LieBtrau/MegawattKS_Radio_Design_101/doc/RFampPwrGain.PDF

### RF Amplifier Power Gain

In radio frequency circuits, the power gain of an amplifier is often more important than the voltage gain. This paper covers calculation of power gain, and provides examples to illustrate important points.

Transducer Power Gain

The most commonly used definition of power gain is the so-called transducer gain GT defined as:

GT =

Ptoad
Pavail

where Pload is the power delivered to the load by the amplifier, and Pavail is the power available from the source. The latter is the same as the power delivered to the amplifier input by the source under the condition that the amplifier input impedance is matched to the source impedance
(i.e. Ri = Rs for the case of real impedances, or Zi = Z
*

s when working with complex impedances).

Assuming matched resistive impedances (Ri = Rs), the power available (power delivered to a matched amplifier input) can be written as:

Pavail = Pin−matched =

Vi

2
Ri

The power delivered by the amplifier's output to a load resistance RL (which may or may not be matched to the amplifier's output resistance Ro) is:

Pload =

VL

2
RL

Combining these two expressions, we find:

GT =

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
GT = AVloaded
2

Ri
RL

The maximum power will be delivered to the load by the amplifier if the load is matched to the amplifier's output impedance (ZL = Zo
*

), or, for the case of purely resistive output and load impedances, RL = Ro. Hence, the maximum transducer gain GTmaxoccurs when the output is matched as well as the input.

Examples:

Consider the case of a common-base amplifier with gm = 1/35 (Ri = 35Ohms), and Ro = RC = 1800 Ohms. Assume that the input is matched to the source (i.e. Ri = Rs ). The power gain for this amplifier under conditions of various load resistances is examined below.

Case 1: High impedance load

Suppose that the amplifier is hooked to a very high impedance load such as the input to an oscilloscope with RL = 10 MOhm. Then:

AVno-load = gm Rc = 1/35 1800 = 51.43
and
AVloaded = AVno-load | = 51.42 | (34.2 dB)* RL
RL+Ro

which is quite healthy. However, the power gain GT is found to be only:

GT = A
2
Vloaded | (-20 dB)* Ri
RL

= 51.4

2 35
10

7 = 0.01

Case 2: Low impedance load

Now suppose the amplifier output is connected directly to a piece of RF test equipment with a 50 Ohm input impedance. The loaded voltage gain is now:

AVloaded = AVno-load | (2.9 dB)* ⁵⁰
50+1800 = 1.39

which is quite low. The power gain in this case is also low:

GT = V
2
Vloaded | (1.3 dB)* Ri
RL

= 1.39

2 35
50 = 1.35

Case 3: Matched load

Finally, suppose that Ro is matched to RL (perhaps using an impedance matching network to transform a 50 Ohm load to 1800 Ohms). Then, the voltage and power gains are found to be:

AVloaded = AVno-load | = AVno-load | = 25.7 | (28.2 dB)* ¹⁸⁰⁰
1800+1800

1
2
and
GT = GTmax = A
2
Vloaded | (11 dB)* Ri
RL

= 25.7

2 35
1800 = 12.86

* Recall that voltage gain in dB is defined as 20 log (AV) and power gain in dB is 10 log (Gp).
The two are equal if and only if the input impedance equals the output impedance, which is not true here.
