LieBtrau/MegawattKS_Radio_Design_101/VFO/doc/Clapp Oscillator_ Frequency Formula And Circuit Diagram _ Electrical4U.pdf

## Clapp Oscillator: Frequency Formula And Circuit Diagram | Electrical4U

Electrical4U

Key learnings:

- Clapp Oscillator Definition: A Clapp oscillator (also known as a Gouriet oscillator) is defined as an LC electronic oscillator that uses an inductor and three capacitors to set the oscillator’s frequency.
- Frequency Formula: The frequency of the Clapp oscillator is determined by a specific formula that takes into account the values of the inductor and capacitors.
- Circuit Diagram: The circuit diagram of the Clapp oscillator includes an inductor, three capacitors, a transistor (or other gain element), and a positive feedback network.
- Role of Capacitor C3: The additional capacitor C3 makes the Clapp oscillator more stable than the Colpitts oscillator by allowing frequency variation without affecting the feedback ratio.
- Frequency Stability: Enclosing the circuit in a temperature-controlled chamber and using a Zener diode can enhance the frequency stability of the Clapp oscillator.

## What is a Clapp Oscillator?

A Clapp oscillator (also known as a Gouriet oscillator) is an LC electronic oscillator that uses a particular combination of an inductor and three capacitors to set the oscillator’s frequency (see circuit diagram below). LC oscillators use a transistor (or vacuum tube or other gain element) and a positive feedback network.

A Clapp oscillator is a type of Colpitts oscillator (https://www.electrical4u.com/colpitts-oscillator/) with an extra capacitor (C3) added in series with the inductor (https://www.electrical4u.com/what-is-inductor-and-inductance-theory-of-inductor/) in the tank circuit, as shown in the circuit diagram below.

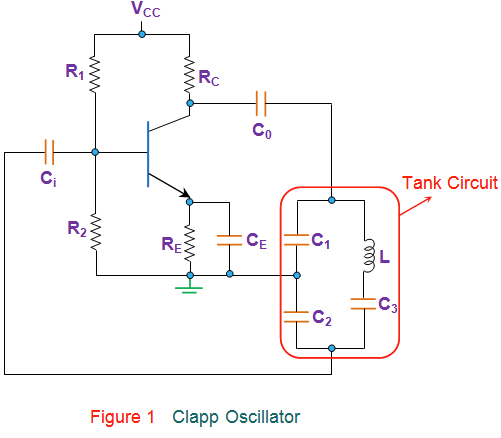
[picture p69: figure]

Apart from the presence of an extra capacitor, (https://www.electrical4u.com/working-principle-of-a-capacitor/) all other components and their connections remain similar to that in the case of Colpitts oscillator.

Hence, the working of this circuit is almost identical to that of the Colpitts, where the feedback ratio governs the generation and sustainity of the oscillations. However the frequency of oscillation in the case of a Clapp oscillator is given by

Usually, the value of C3 is chosen to be much smaller than the other two capacitors. (https://www.electrical4u.com/working-principle-of-a-capacitor/) This is because, at higher frequencies, the smaller the C3, the larger will be the inductor, (https://www.electrical4u.com/what-is-inductor-and-inductance-theory-of-inductor/) which eases the implementation as well as reduces the influence of stray inductance. (https://www.electrical4u.com/what-is-inductor-and-inductance-theory-of-inductor/)

Nevertheless, the value of C3 is to be chosen with utmost care. This is because, if it is chosen to be very small, then the oscillations will not be generated as the L-C branch will fail to have a net inductive reactance.

However, here it is to be noted that when C3 is chosen to be smaller in comparison with C1 and C2, the net capacitance governing the circuit will be more dependent on it.

Thus the equation for the frequency can be approximated as

Further, the presence of this extra capacitance (https://www.electrical4u.com/what-is-capacitor/) will make the Clapp oscillator preferable over Colpitts when there is a need to vary the frequency

Clapp Oscillator: Frequency Formula And Circuit Diagram | Electrical4U | https://www.electrical4u.com/clapp-oscillator/
1 of 2 | 2025-08-27, 16:45

as is the case with Variable Frequency Oscillator (VCO). The reason behind this can be explained as follows.

In the case of the Colpitts oscillator, (https://www.electrical4u.com/colpitts-oscillator/) the capacitors C1 and C2 need to be varied in order to vary their frequency of operation. However during this process, even the feedback ratio of the oscillator (https://www.electrical4u.com/what-is-an-oscillator/) changes which in turn affects its output waveform.

One solution to this problem is to make both C1 and C2 to be fixed in nature while achieving the variation in frequency using a separate variable capacitor.

As could be guessed, this is what the C3 does in the case of the Clapp oscillator, which in turn makes it more stable over Colpitts in terms of frequency.

You can further improve the circuit’s frequency stability by placing it in a temperature-controlled chamber and using a Zener diode (https://www.electrical4u.com/what-is-zener-diode/) to maintain a constant supply voltage. (https://www.electrical4u.com/voltage-or-electric-potential-difference/)

Additionally, the values of capacitors C1 and C2 are affected by stray capacitances, unlike C3.

This means that the resonant frequency of the circuit would be affected by the stray capacitances if one had a circuit with just C1 and C2, as in the case of Colpitts oscillator.

However, if there is C3 in the circuit, then the changes in the values of C1 and C2 would not vary the resonant frequency much, as the dominant term would then be C3.

Next, it is seen that the Clapp oscillators are comparatively compact as they employ a relatively small capacitor (https://www.electrical4u.com/working-principle-of-a-capacitor/) to tune the oscillator over a wide frequency band. This is because, here, even a slight change in the value of the capacitance varies the frequency of the circuit up to a great extent.

Further, they exhibit a high Q factor (https://www.electrical4u.com/q-factor/) with a high L/C ratio and lesser circulating current (https://www.electrical4u.com/electric-current-and-theory-of-electricity/) in comparison with Colpitts oscillators. (https://www.electrical4u.com/colpitts-oscillator/)

Lastly, it is to be noted that these oscillators (https://www.electrical4u.com/what-is-an-oscillator/) are highly reliable and are hence preferred in spite of having a limited range of frequency of operation.

Clapp Oscillator: Frequency Formula And Circuit Diagram | Electrical4U | https://www.electrical4u.com/clapp-oscillator/
2 of 2 | 2025-08-27, 16:45
