LieBtrau/MegawattKS_Radio_Design_101/IF1_amp/doc/Cascode.pdf

1

## The Cascode Amplifier

A two transistor amplifier used to obtain simultaneously:
1. Reasonably high input impedance.
2. Reasonable voltage gain.
3. Wide bandwidth.

None of the conventional single transistor designs will satisfy all of the criteria above.
The cascode amplifier will satisfy all of these criteria.
A cascode is a CE Stage cascaded with a CB Stage.

(Historical Note: the cascode amplifier was a cascade of grounded cathode and grounded grid vacuum tube stages – hence the
name “cascode,” which has remained in modern terminology.)

## The Cascode Amplifier

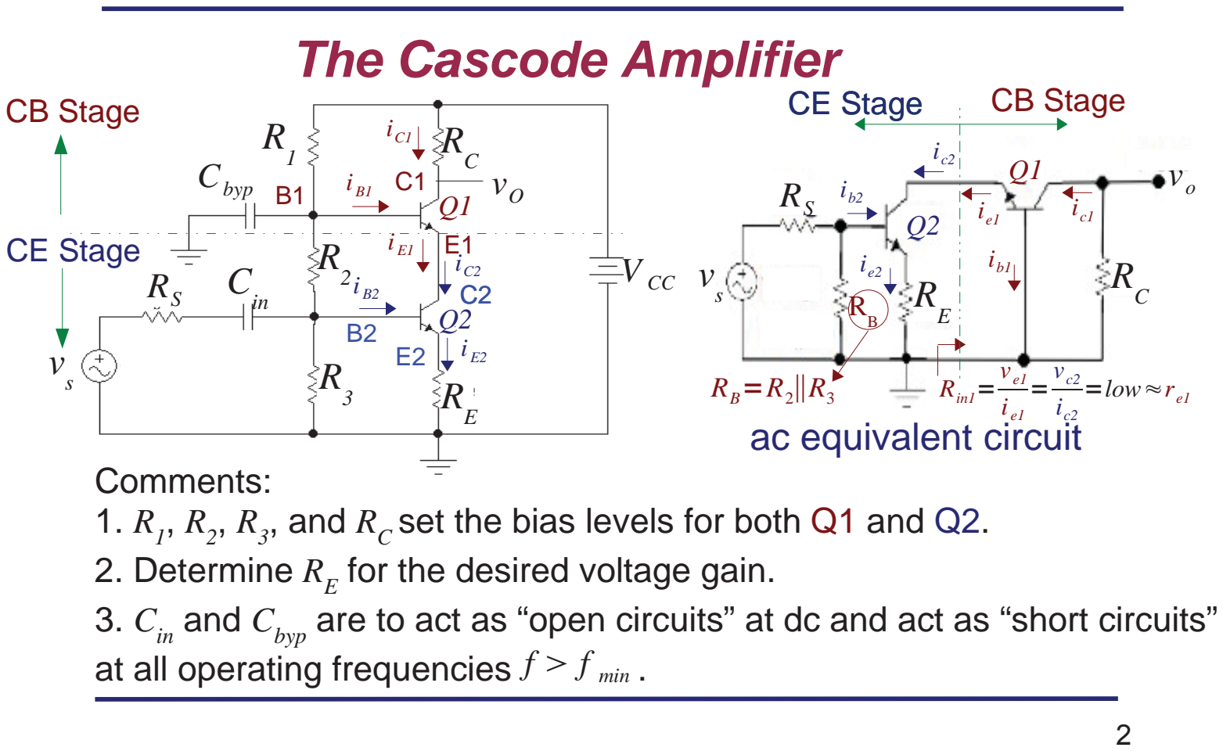
[picture p78: page 2]

2

f

f min

ac equivalent circuit

ib2

ie2

ic2

ic1

ib1

ie1

Rin1

ve1

i e1

vc2

ic2

low
r e1

R
B

R
B
R
2

R3

CE Stage CB Stage

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
CE Stage

Q2

Q1
R
S
i | v-out B1

i B2

i E1
iC2

i E2
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
V CC

Cbyp

CB Stage

CE Stage

B1 | C1

E1

C2

| E2

B2

Q1

Q2

R
S

iC1

Comments:
1.
R

1, R

2, R

3, and
R

C set the bias levels for both Q1 and Q2.
2. Determine
R

E for the desired voltage gain.
3.
Cin and

Cbyp are to act as “open circuits” at dc and act as “short circuits”
at all operating frequencies | .

## Cascode Mid-Band Small Signal Model

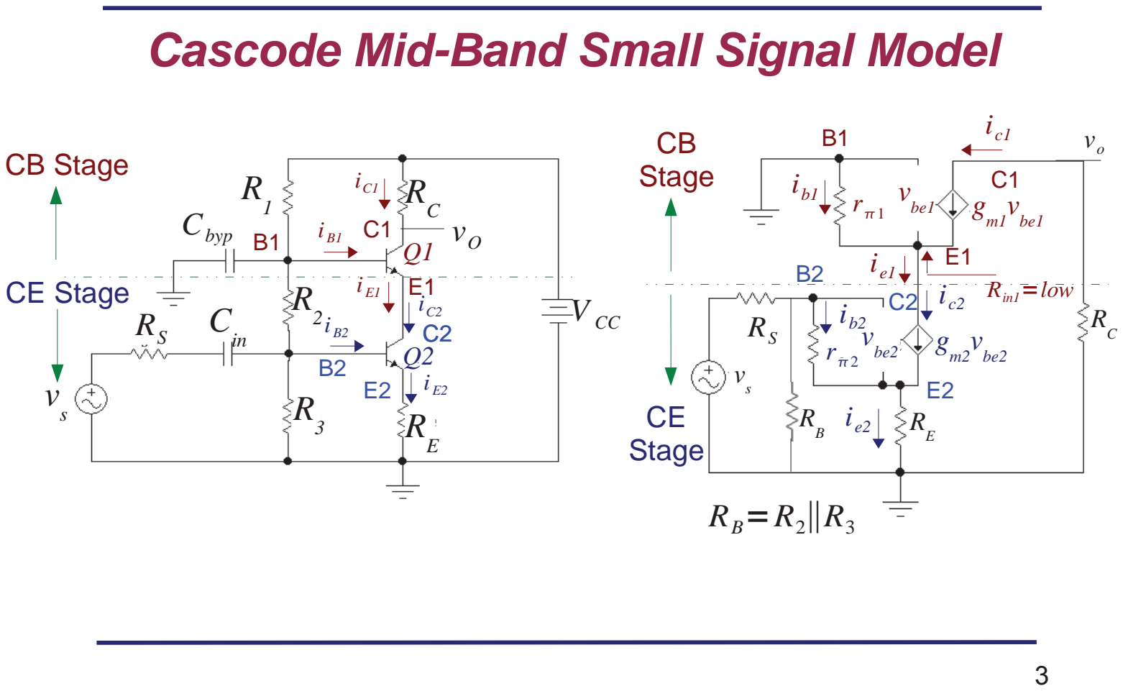
[picture p79: page 3]

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
Rin1

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
1 | g
m

v
1

g
m

v
2

v CB
o
Stage

CE
Stage

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
i | v-out B1

i B2

i E1 iC2

i E2
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
V CC

Cbyp

CB Stage

CE Stage

B1 | C1

E1

C2

| E2

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
## Cascode Small Signal Analysis

ie1

ic2

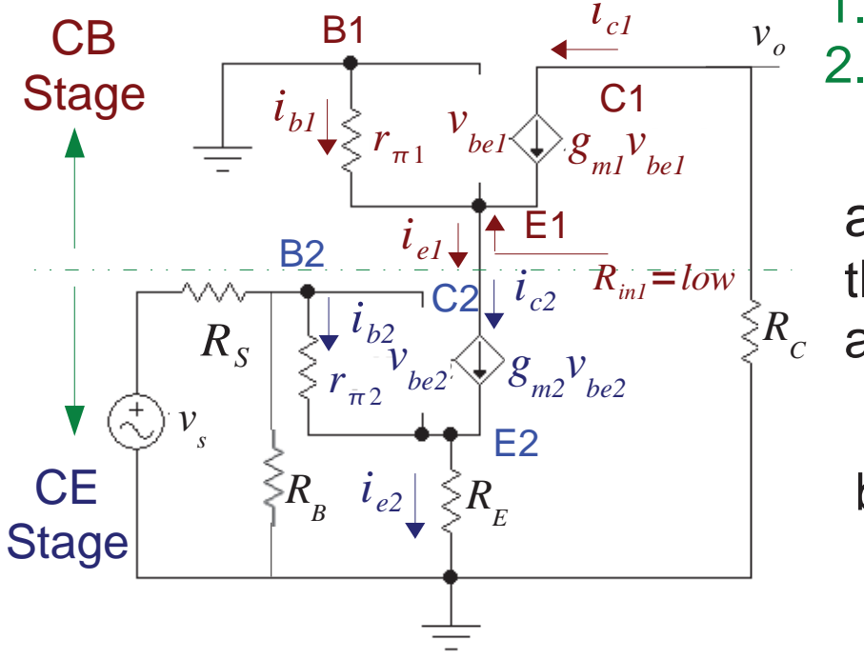
[picture p80: figure]
Rin1; low; Stage; CE Stage

b. The base current of the CB Stage is:
c. Hence, both stages have about same collector current and same
g
m, re, rπ

ib1

ie1
1

ic2
1

OBSERVATIONS

ic1

ic2

gm1

g m2
g
m
re1
r e2
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
a. The emitter current of the CB Stage is the collector current of the CE Stage. (This also holds for the dc bias current.)
1. Show reduction in Miller effect
2. Evaluate small-signal voltage gain

5

Cascode Small Signal Analysis cont.

ib1

ie1
1

i c2
1
The CE output voltage, the voltage drop from Q2 collector to ground, is:

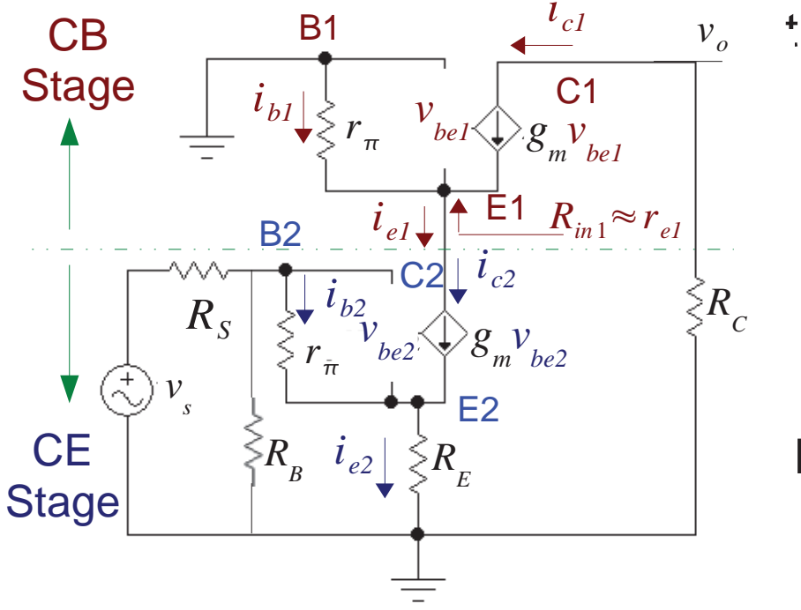
[picture p81: figure]
Stage; CE Stage; Rin 1

Therefore, the CB Stage input resistance is:

Rin1

ve1
ie1

r
1
r e1

vc2

ve1-

r

ib1-

r
1

ic2-

r
1

ie1

AvCE
Stage

vc2
v
s

Rin1
R
E

r
e
R
E
1 =>
Ceq-
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
The input resistance
R
in1

to the CB Stage is
the small-signal “
r
e1

” for the CB Stage, i.e. ic1

Cascode Small Signal Analysis - cont.

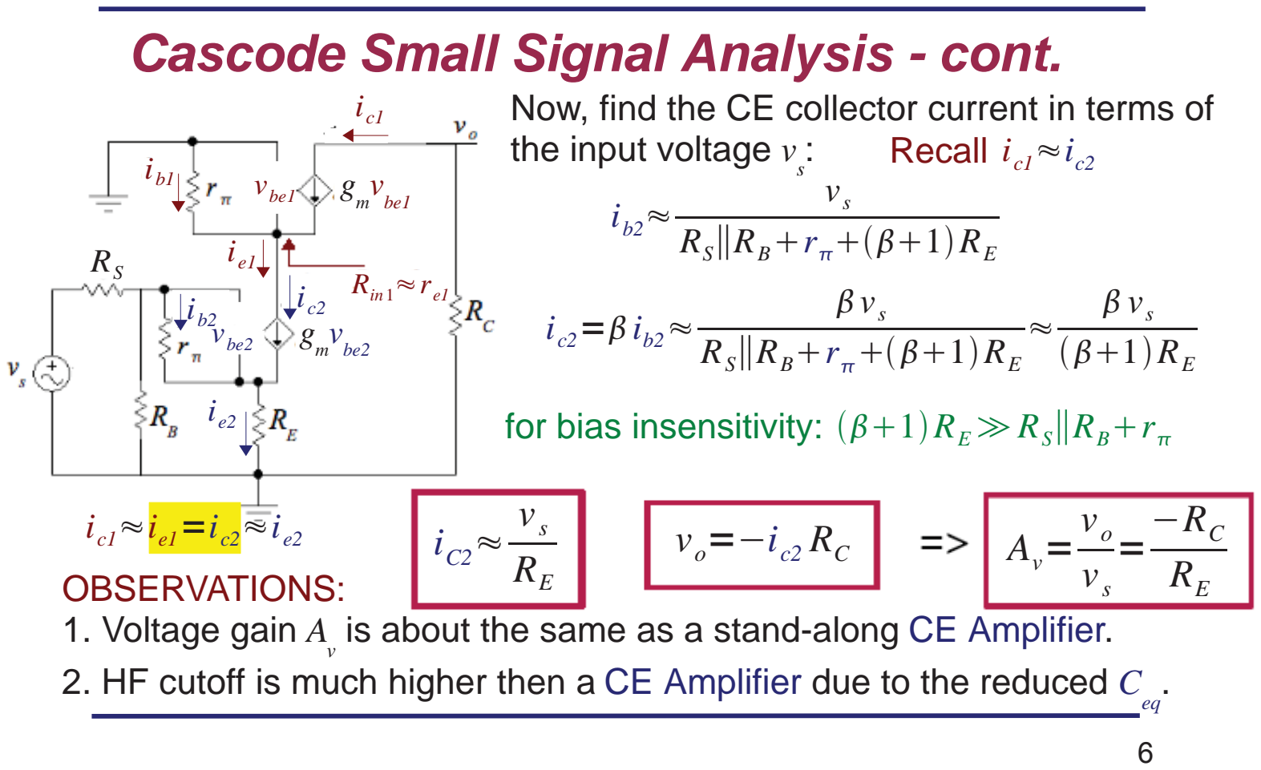
[picture p82: page 6]

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
ic2-

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
Now, find the CE collector current in terms of the input voltage
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
r for bias insensitivity:

ic1

i Recall c2

OBSERVATIONS:
1. Voltage gain
A

v is about the same as a stand-along CE Amplifier.
2. HF cutoff is much higher then a CE Amplifier due to the reduced C

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
vbe1

vbe2

g
m

vbe1

g
m

v
vbe2 | be2

vbe1

R
S

ic1

ie1
ic2
ie2

Rin 1
r e1

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
i i | c2 b2

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
## Cascode Biasing

Rin1-

r e-

VT I E1

1. Choose IE1 – make it relatively large to
reduce | to push out HF

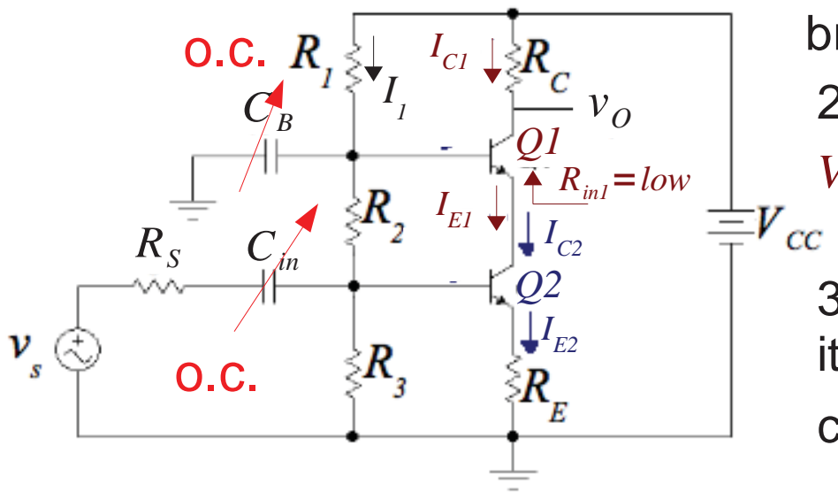
[picture p83: figure]
Rin1-; low; Cin

break frequencies.
CB | 2. Choose RC for suitable voltage swing
V
C1

and RE for desired gain.

3. Choose bias resistor string such that its current I
1

is about 0.1 of the collector current I
C1

4. Given RE, IE2 and VBE2 = 0.7 V calc. R3.
5. Need to also determine R
1

& R
2

2 I E2-

I C2-

I E1-

1
1

I C1 I C1I E2

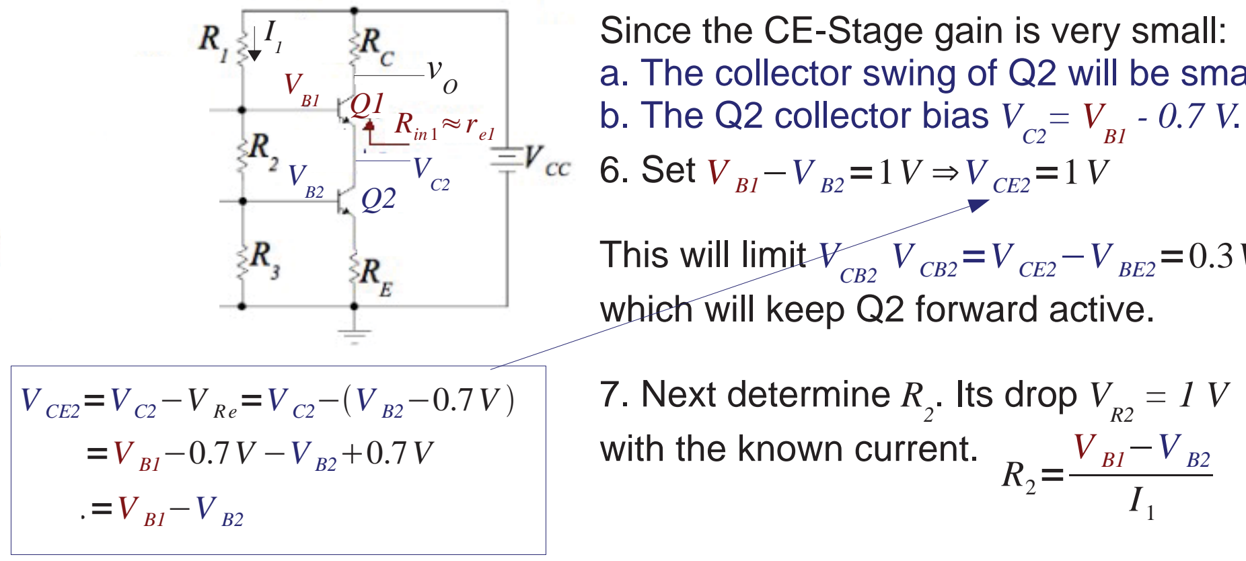
[picture p84: figure]
Since the CE-Stage gain is very small:; b. The Q2 collector bias; 6. Set; This will limit; V CB2 which will keep Q2 forward active.; 7. Next determine; 2. Its drop; with the known current.; Rin 1

8

Cascode Biasing - cont.

a. The collector swing of Q2 will be small.

V

9

Cascode Biasing - cont.

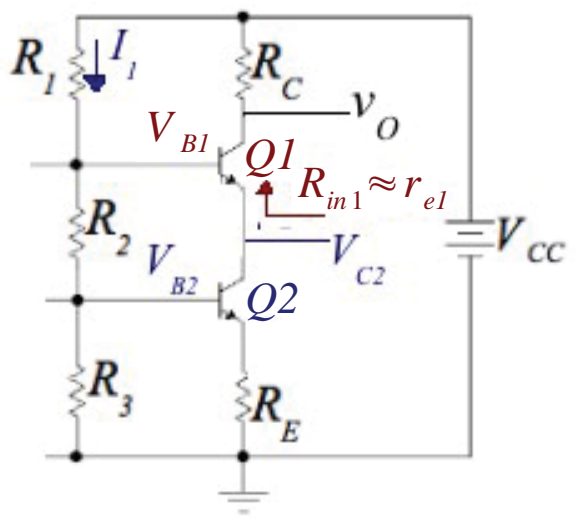
[picture p85: figure]
Rin 1

8. Then calculate
R
3

R
2

V B1

V B2
I 1

1

V
I 1
R
3

V B2
I 1
where
V B2
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
V CC
I 1

Note:

9. Then calculate
R
1

R1-

V CC
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
## Cascode Bias Summary

SPECIFIED:
A
v

,
V

CC,

V

C1 (CB collector voltage); SPECIFIED: IE (or
I
C) directly or indirectly through BW. DETERMINE:
R

C, R

E, R

1, R
2

and
R
3
SET:

R
C

V C1
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
V CC
I 1

V CC
0.1

I
C

V B1

V B2
1

V

V CE2
1

V

R
3

V B2
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
V B1

V B2
I 1

1

V
0.1

I
C

R1-

V CC
0.1

I
C
R
2
R
3

STEP1:

STEP2:

STEP3:

STEP4:

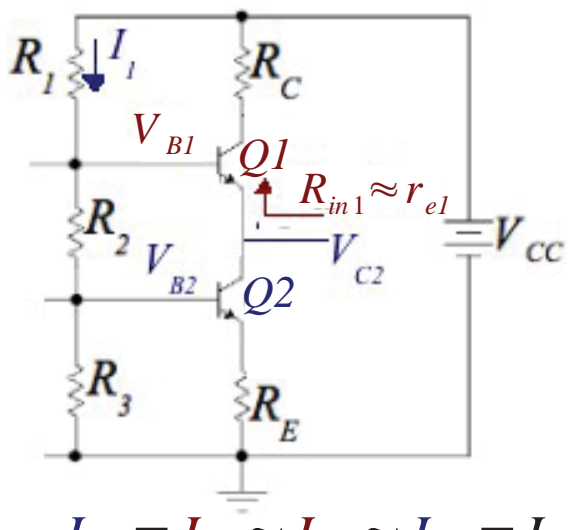
[picture p86: figure]
Rin 1

I C2

I E1
I C1
I E2
I
C

## Cascode Bias Example

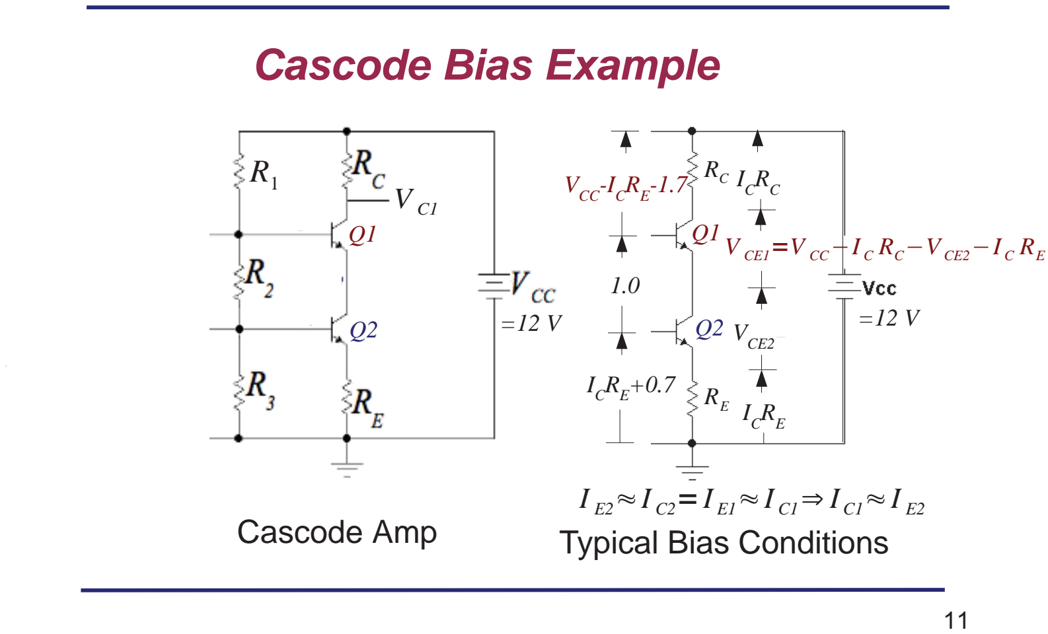
[picture p87: page 11]

11

Cascode Amp
Typical Bias Conditions

ICRE

ICRC

ICRE+0.7

VCE2=1

VCE1=ICRC–1–ICRE
1.0

VCC-ICRE-1.7

=12 V

I E2I C2-

I E1I C1 I C1I E2

=12 V

RC

RE

V CE1-

V CCI C RCV CE2I C RE

V C1
Q1 | Q1
Q2 | Q2

R1

12

Cascode Bias Example cont.

1. Choose
IE1 – to set
re
Try
I
E1
= 5 mA => | .
2. Set desired gain magnitude. For example if
A
V

= -10, then
R

C/R

E = 10.

3. Since the CE stage gain is very small, VCE2 can be small, i.e.
V
CE2

=

VB1 –

| VB2 = 1 V.

r
e
0.025

V

I
E
5

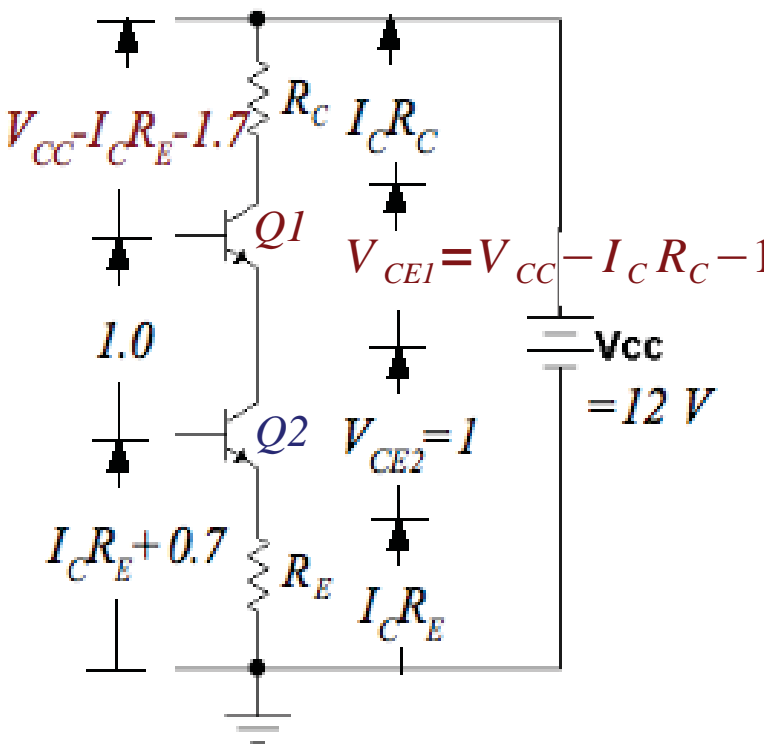
[picture p88: figure]

1

I
C

R
E

13

Cascode Bias Example cont.

I
C

5mA A

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
V CC

V C1
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
1000

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
Determine
R

C for
V
C1

= 7V .

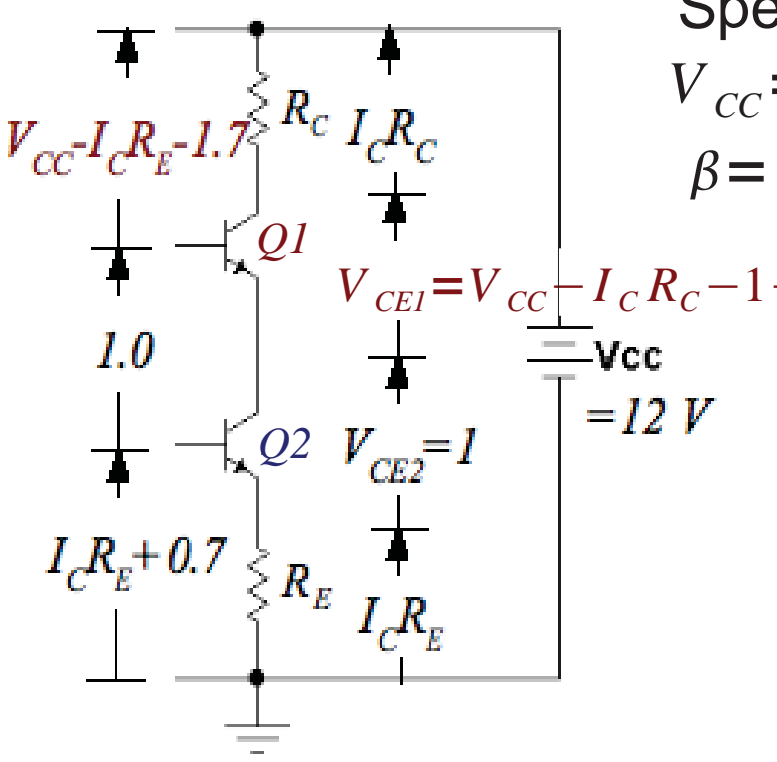
[picture p89: figure]

12

V

I
C

R
E

V C1

7

V

Specs:

100

14

Cascode Bias Example cont.

V CC

12

I
R
C
5mA.
C
1

k

R
E
100

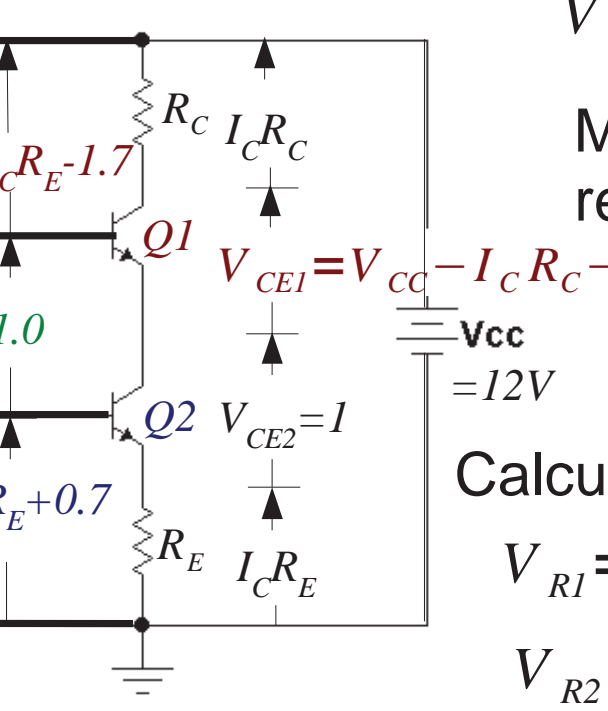
[picture p90: figure]
VCE2=1; VCE1=ICR; C–1–ICR E

Make current through the string of bias resistors
I
1

= 0.1 IC = 0.5 mA.

R1

R
2

R
3

V CC
I 1

12
510
4
24

k

V R3

V B2
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
V CC
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
VCC-ICR

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
Calculate the bias voltages (base side of Q1, Q2):

V B1
V B2
1

V

15

Cascode Bias Example cont.

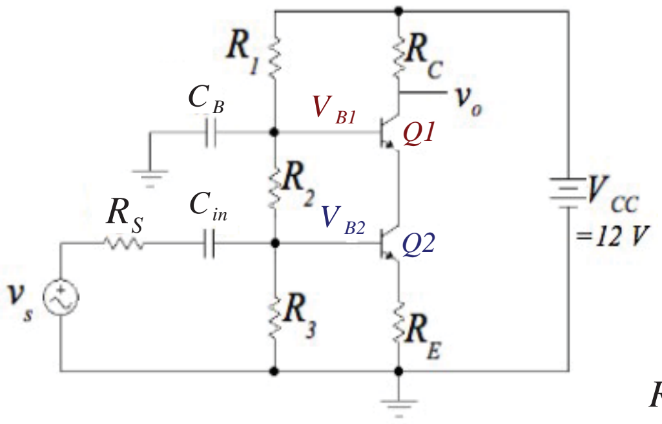
[picture p91: figure]
Cin

V CC

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
V B2

1.2

V

V B1

V B2
1.0

V

V B2

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
V B1

V B2

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
R1-24000

2.400

2000

19.6

k

Recall:
R1

R
2

R
3
24

k

, | , | ,
, | ,

16

## Completed Design

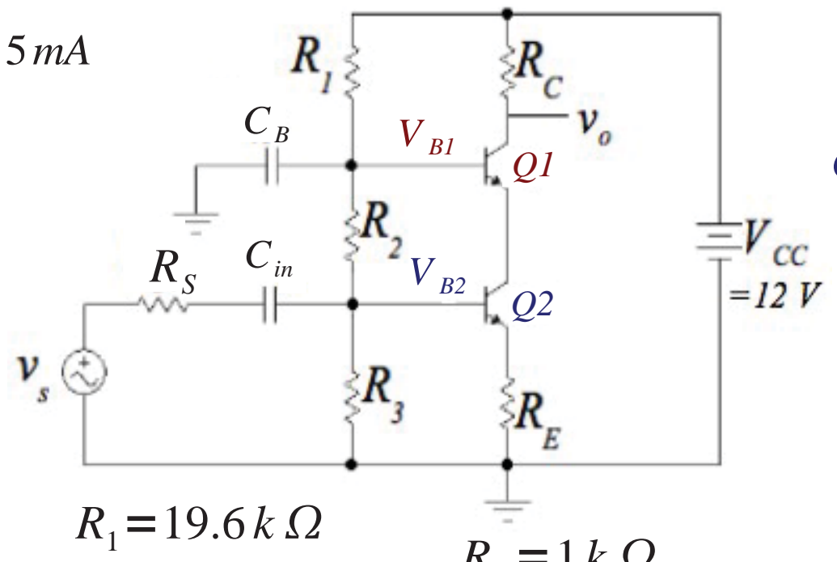
[picture p92: figure]
V B2 Cin

R2-

2 k
R3-

2.4 k

RC-

1k
RE-

100

V C1-
7V

re-

5I C-

Av-

RC RE -10

f Hcascode-
225.8 MHz

Ctot-
14.1 pF

C

1.05C
If C
π = 12 pF
C
μ = 2 pF

Ctot-
C

1

re RE C

f H-

1 2Ctot RS'

f HCE-
94 MHz

For CE with |Av| = 10

RB-

R2R3-

1.09 k RE-

10 k

-100

NOTE:
