LieBtrau/MegawattKS_Radio_Design_101/post_mixer_amplifier/doc/fba_with_simple_model.pdf

### The Feedback Amplifier with a Simple Model

Wes Hayward, w7zoi, 30May, 1June, 9June, 16June 2009 (Figure captions are in blue.)

### Equations Derived

This derivation starts with a transistor described as a voltage controlled current generator with very high transconductance, gm

. Reality as well as current dependence are retained by inserting emitter degeneration.

Assume a voltage controlled current source with very high transconductance gm

. The
controlling voltage is that between the base and emitter. The collector current is just i
c

gm Vbe ·
where Vbe Vb

Ve

Basic Model

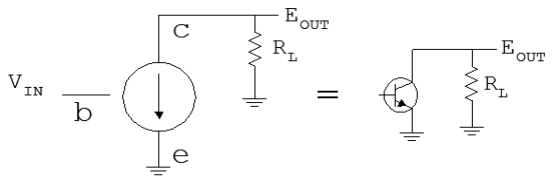
[picture p100: figure]

A common emitter amplifier with this model. The current in the CE collector flows through the load. Taking note of the polarity indicated by the arrow, the voltage at the collector is
Eout -gm Vbe · RL

·
The voltage gain is then

Gv

Eout Vbe | -gm RL ·

Adding Emitter Degeneration

Common emitter amplifier with degeneration rd.

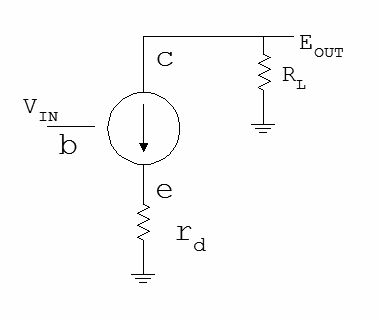
[picture p101: figure]

Note that Vin does not equal Vbe. Expanding the earlier equation,

i gm Vb

Ve

·( - ) gm Vb
- gm Ve
- ·

But
Ve

i r
d

·
(without inversion). Substituting this,

Ve

i r
d

·
i 1 gm r
d
·( + | · ) gm Vb ·
i | gm Vb

·

1 gm r

d ( + · )

Calculate the transconductance of this overall cell, which we define as upper case Gm

i Gm Vb

·

Gm

gm
1 gm r
d

+ ·
Dividing top and bottom by gm

,

Gm

1
1 gm | r d
+

The limit of this expression as gm

becomes very large is

Gm

1
r
d
Extending the earlier analysis, the amplifier voltage gain becomes

Gv

-Gm RL

·

RL

r
d
The device transconductance does not really matter so long as gm

is large, ( gm

>>1/r
d

).

Current Dependence

Recall the parameter r
e

=26/I
e

from the basic physics of the junction transistor. I
e

here is
emitter current in mA. The simplest small signal model for a bipolar transistor is then an infinite transconductance amplifier that is then degenerated by an intrinsic resistance re. Beta ( β ) does not appear as a parameter and the circuit is voltage driven. This does not imply that no current flows in the input, for it does and is related to collector current with β. Rather, this is just the simple model used in this discussion. Voltage drive describes many of the salient properties of the bipolar transistor, making this the generally accepted, simplest level bipolar transistor model.

The degeneration in the above equations is described by rd, which is external to the current source, but we then introduce re as a degeneration that describes the intrinsic transistor. In practice, we usually use a combination, upper case Rd, which is just the sum of the internal and external degenerations, re and rd.

Adding Parallel Feedback

Degeneration is one form of feedback. Consider now an amplifier with a small signal transconductance Gm

. We use the upper case Gm

in this case to emphasize that we may well have a high gain transistor that is degenerated by a resistance. We introduce parallel feedback as a resistor from the output terminals back to the input. The arrows show assumed directions of current used in forming equations. A 1 volt source drives the input.

Amplifier with parallel feedback. Degeneration may

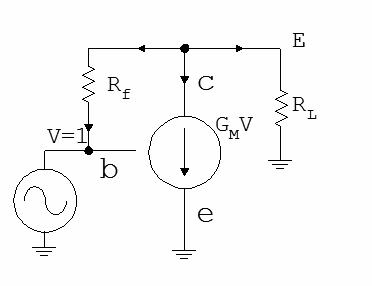
[picture p102: figure]

also be present.

All current is out of the collector node, so

0 Gm

(E - 1)
Rf

+

E
RL

+

Solving this for the voltage “E” yields

E

Gm

Rf

-( · - 1)

RL

Rf ( + )

RL

·

Voltage gain is defined as

Gv

E
V
and V=1, so

Gv

Gm

Rf

-( · - 1)

RL

Rf ( + )

RL

·

We now ask for the input impedance. This is calculated from the input voltage, 1, and the input current.

i
in

E - V
Rf

E - 1
Rf

Zin

1
i
in

Rf
E - 1
Substitute E from the above analysis to find Zin.

Zin

Rf
E - 1

Rf
Gm Rf

-( · - 1)

RL

Rf ( + )

RL

- - 1

RL

Rf

-( + )
RL ( ·Gm + 1)

This impedance is negative, but that is merely the result of the arbitrary current direction assumed above. Change the sign to fit with current into the amplifier from the external source to obtain

Zin

RL

Rf ( + )

RL

·Gm + 1
Next, we wish to calculate the output impedance. The output is driven with a 1 volt generator while terminating the input in a source resistance RS. The input voltage at the base is then obtained by voltage divider action.

Setup for calculation of output impedance.

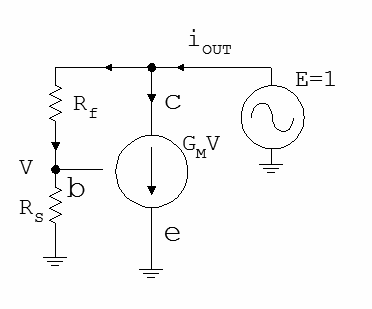
[picture p103: figure]

V

E RS

·

RS

Rf

+
This allows calculation of collector current.

i
c

Gm·V Gm

E RS

·

RS

Rf

+

·

The current into the collector node, i

out, is then obtained. One current flows into the collector node and two flow out of the node. The nodal equation is

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
1 Gm

RS ( + · )

Rf

RS

+
The output impedance, which is just the Z looking into the output port, becomes

Zout

E
i
out

Rf

RS

+
| 1 Gm RS ( + | · )
Rather than using Gm

for our calculations, we will now express it in terms of degeneration. From the early analysis,

Gm

1
Rd | and | Rd

r
d

r
e

+
An upper case Rd

is used to emphasize that it could and often is the sum of an external degeneration and the internal r
e

. Manipulation yields

Gv

RL

- Rf
Rd

·( - )

Rd

RL

Rf

·( + )

Zin Rd

RL

Rf ( + )

RL

Rd ( + )

- Zout

Rd

Rf

RS

·( + )

Rd

RS ( + )

Matched Impedances

What are the conditions for an impedance match? At the input port

RS

Rd

RL

Rf ( + )

RL

Rd ( + )

·
Solving this for the degeneration resistance Rd,

Rd

RS

RL
RS
- RL
+ | Rf ( | + )

·

This defines the parameters that will produce an input match for any arbitrary load, source, and feedback resistor. If RS

=RL

then this collapses to the familiar form:

Rd

Rf

- RS
RL

·
A similar analysis at the output port will produce the same equation that defines that match, so Rd Rf=RS RL defines a simultaneous match at both ports, for the special case of
RS

=RL

. This relationship is otherwise just an approximation.

Transducer Gain

We now calculate the transducer gain of the amplifier, as shown in this circuit.

Circuit used to calculate Gt which is defined as

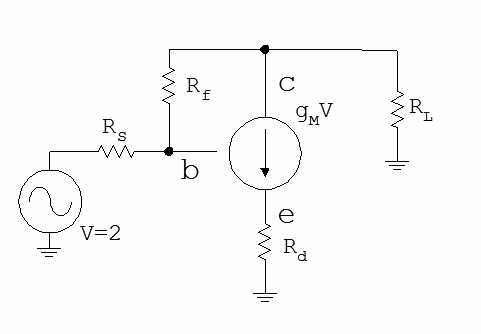
[picture p104: figure]

the output power divided by the power available from the source. The driving source is a generator with a 2 volt open circuit strength.

The driving generator has an open circuit strength of 2 volts. If a 2 volt source with source impedance R is terminated in an equal R, the result will be 1 volt across that impedance. This leads to straight forward calculations of available power, 1/RS. This is detailed in the figure below.

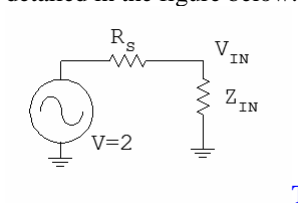
[picture p105: figure]

The input base signal is calculated by knowing Zin and Rs.

The input impedance was found earlier.

Zin Rd

RL

Rf ( + )

RL

Rd ( + )

·

The 2 volt source will be divided by this and the source.

Vin

2 Zin ·

Zin RS

+
which becomes

Vin 2 Rd

·

RL

Rf ( + )

Rd

RL

- Rd
Rf
+ | · | RS
RL
+ | · | RS
Rd ( | + | · )

·

This signal is amplified by the voltage gain.

Gv

RL

- Rf
Rd

·( - )

Rd

RL

Rf

·( + )

E Gv

Vin ·

RL

- Rf
Rd

·( - )

Rd

RL

Rf

·( + )

2 Rd

·

RL

Rf ( + )

Rd

RL

- Rd
Rf
+ | · | RS
RL
+ | · | RS
Rd ( | + | · )

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
E Gv

Vin · -2 RL

·

Rf

Rd ( - )

Rd

RL

- Rd
Rf
+ | · | RS
RL
+ | · | RS
Rd ( | + | · )

·

Calculate the output power.

Pout

E

2

RL

-2 RL

·

Rf

Rd ( - )

Rd

RL

- Rd
Rf
+ | · | RS
RL
+ | · | RS
Rd ( | + | · )

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
Pout

E

2

RL

4 RL

·

Rf

Rd ( - )
2

Rd

RL

- Rd
Rf
+ | · | RS
RL
+ | · | RS
Rd ( | + | · )
2

·

The available power from the source is

Pav

1
RS
Hence, transducer gain is

Gt

Pout
Pav

4 RL

- RS
- Rf

Rd ( - )
2
·

Rd

RL

- Rd
Rf
+ | · | RS
RL
+ | · | RS
Rd ( | + | · )
2
This is usually expressed in dB form rather than as a simple power ratio,

Gt

10 log

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
éêêë

ùúúû
·
dB
