LieBtrau/MegawattKS_Radio_Design_101/VFO/doc/002401269.pdf

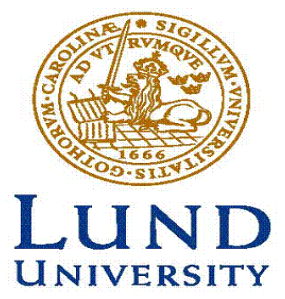
[picture p106: figure]

# Local Oscillator for FM broadcast band 88-108 MHz

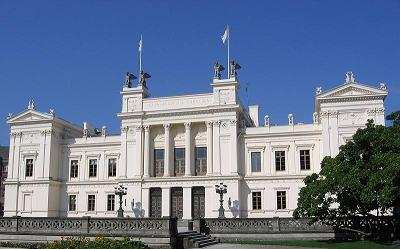
[picture p107: figure]

Wang Luhao

Yan Shubo

Supervisor: Göran Jönsson

Department of Electrical and Information Technology

Lund University

2012.05.15

Local Oscillator for FM broadcast band 88-108 MHz

### Abstract

In this project describes the design work of the local oscillator for FM broadcast

band 88MHz to 108MHz, Our design is implemented by using the Clapp oscillator

configuration. The frequency can be tuned by voltage control of varactor BBY40. And

the measurement results are also involved in the project.

### Contents

### 1. Introduction

The oscillator is of great importance in the superheterodyne receiver system.

Figure 1.1 shows the block diagram of the superheterodyne receiver. In our design,

the FM broadcast band is 88- 108MHz, in order to mix down to the IF frequency

(10.7MHz), the frequency tuning range in our design is from 98.7MHz to 118.7MHz.

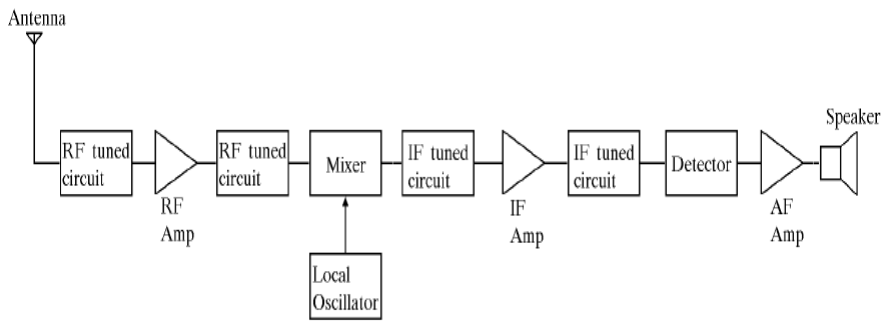
[picture p108: figure]

Figure 1.1 The superheterodyne receiver block diagram

### 1.1 Basic of Oscillators

To be able to analyze the oscillating conditions Black’s feedback model is used.

Here the oscillator is split into two blocks. One amplifier which is considered to be

wideband and one feedback network that is usually frequency selective.[1]

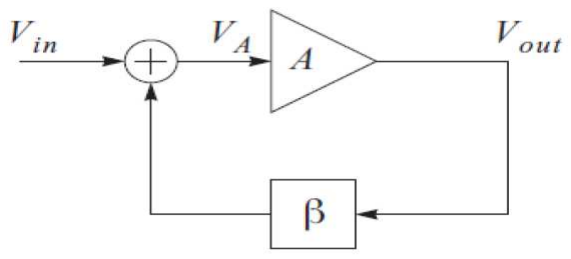
[picture p109: figure]

Figure 1.2 Black feedback model for oscillator

The transfer function for the amplifier with feedback can be calculated using the

following equation.
Vout = A ⋅VA

VA = Vin + β ⋅Vout ⇒ Af =

Vout

Vin

=

A
1− β ⋅ A

If | and | , the feedback gain | will become infinite. And

the system will perform continuous oscillation.

There are some configurations of oscillators: Colpitt, Hartley and Clapp

Oscillator which is shown in figure 1.3.

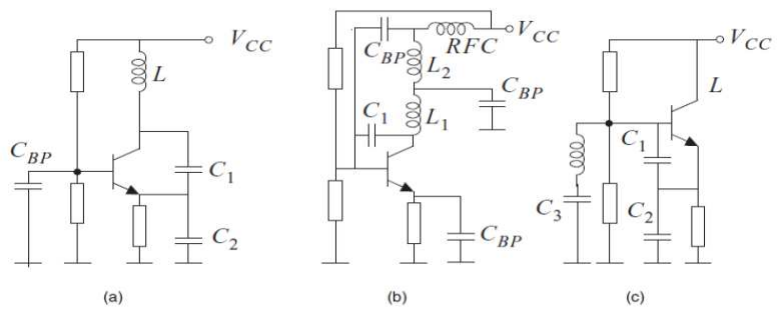
[picture p110: figure]

Figure 1.3[2] Oscillator configurations: (a) Colpitts (b) Hartley (c) Clapp

Colpitts Oscillator with its feedback path through a capacitive voltage divider

where two capacitors and one inductor determine the frequency of oscillation, see

figure 1.3 (a). Hartley Oscillator use two series-connected coils and a single

capacitor. The feedback can be through an inductive tap, see figure 1.3(b).

Clapp oscillators preferred over a Colpitts circuit for constructing a variable

frequency oscillator. In a Colpitts Oscillator, the voltage divider contains the variable

capacitor (either C1 or C2). This causes the feedback voltage to be variable as well,

sometimes making the Colpitts circuit less likely to achieve oscillation over a portion

of the desired frequency range. This problem is avoided in the Clapp circuit by using

fixed capacitors in the voltage divider and a variable capacitor in series with the

inductor[2]

### 1.2 Specification

The Local Oscillator is used for a super heterodyne receiver. The tuning is

voltage controlled. The specification is given as following.

1. Supply Voltage is 12V.
2. The oscillator frequency should be variable for reception of a specified
A⋅ β = 1 | ∠(A ⋅β) = 0° | Af

Local Oscillator for

frequency band 88

3. Any harmonics should be at least
4. Minimum output power should be 8 dBm.

### 2. Circuit design

The local oscillator system

oscillator, the buffer and the low pass filter. The

Figure 2.1.

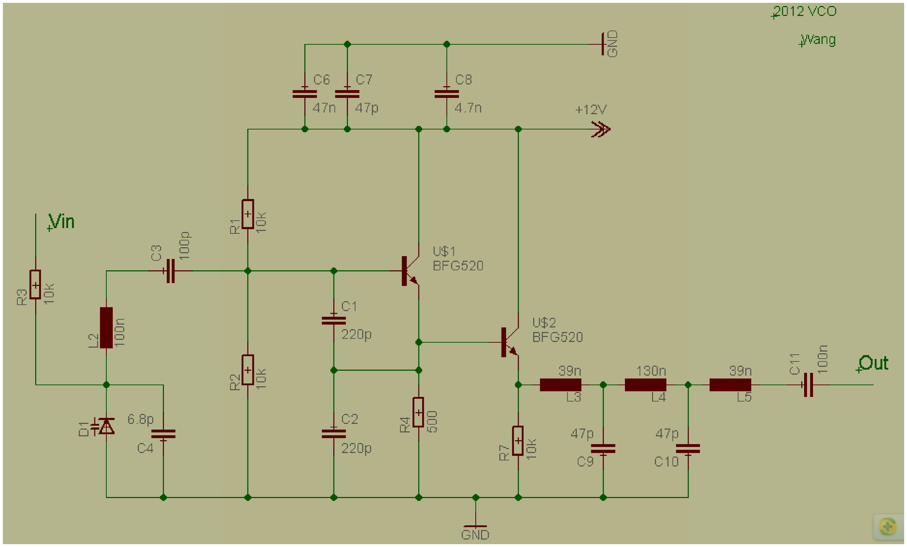
[picture p111: figure]

Figure

### 2.1 Voltage Controlled

A voltage controlled oscillator

variable or tuning element is a

diode to vary the capacitance applied to the tuned circuit

tuning range.

In our system, we use the bipolar BFG520 in the

configuration. And a variable capacitance diode nam

frequency tuning from 98.7MHz to 118.7MHz

across the varactor to make the tuning range to that required

FM broadcast band 88-108 MHz

-108 MHz.

-16 dBc and other spurious at least

system we designed can be divided into three parts:

schematic of the system is shown in

2.1 the schematic of the oscillator system

Oscillator

(VCO), is an oscillator where the principal

varactor diode. (http://www.electronics-tutorials.com/basics/diodes.htm) DC voltage applied to th

capacitance applied to the tuned circuit in order to get the desired

clapp structure with collector

ed BBY40 is use to

. And a fixed capacitance

make the tuning range to that required.

-70 dBc.

the

e varactor

achieve the

is added

And the oscillator frequency can be written by:

We choose the inductance L=100nH, then the total capacitance can be determined.

The varactorBBY40 is controlled by the control voltage and its characteristic is shown in Figure 2.2.

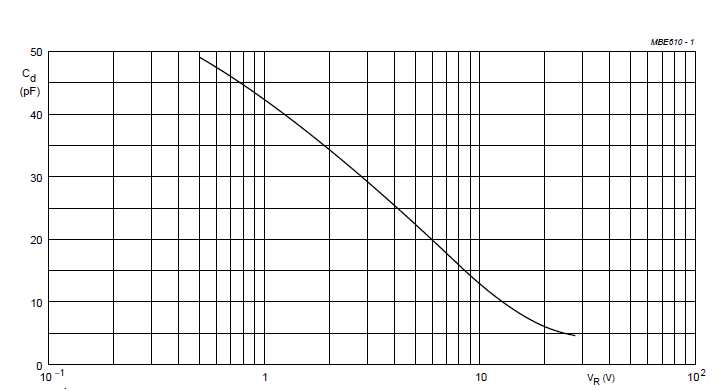
[picture p112: figure]

Figure 2.2 Diode capacitance as a function of reverse voltage; typical values [3]

According to its characteristics, we choose-

, and then the range of the

varactor and the control voltage which can be determined:

For its biasing,

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
C4 + Cvar

Ctot min =

1
(2π fmax )

2
L

=

1
(2π × 118.7 × 10⁶
)

2

× 100 × 10⁻⁹

= 18 pF

Ctot min =

1
(2π fmin )

2
L

=

1
(2π × 98.7 × 10⁶
)

2

× 100 × 10⁻⁹

= 26.03pF

C4 + Cvar min =

1
1

Ctot min

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
= 27.42 pF

C4 + Cvar max =

1
1

Ctot max

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
= 57.74 pF

Cvar ∈(20.62 pF, 44.9 pF)
Vcontrol ∈(0.8V,6V)

### 2.2 Buffer Amplifier

A buffer amplifier at the output is necessary to isolate the VCO from any output

load variation and provide the required output power.

In our design, we used the collector configuration as the buffer amplifier. As we

calculated above, the emitter voltage of the first stage is 6V-0.7V=5.3V, which is high

enough to drive this buffer stage. So we connect the emitter of the oscillator transistor

to the base of the buffer amplifier without adding any other biasing circuit.

### 2.3 Low Pass Filter

The low pass filter is used for harmonic rejection. And we use the Butterworth

filter. Its amplitude function fulfils:

Where n is the order of the filter and

is a normalization frequency.

The tuning frequency range of the oscillator is from 99.7MHz to 118.7MHz. And

in the pass band the amplitude should be equal to or higher than -2dB up to

118.7MHz.

And the rejection band is defined by the -20dB corner at 200MHz.

Combining the results from the two corner we get n=5. According to the

Butterworth Ladder Filters table, we can get:

VB =

10K
10K +10K

×12V = 6V

IE =

VB − 0.7
500

= 10.6mA

A( f ) =

K

1+ (

ω
ωo

)

2n

=

K

1+ (

f
f
o

)

2n

A(118.7 × 10⁶
) =

K

1+ (

118.7 × 10⁶
f
o

)

2n

= −2dB = 0.7943

A(200 × 10⁶
) =

K

1+ (

200 × 10⁶
f
o

)

2n

= −20dB = 0.1

Thus, we can calculate the value of each component:

### 3.Simulation

Before the implementation, we try to simulate the circuit by using ADS 2011.

Figure3.1 shows the results around 100MHz, and the output power is 9.324dBm and

theneighboring harmonic is only about -22dBm, which satisfy the -16dBc requirement.

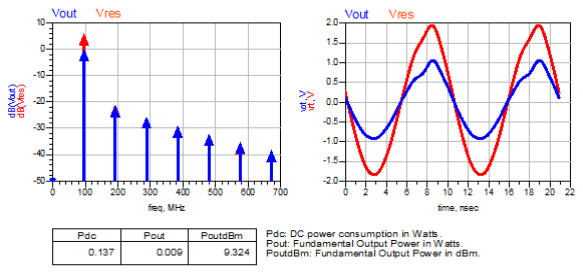
[picture p113: figure]

Figure 3.1 The simulation result by using ADS2011

### 4. PCB design

After we finish the schematic and the simulation, we design the PCB layout by

using Eagle. The PCB layout and the final circuit are shown in Figure 4.1 and Figure

4.2 respectively.

L1

' = 0.618,C2

'
= 1.6180, L3

' = 2.000,C4

'
= 1.6180

L1 = 39nH,C2 = 41pF,L3 = 127nH,C4 = 41pF, L5 = 39nH

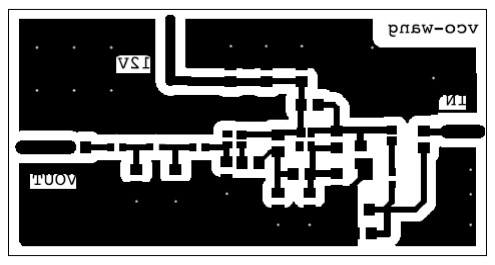
[picture p114: figure]

Figure 4.1 The layout of the circuit

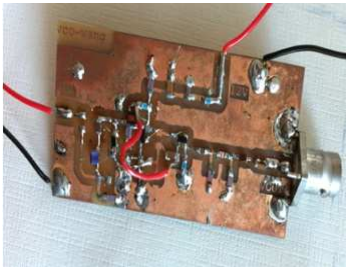
[picture p115: figure]

Figure 4.2 The final PCB board

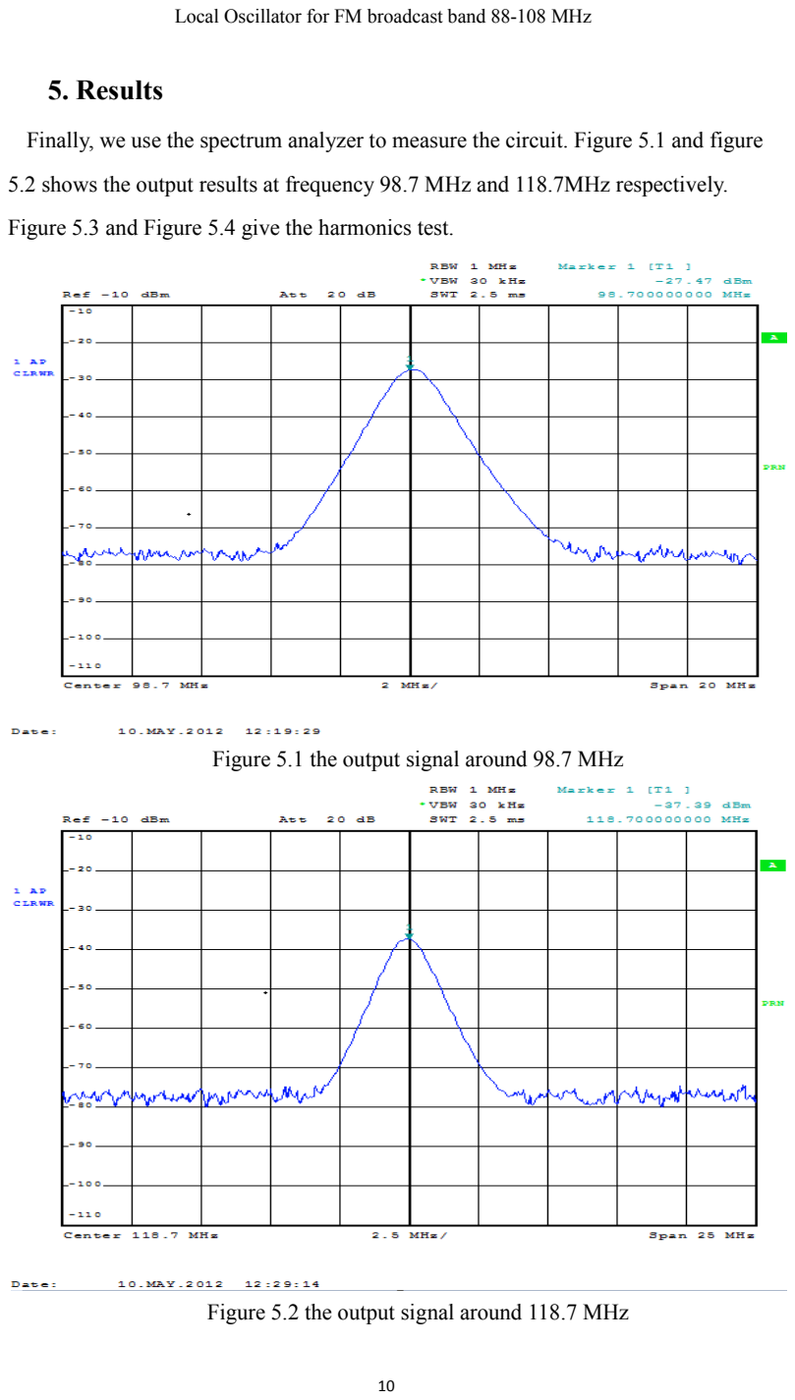
[picture p116: page 11]

### 5. Results

Finally, we use the spectrum analyzer to measure the circuit. Figure 5.1 and figure

5.2 shows the output results at frequency 98.7 MHz and 118.7MHz respectively.

Figure 5.3 and Figure 5.4 give the harmonics test.

Figure 5.1 the output signal around 98.7 MHz

Figure 5.2 the output signal around 118.7 MHz

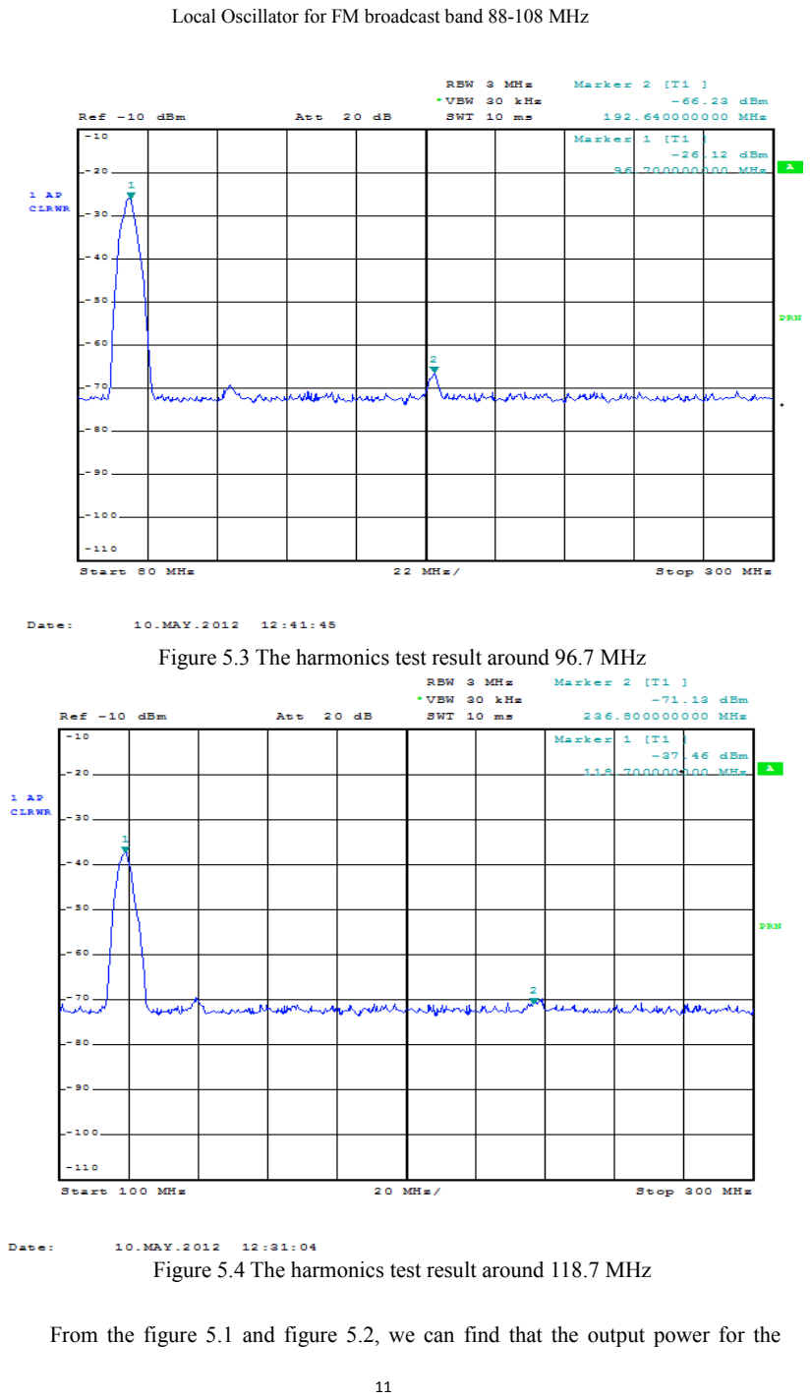
[picture p117: page 12]

Figure 5.3 The harmonics test result around 96.7 MHz

Figure 5.4 The harmonics test result around 118.7 MHz

From the figure 5.1 and figure 5.2, we can find that the output power for the fundamental frequency is too weak, just around -30dBm. And there is a significant

difference between the simulation and the measurements. This is possible because the

transmission lines were not considered in the simulation, which will also affect the

circuit. And the low pass filter causes power dissipation as well. To increase the

output power, we can change the configuration of the buffer amplifier to get the

higher output gain.

From the figure 5.3 and figure 5.4, we can find that the neighboring harmonic is

around -70dBm, which meet the requirement.

### 6. Conclusion

In this project, a local oscillator with the output tuning range from 98.7MHz to

118.7MHz is designed. We designed the schematic and the circuit was simulated by

using ADS 2011 and later a PCB layout was created using Eagle. Finally, we used the

spectrum analyzer to test the circuit. Besides the output power is too weak, the rest of

the results meet the requirement. For the further work, CE configuration amplifier

buffer can be used to increase the output power.

We obtained some experience through this project:

1. The DC operating points of the transistor should be well calculated.
2. The layout of the components should be put in the reasonable places to reduce

wiring in order to minimize the adverse effect of the transmission line.

3. When doing the layout, it is best to separate the AC part from the DC parts in

order to reduce the interaction. And in the DC part, an inductor can be added to block

the AC signal.

### 7. Acknowledgements

We would like to thank our supervisor,Göran Jönsson for his generous support

throughout the whole project. His advices were very useful in circuit and layout

design. We would also like to extend our thanks to Lars Hedenstierna, who produced

our circuit board.

### 8. Reference

[1] G.Jönsson, Department of Electroscience, Lund University, Slides from the Radio course, 2011
[2] L.Sundström, G.Jönsson, H.Börjesson, Department of Electroscience, Lund University, Radio Electronics, 2004
[3] www.nxp.com
