LieBtrau/MegawattKS_Radio_Design_101/preselector_filter/doc/Bandpass Filters_1.pdf

# LC Bandpass Filters for

# 20M, 30M, 40M

Stephen E. Sussman-Fort, Ph.D. AB2EW

stevesf@optonline.net

Bandpass Filters | October 13, 2018 | 2

Application
- In multi-station environments: special events, field day, portable operating, we need to protect receivers from excessively strong signals
- We place bandpass filters between the transceiver and the antenna
- Out of band signals greatly attenuated on receive, preventing receiver desensitization and overload
- On transmit, the filters should be transparent to the transmitter
- (No help for two stations on the same band)

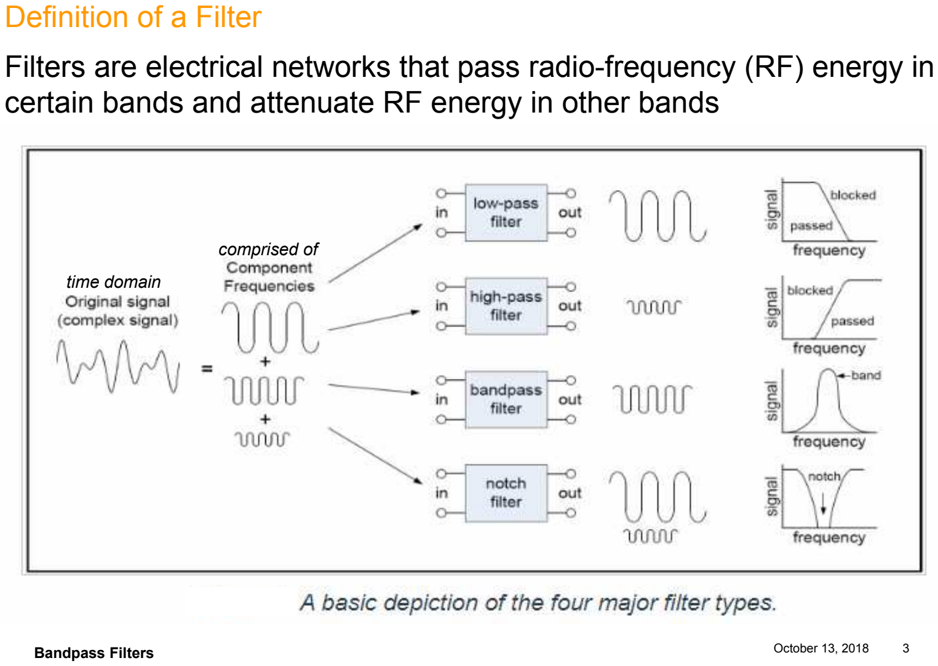
[picture p118: page 3]

Bandpass Filters | October 13, 2018 | 3

Definition of a Filter

Filters are electrical networks that pass radio-frequency (RF) energy in certain bands and attenuate RF energy in other bands

time domain

comprised of

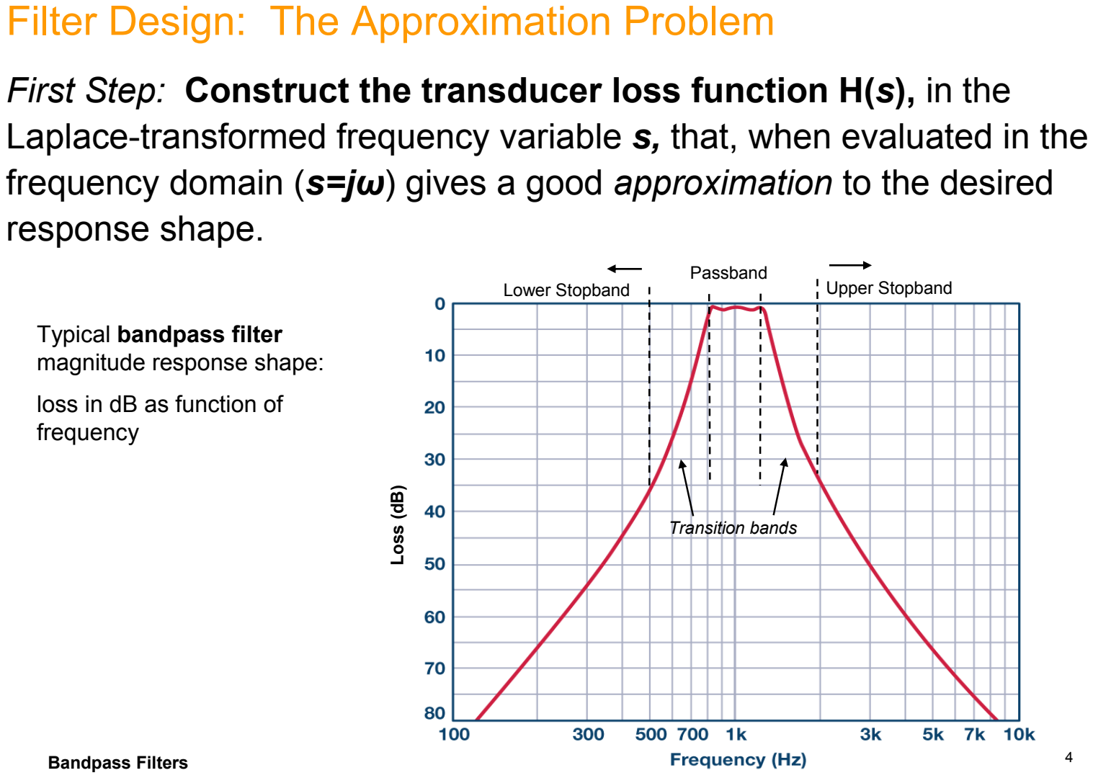
[picture p119: page 4]

Bandpass Filters | October 13, 2018 | 4

Filter Design: The Approximation Problem

First Step: Construct the transducer loss function H(s), in the Laplace-transformed frequency variable s, that, when evaluated in the frequency domain (s=jω) gives a good approximation to the desired response shape.

Typical bandpass filter
magnitude response shape:

loss in dB as function of
frequency

Loss (dB)

Passband
Lower Stopband | Upper Stopband

Transition bands

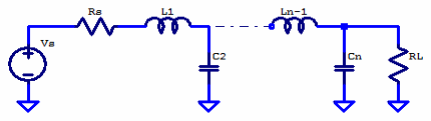
[picture p120: figure]

Bandpass Filters | October 13, 2018 | 5

Filter Design: Network Synthesis

Second Step: Perform network synthesis by expanding the function H(s) in such a was as to identify a network structure comprised of inductors and capacitors.

Examples (ladder filters):

Note: Filters are designed to transfer power between a source resistance and load resistance (e.g. transmitter output circuit and an antenna)

Singly-terminated network
(between a high impedance
source and finite load)

Bandpass Filters | October 13, 2018 | 6

Filter Design Solutions

- Filter design is a complex mathematical process
- Evolved from the first filters designed in the 1920s for the telephone network
- Many different types of both analog and digital filters used today throughout all communications circuits
- Computer programs exist for the automated design of various types of filters
- Elsie is very good for inductor-capacitor (LC) filters for ham
applications (free version: tonnesoftware.com)
- Excellent tutorial on filter design:
http://www.tonnesoftware.com/downloads/FilterTutorial.pdf

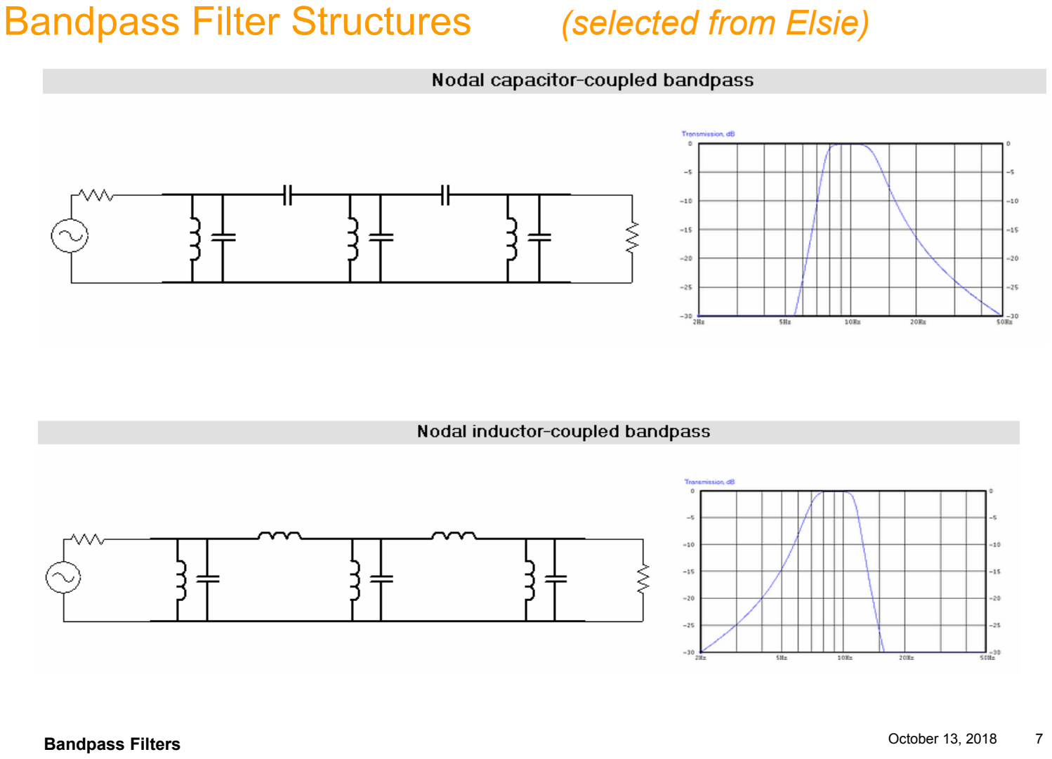
[picture p121: page 7]

Bandpass Filters | October 13, 2018 | 7
Bandpass Filter Structures | (selected from Elsie)

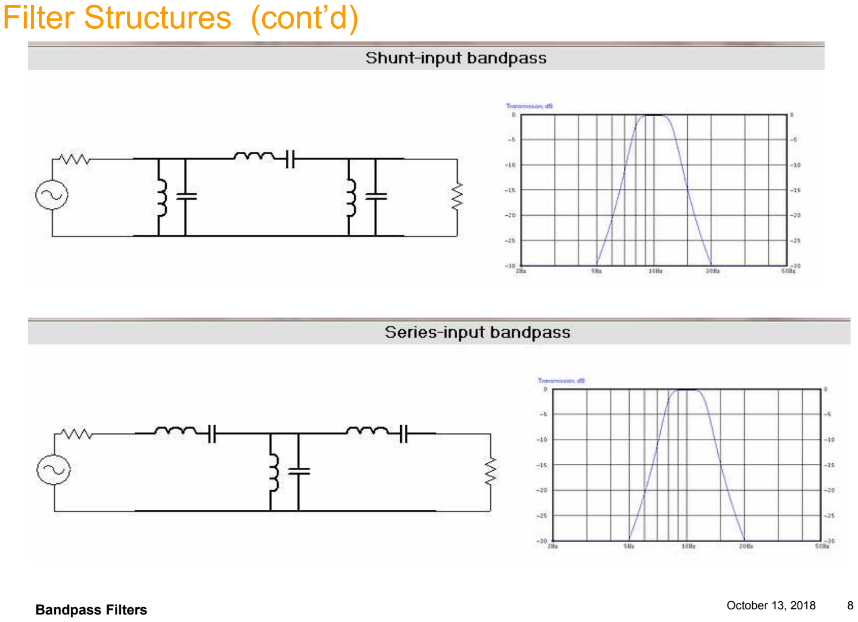
[picture p122: page 8]

Bandpass Filters | October 13, 2018 | 8

Filter Structures (cont’d)

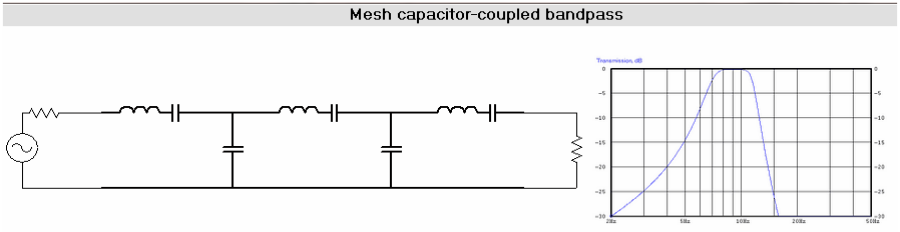
[picture p123: figure]

Bandpass Filters | October 13, 2018 | 9

Bandpass Filter Structures

Bandpass Filters | October 13, 2018 | 10

Selecting a Circuit Topology (Structure)

- We want a network that has a minimum number of inductors (which are inherently lossier than capacitors)
- We want circuit element values that are neither too large nor too small so that the components are commercially available or, for inductors, can be wound easily
- To meet the filter requirements, can experiment with circuit degree (number of inductors plus number of capacitors)
- Can try all the circuit structures
- Experienced filter designers know that narrowband bandpass filters often best realized with mesh capacitor- coupled structure (also called coupled-resonator filter)

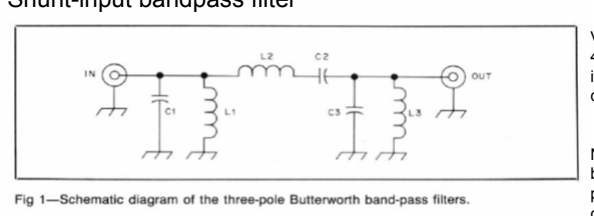
[picture p124: figure]

Bandpass Filters | October 13, 2018 | 11
A Previous Design from QST | (Lew Gordon, K4VX, Sept. 1988)

Shunt-input bandpass filter

| Values given for 160, 80, 40, 20,15,10M (toroidal inductors and silver-mica capacitors)

No designs for WARC
bands 30, 17, 12M
probably because of
contest emphasis

Results inadequate for
WARC band rejection

Results for 40M, 20M BPF
Filter | Loss (dB) in Band
| 40M 30M 20M 17M 15M
40M BPF | 0.5 15.7 32 42 47
20M BPF | 32 7.9 0.5 8.5 16

Bandpass Filters | October 13, 2018 | 12

Filter Design

- Using Elsie, design three bandpass filters: for 20, 30, & 40M
- | Sometimes we modify the design obtained by Elsie | (circuit
| optimization):

### 1. Fix certain component values and vary the others to

| get the best response

### 2. Model nonideal behavior of L’s and C’s and obtain

| new design values for best response

### 3. Combination of (1.) and (2.)

- For our filters optimization is not required to get good results
- No optimization in 40M filter; optimization used in 30M and 20M
| filters just to illustrate what can be done

Bandpass Filters | October 13, 2018 | 13

Filter Construction and Tuning

- Select and measure the inductors and capacitors at the passband frequency (e.g. via AA-170 antenna analyzer)
- Build the filters, including capacitive trimmers for adjustment of series capacitors (i.e. the resonator capacitors)
- Measure and adjust the filter for best passband response (1:1 SWR).
- Accept the resulting stopband attenuation.

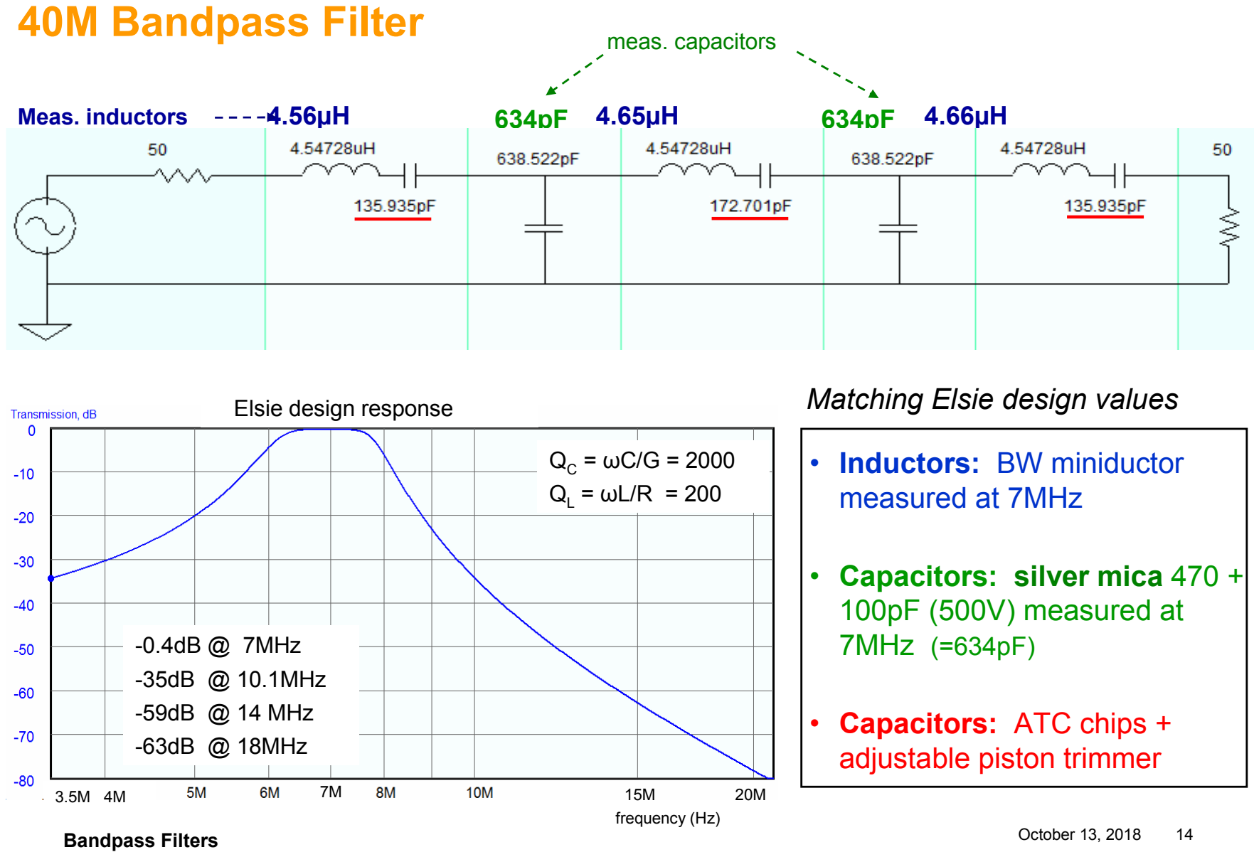
[picture p125: page 14]

Bandpass Filters | October 13, 2018 | 14
Meas. inductors | 4.56µH | 4.65µH 634pF | 634pF | 4.66µH

40M Bandpass Filter

- Inductors: BW miniductor measured at 7MHz
- Capacitors: silver mica 470 + 100pF (500V) measured at
7MHz (=634pF)
- Capacitors: ATC chips +
adjustable piston trimmer

-0.4dB @ 7MHz
-35dB @ 10.1MHz
-59dB @ 14 MHz
-63dB @ 18MHz

QC = ωC/G = 2000
QL = ωL/R = 200

meas. capacitors

Matching Elsie design values

frequency (Hz)

15M | 20M

Elsie design response

3.5M 4M | 7M

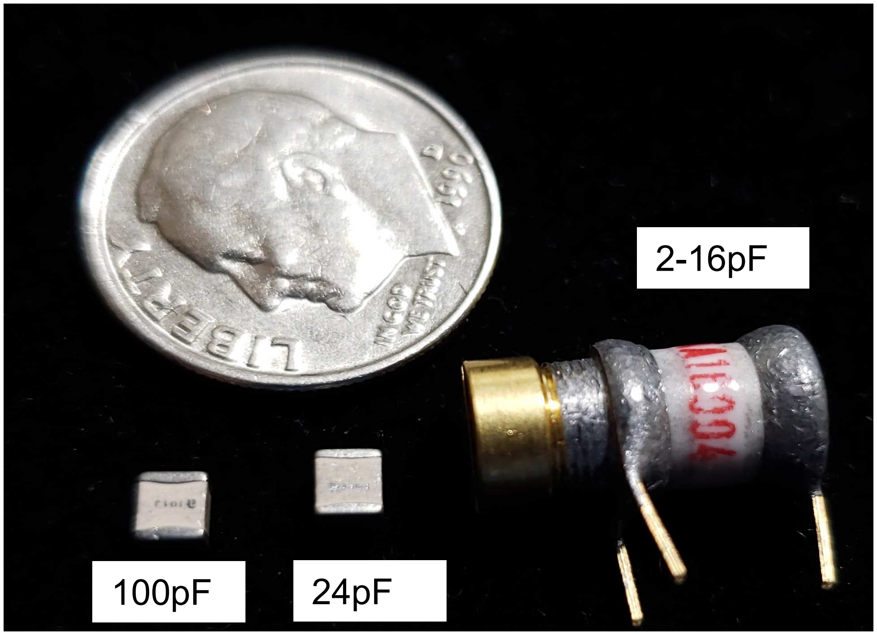
[picture p126: figure]

Bandpass Filters | October 13, 2018 | 15

40M Bandpass Filter – match Elsie design values

For 135pF capacitors value use:

100 + 24 + (2-16) trimmer

= tunable (126 – 140)pF

For 172pF capacitor value use:

100 + 24 + 39 + (2-16) trimmer = tunable (165 – 179)pF

Chip capacitors true to their stated values up to microwave frequencies 500V rating; can handle 100W (2A into 50Ω)

Filter tuning: Adjust 3 trimmers for 1:1 SWR at 7.025MHZ

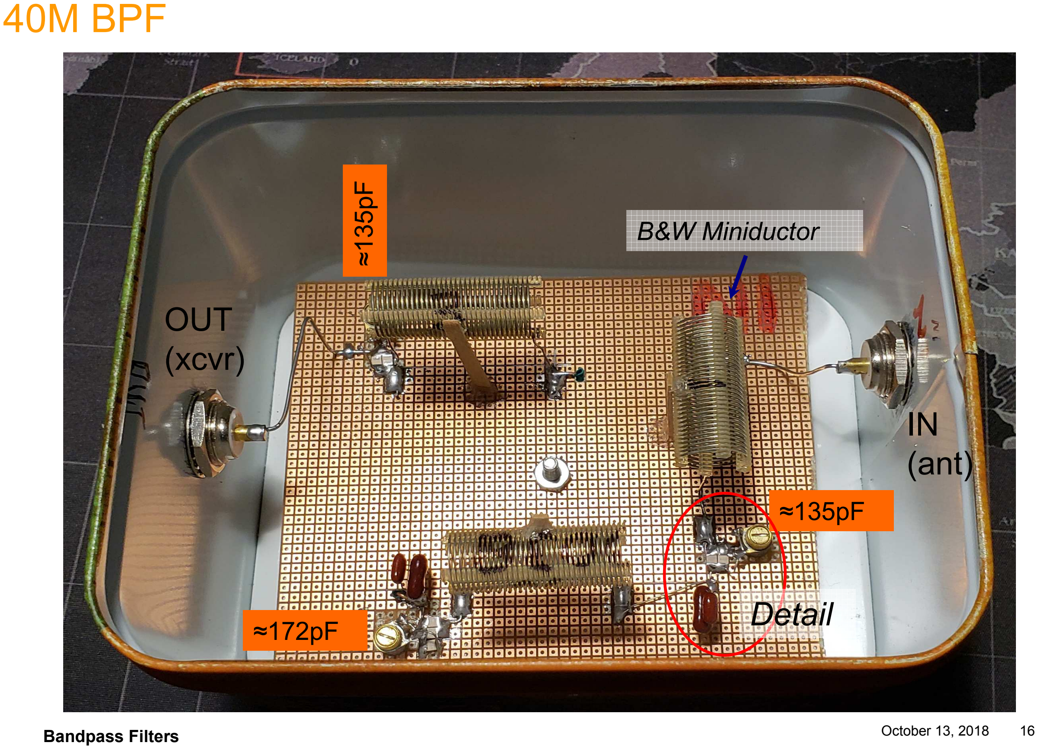
[picture p127: page 16]

Bandpass Filters | October 13, 2018 | 16

40M BPF

≈135pF

≈135pF

≈172pF

IN
(ant)

OUT
(xcvr)

Detail

B&W Miniductor

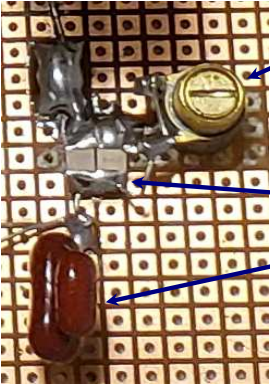
[picture p128: figure]

Bandpass Filters | October 13, 2018 | 17

Detail

470pF + 100pF

100 + 24 + (2-16) trimmer

chip capacitors

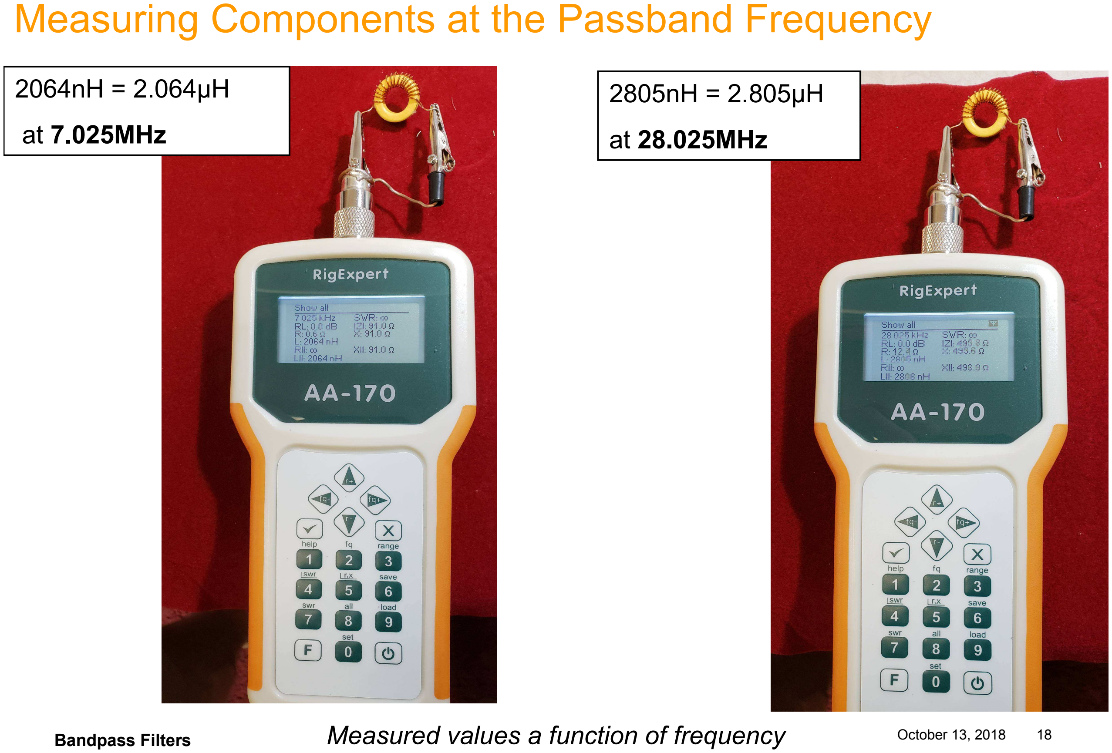
[picture p129: page 18]

Bandpass Filters | October 13, 2018 | 18

Measuring Components at the Passband Frequency

2064nH = 2.064µH

at 7.025MHz

2805nH = 2.805µH

at 28.025MHz

Measured values a function of frequency

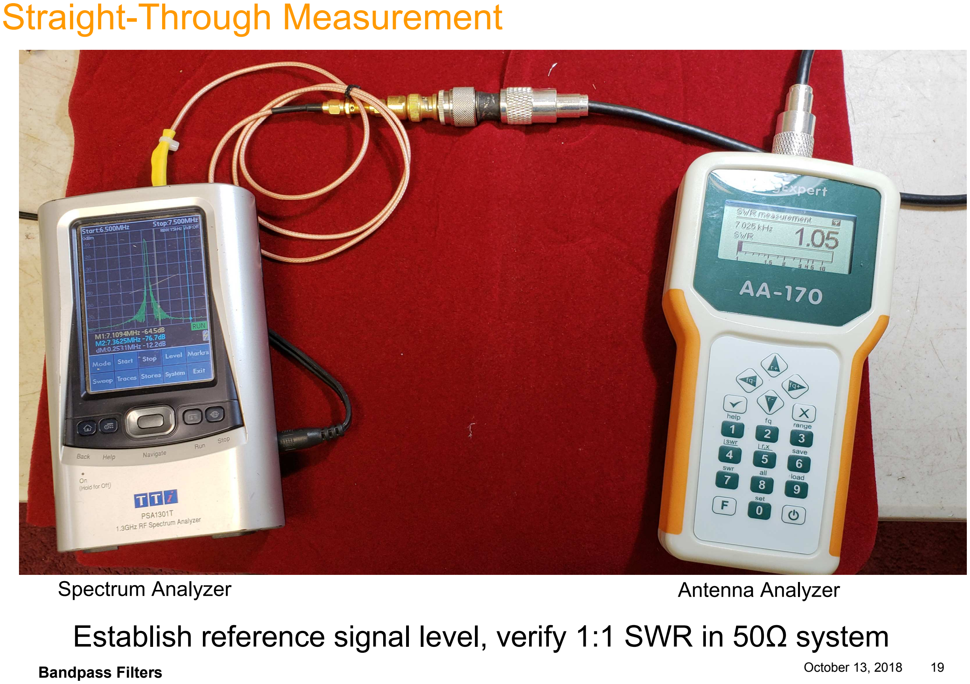
[picture p130: page 19]

Bandpass Filters | October 13, 2018 | 19

Straight-Through Measurement

Establish reference signal level, verify 1:1 SWR in 50Ω system

Spectrum Analyzer | Antenna Analyzer

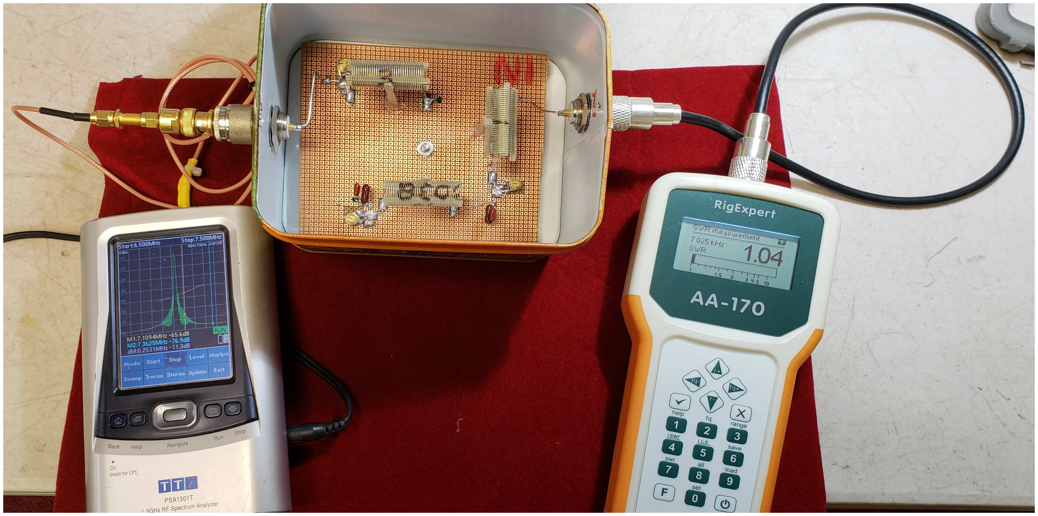
[picture p131: figure]

Bandpass Filters | October 13, 2018 | 20

Tuning Setup and Transmission Measurement

Adjust trimmer capacitors for minimum SWR at 7.025 MHz (was quite good to begin with)

Measure transmission at 20, 30, 40M

Bandpass Filters | October 13, 2018 | 21

Measured Results, 40M BPF

Filter | Loss (dB) in Band
| 80M 40M 30M 20M 17M
40M BPF | 32.1 0.5 28.4 46.8 54.0

Measurement Frequencies
80M: 3.5 MHz
40M: 7.025 MHz
30M: 10.1 MHz
20M: 14.0 MHz
17M: 18.068 MHz
Elsie Design: | 0.4 | 35 | 59 | 63
- Not quite as much out-of-band rejection as Elsie design; still quite adequate
- Errors due to: non-exact values, high-frequency coupling between the air-wound inductors, frequency dependence of silver-mica capacitor

*

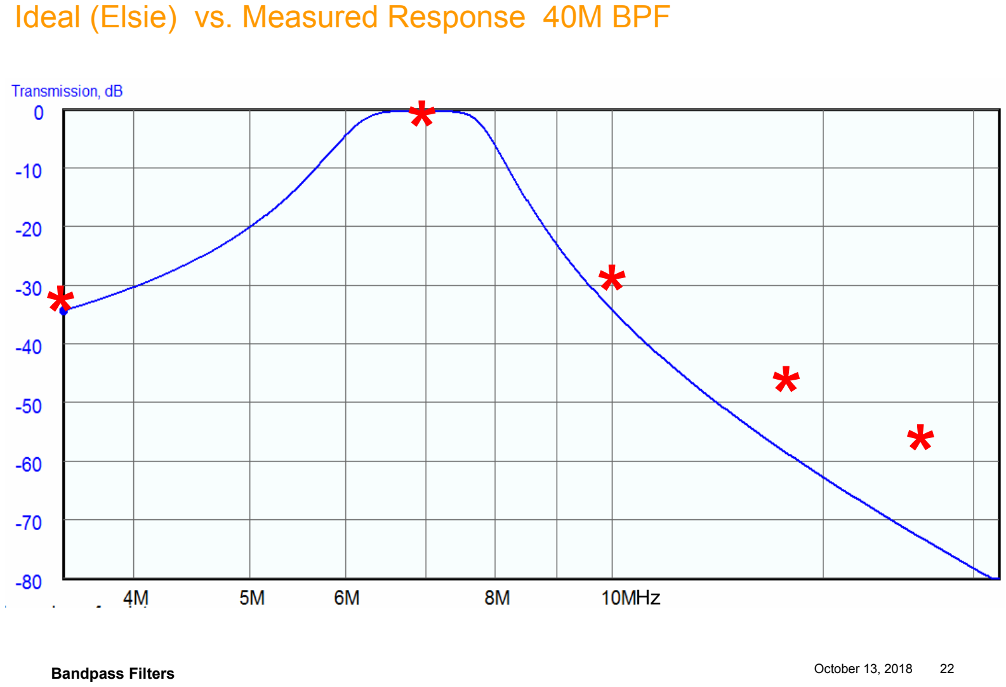
[picture p132: page 22]

Bandpass Filters | October 13, 2018 | 22

Ideal (Elsie) vs. Measured Response 40M BPF

*

*
*
*

Hz

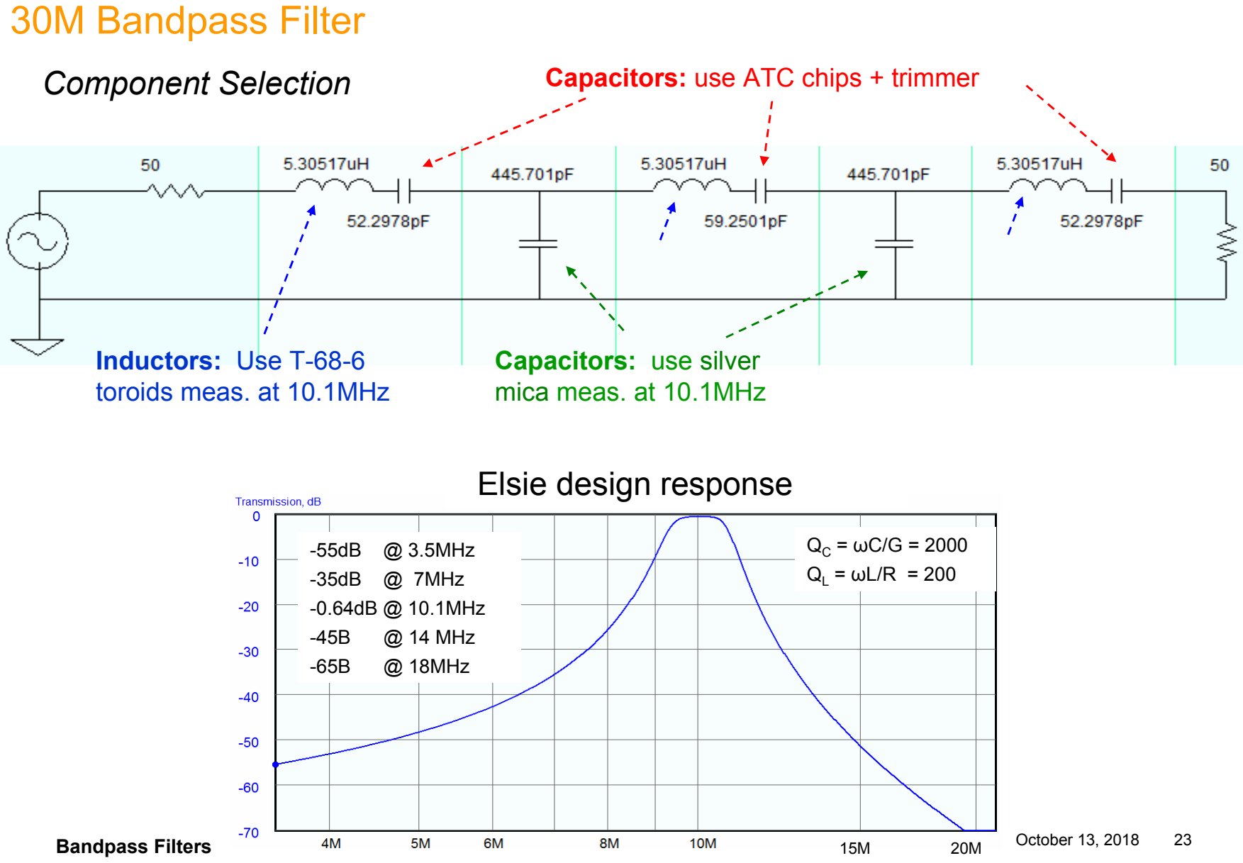
[picture p133: page 23]

Bandpass Filters | October 13, 2018 | 23

30M Bandpass Filter

-55dB @ 3.5MHz
-35dB @ 7MHz
-0.64dB @ 10.1MHz
-45B | @ 14 MHz
-65B | @ 18MHz
15M | 20M

QC = ωC/G = 2000
QL = ωL/R = 200

Elsie design response

Capacitors: use ATC chips + trimmer

Inductors: Use T-68-6
toroids meas. at 10.1MHz

Capacitors: use silver
mica meas. at 10.1MHz

Component Selection

Bandpass Filters | October 13, 2018 | 24

Capacitor Selection

Silver Mica 390pF capacitor (+/- 5%. 500V)

Freq. (MHz) | Measured Capacitance (pF)

1 404

3.5 404

7 453

10.1 453

14 589

18.1 875

21 1520

### 25 self-resonance

| (becomes inductive past 25 MHz)

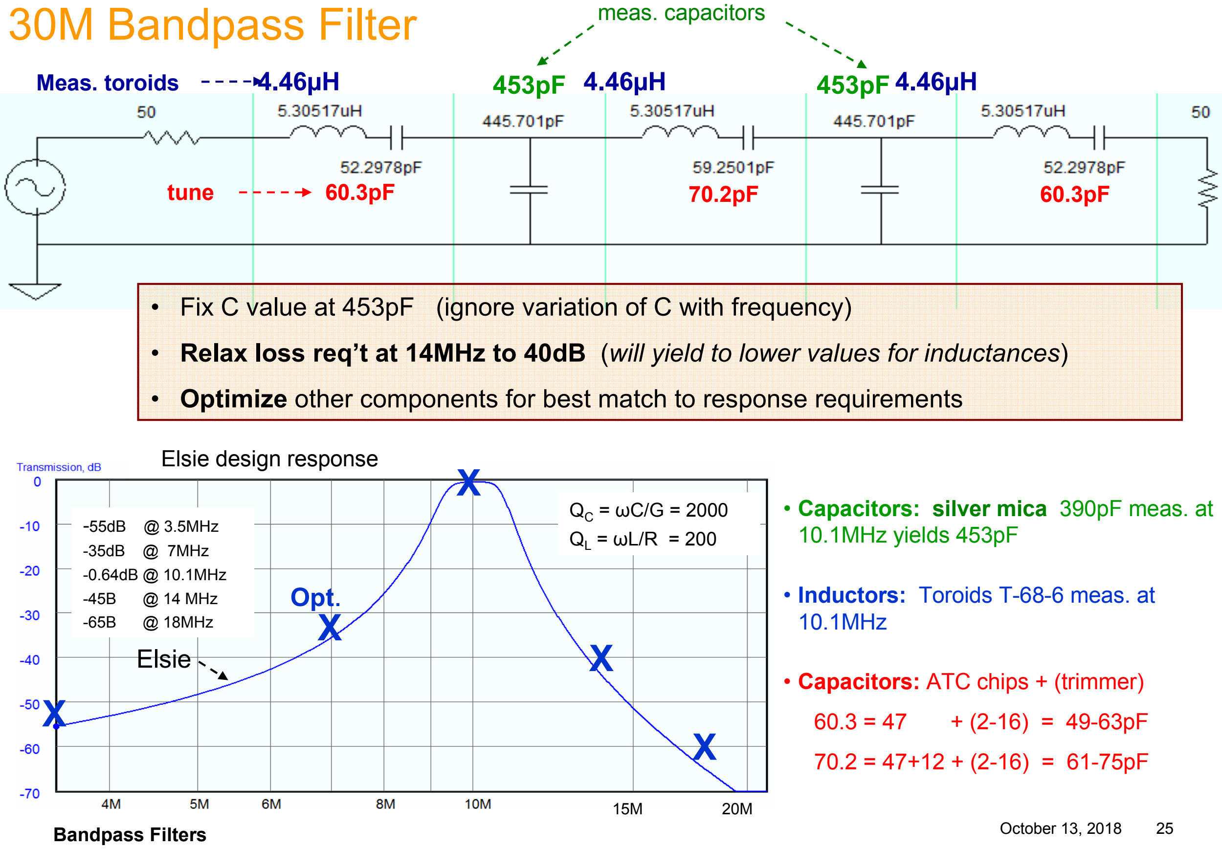
[picture p134: page 25]

Bandpass Filters | October 13, 2018 | 25

30M Bandpass Filter -55dB @ 3.5MHz

-35dB @ 7MHz
-0.64dB @ 10.1MHz
-45B | @ 14 MHz
-65B | @ 18MHz
15M | 20M

QC = ωC/G = 2000
QL = ωL/R = 200

Elsie design response

- Capacitors: silver mica 390pF meas. at 10.1MHz yields 453pF
- Inductors: Toroids T-68-6 meas. at 10.1MHz
- Capacitors: ATC chips + (trimmer)

60.3 = 47 + (2-16) = 49-63pF

70.2 = 47+12 + (2-16) = 61-75pF

- Fix C value at 453pF (ignore variation of C with frequency)
- Relax loss req’t at 14MHz to 40dB (will yield to lower values for inductances)
- Optimize other components for best match to response requirements
Meas. toroids | 4.46µH | 4.46µH | 4.46µH
| | meas. capacitors
453pF | 453pF
tune | 60.3pF | 70.2pF | 60.3pF

X

X

X

X

X

Elsie

Opt.

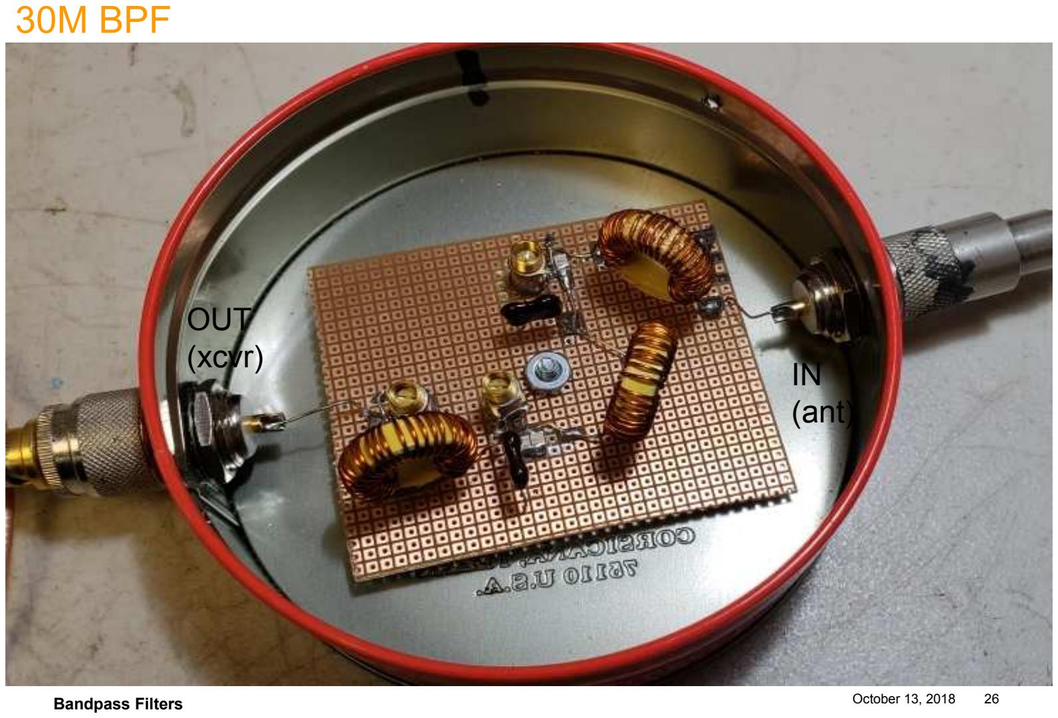
[picture p135: page 26]

Bandpass Filters | October 13, 2018 | 26

30M BPF

IN
(ant)

OUT
(xcvr)

Bandpass Filters | October 13, 2018 | 27

Measured Results, 30M BPF

Filter | Loss (dB) in Band
| 80M 40M 30M 20M 17M
30M BPF | 49.0 30.6 0.4 34.2 55.4
Elsie Design | 55 | 35 | 0.6 | 45 | 65
Optimized | 52 | 33 | 0.6 | 40 | 61

note

*

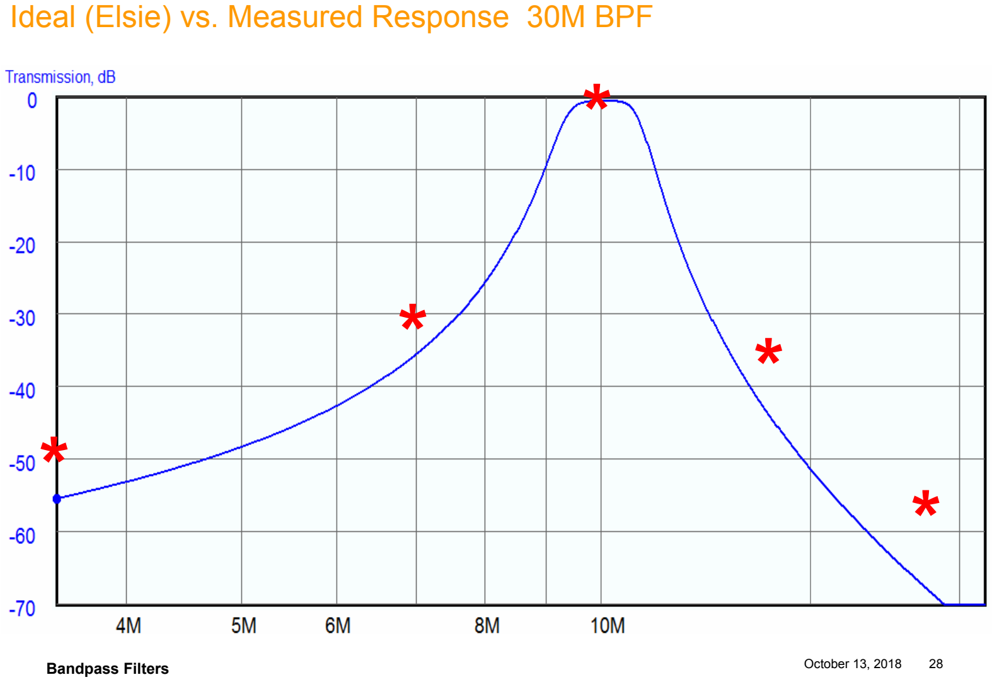
[picture p136: page 28]

Bandpass Filters | October 13, 2018 | 28

Ideal (Elsie) vs. Measured Response 30M BPF

*

*
*

*

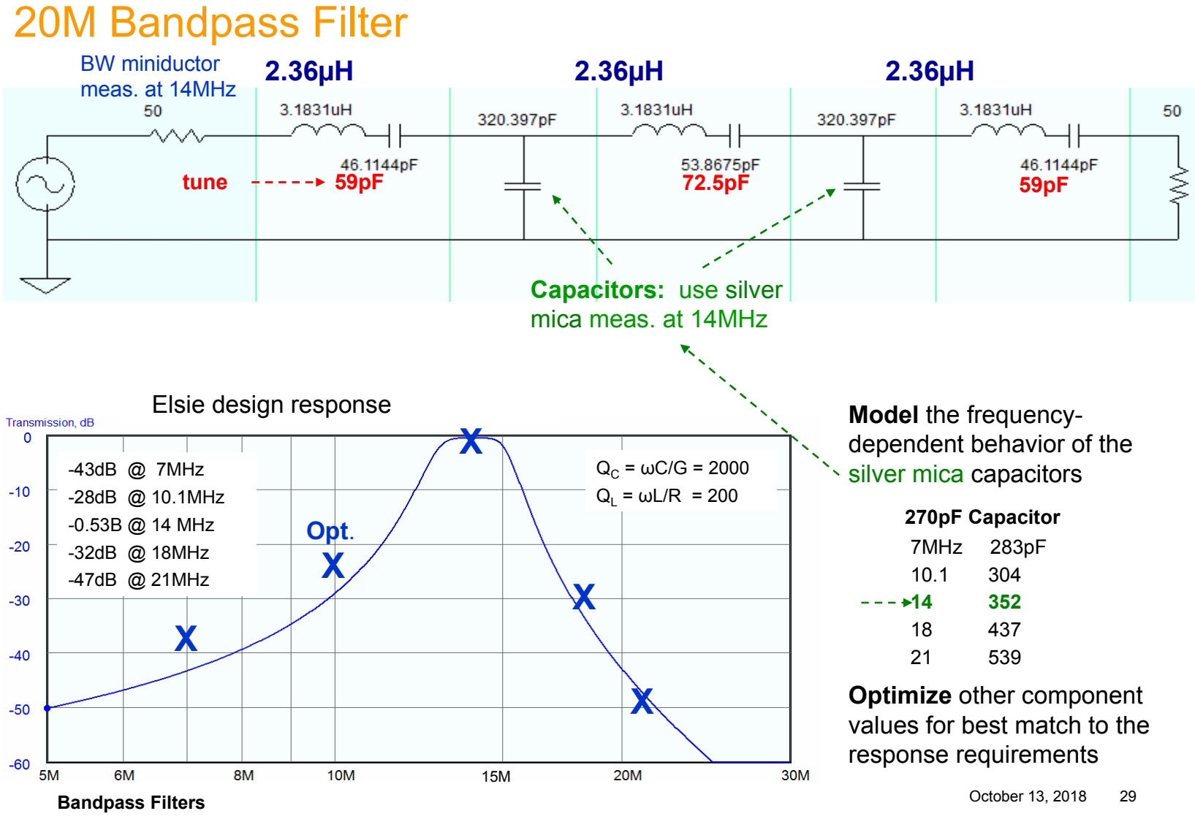
[picture p137: page 29]

Bandpass Filters | October 13, 2018 | 29

20M Bandpass Filter

-43dB @ 7MHz
-28dB @ 10.1MHz
-0.53B @ 14 MHz
-32dB @ 18MHz
-47dB @ 21MHz

QC = ωC/G = 2000
QL = ωL/R = 200

Elsie design response

15M

BW miniductor
meas. at 14MHz

Capacitors: use silver
mica meas. at 14MHz

Model the frequency-dependent behavior of the
silver mica capacitors

Optimize other component
values for best match to the response requirements

270pF Capacitor
7MHz 283pF
10.1 304
14 352
18 437
21 539
2.36µH | 2.36µH | 2.36µH
tune | 59pF | 72.5pF | 59pF

X

X

X
X

X

Opt.

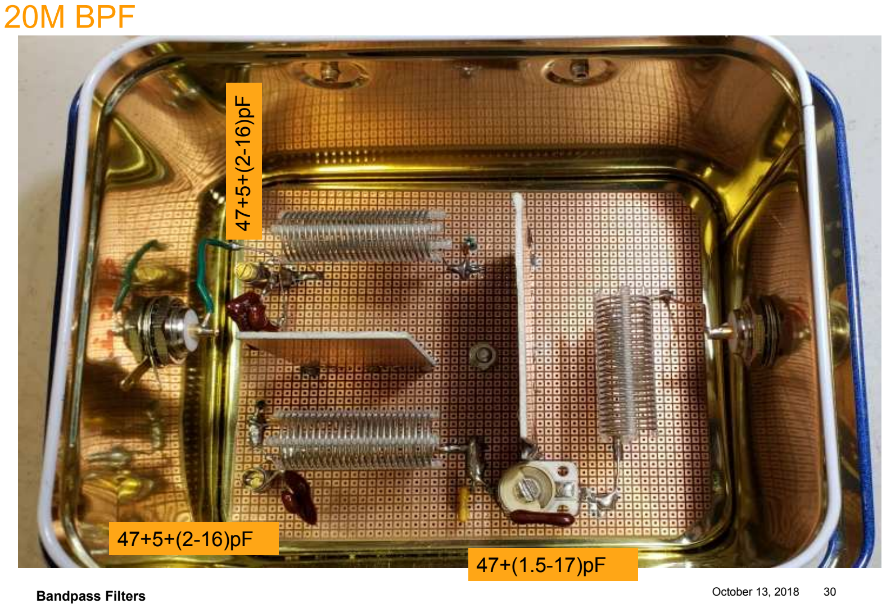
[picture p138: page 30]

Bandpass Filters | October 13, 2018 | 30

20M BPF

47+5+(2-16)pF

47+5+(2-16)pF
47+(1.5-17)pF

Bandpass Filters | October 13, 2018 | 31

Measured Results, 20M BPF

Filter | Loss (dB) in Band
| 40M 30M 20M 17M 15M
20M BPF | 36 23 0.4 19 33
Elsie Design | 43 | 28 | 0.5 | 32 | 47
Optimized | 37 | 24 | 0.5 | 30 | 49
- Not as much out-of-band rejection as Elsie or optimized design
- Errors due to: high-frequency coupling between the air-wound inductors (shielding probably inadequate)

*

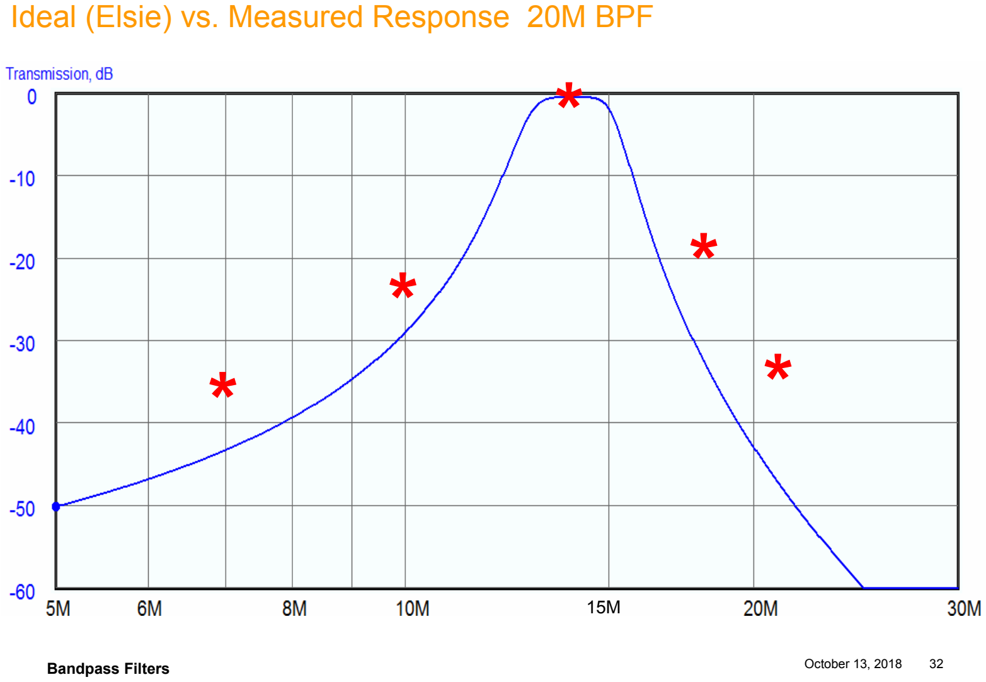
[picture p139: page 32]

Bandpass Filters | October 13, 2018 | 32

Ideal (Elsie) vs. Measured Response 20M BPF

*

*

*
*

15M

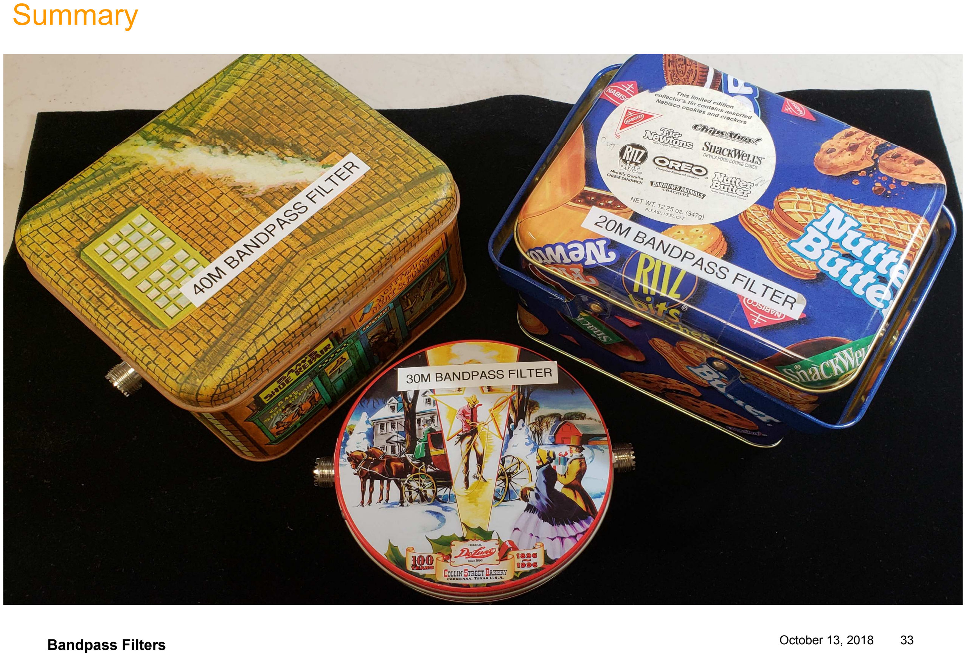
[picture p140: page 33]

Bandpass Filters | October 13, 2018 | 33

Summary

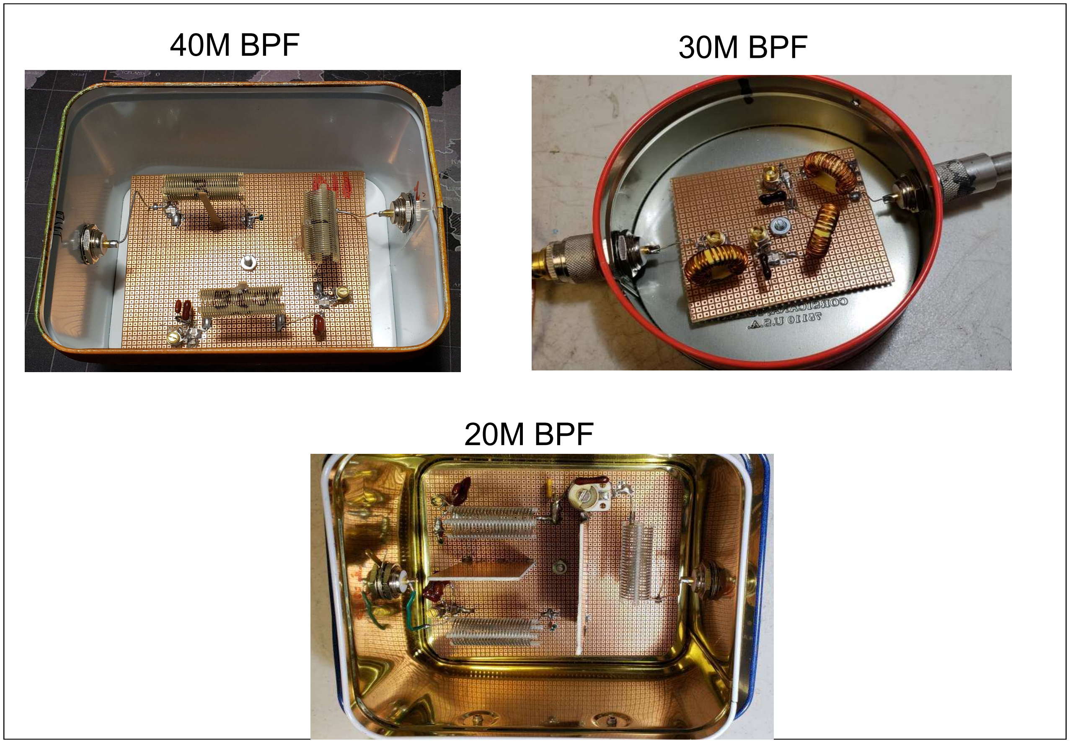
[picture p141: page 34]

Bandpass Filters | October 13, 2018 | 34
40M BPF | 30M BPF

20M BPF

*

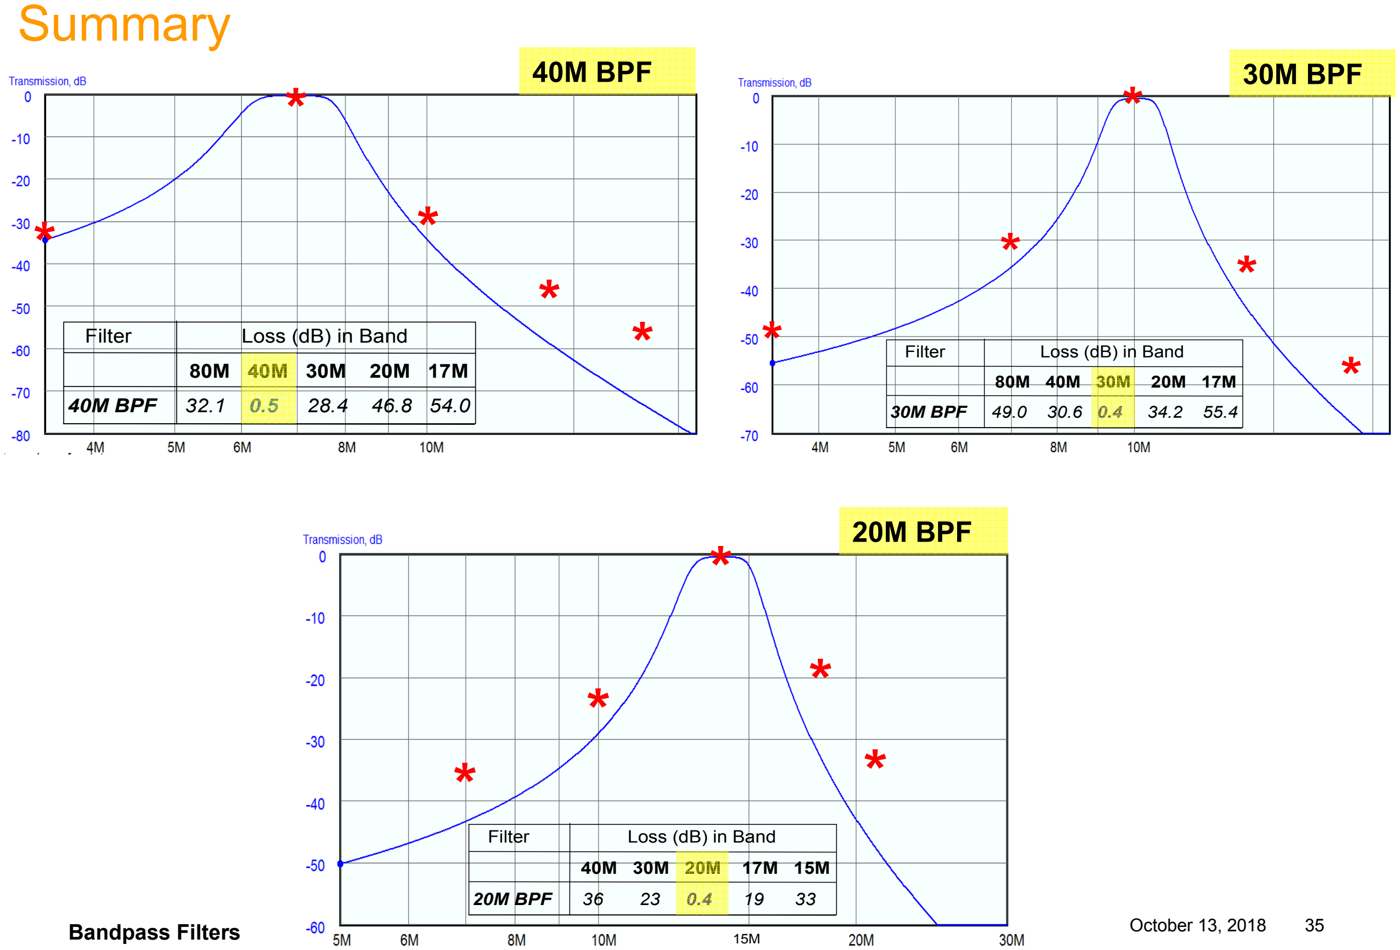
[picture p142: page 35]

Bandpass Filters | October 13, 2018 | 35

Summary

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
40M BPF | 30M BPF

20M BPF

Filter | Loss (dB) in Band
| 80M 40M 30M 20M 17M
40M BPF | 32.1 0.5 28.4 46.8 54.0
Filter | Loss (dB) in Band
| 80M 40M 30M 20M 17M
30M BPF | 49.0 30.6 0.4 34.2 55.4
Filter | Loss (dB) in Band
| 40M 30M 20M 17M 15M
20M BPF | 36 23 0.4 19 33

Bandpass Filters | October 13, 2018 | 36

Conclusions
- Elsie program can design bandpass filters for transceivers
- Optimization of the design is possible but not necessary
- Have choice of air-core or toroidal inductors; leaded or chip capacitors
- Must be aware of component value variation with frequency
- Match component values as closely as possible; allow tuning of series capacitances by using trimmers; we avoid inductance adjustment
- Design approach here is to get best passband result and accept stopband attenuation
- If more stopband attenuation is required, can design a more complex filter
- Filters like these are also commercially available
