LieBtrau/MegawattKS_Radio_Design_101/doc/8506025.pdf

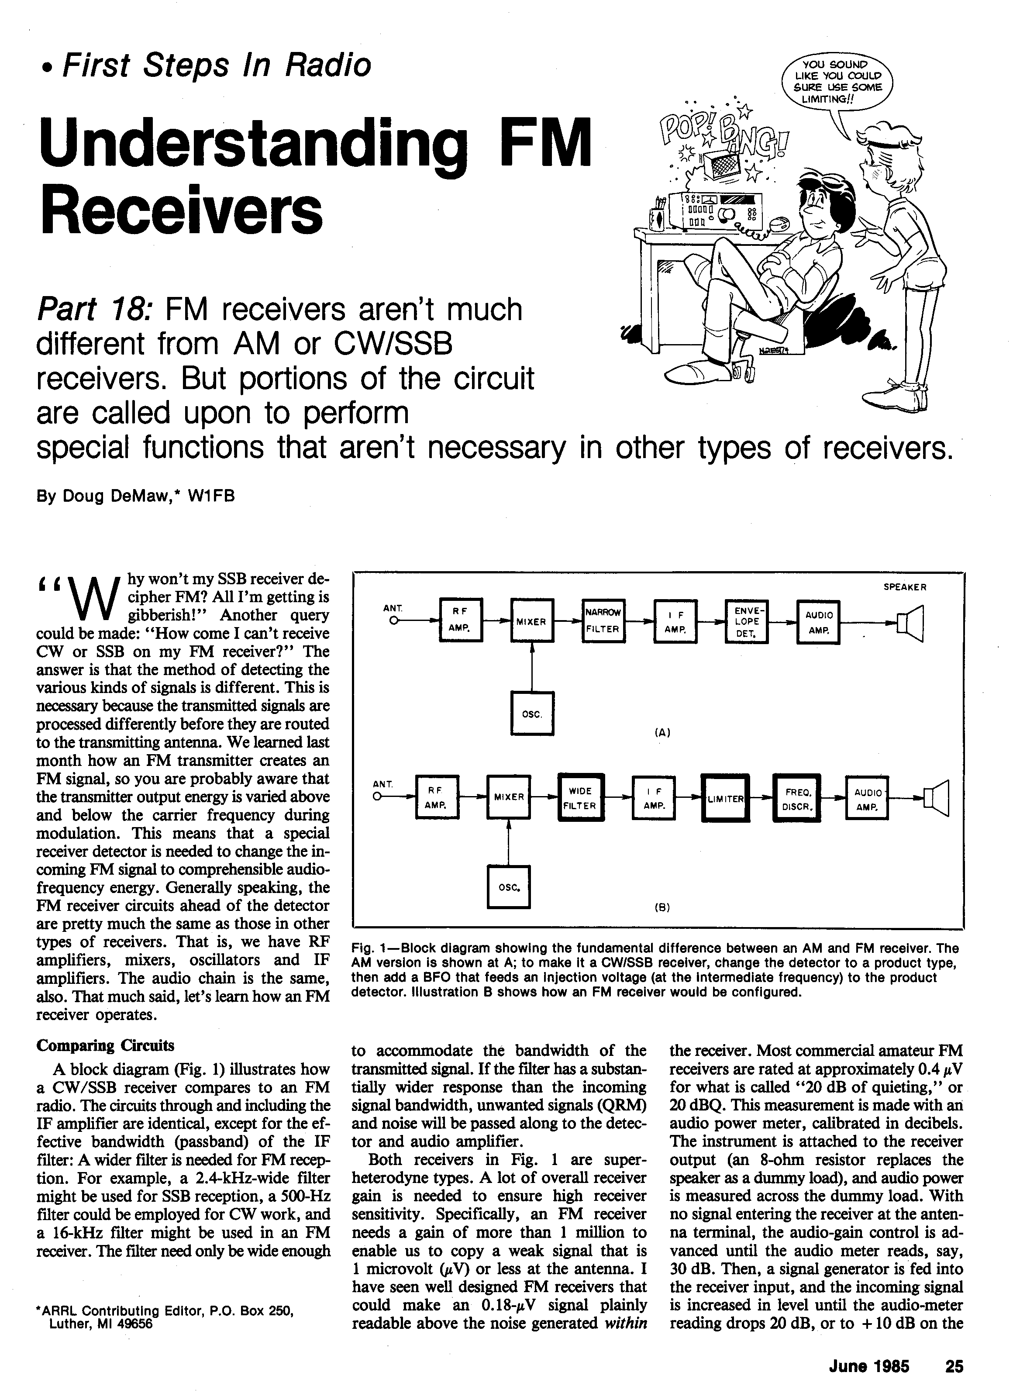
[picture p146: page 1]
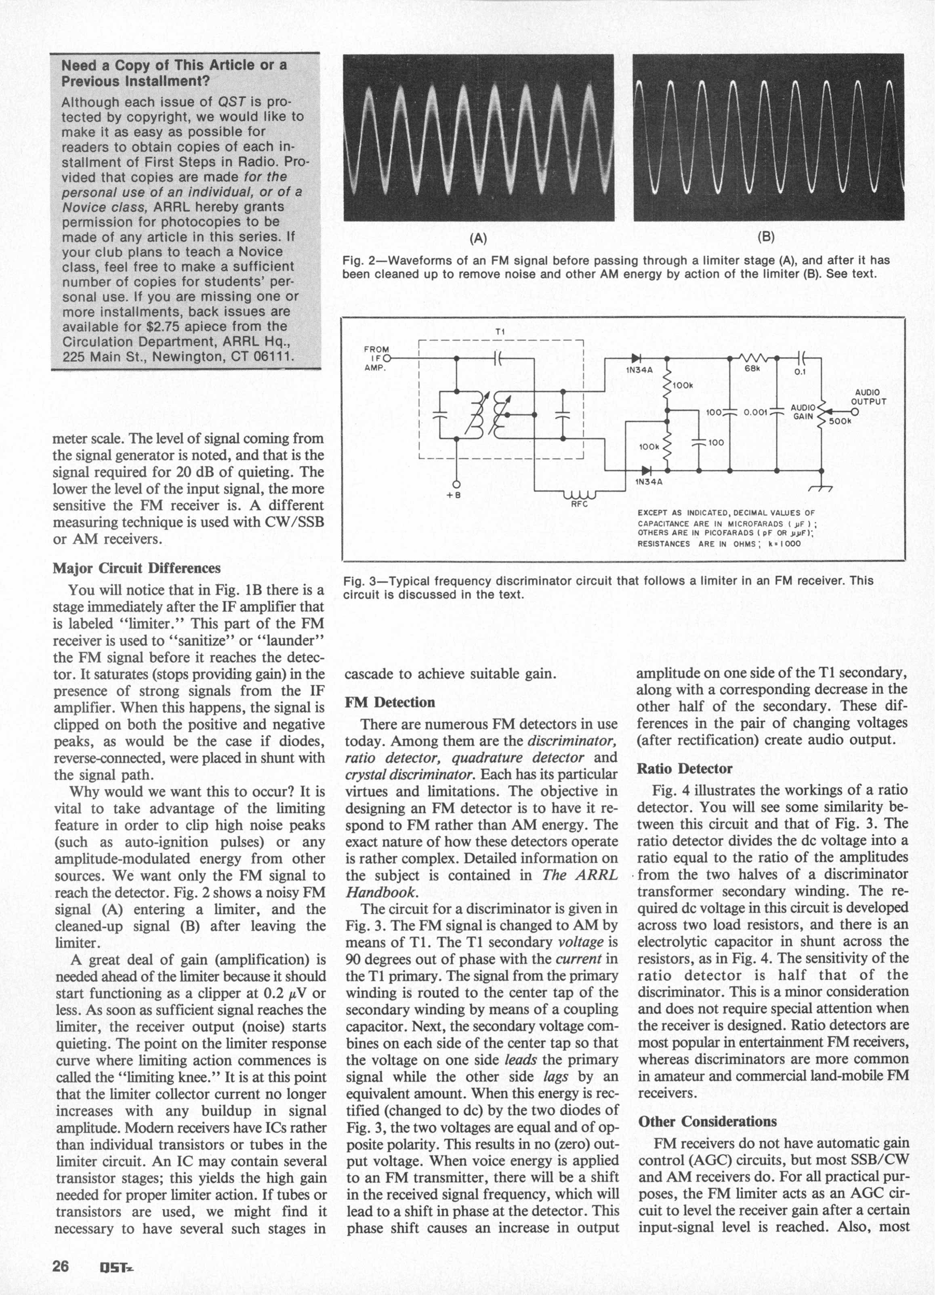
[picture p147: page 2]
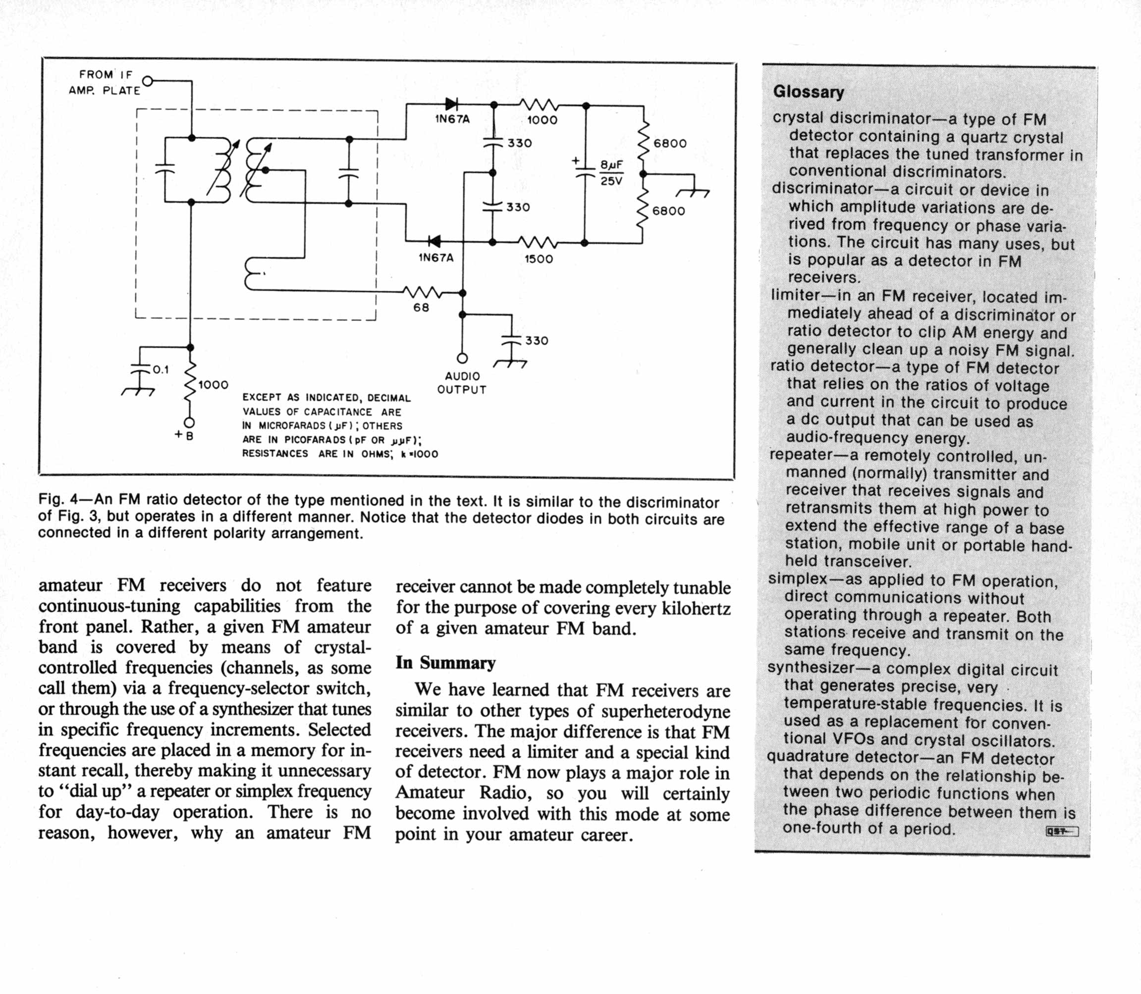
[picture p148: page 3]
