LieBtrau/MegawattKS_Radio_Design_101/audio_amplifier/doc/ITT_Pony13.pdf

# Radiomuseum.org: ITT Schaub-Lorenz Pony 13

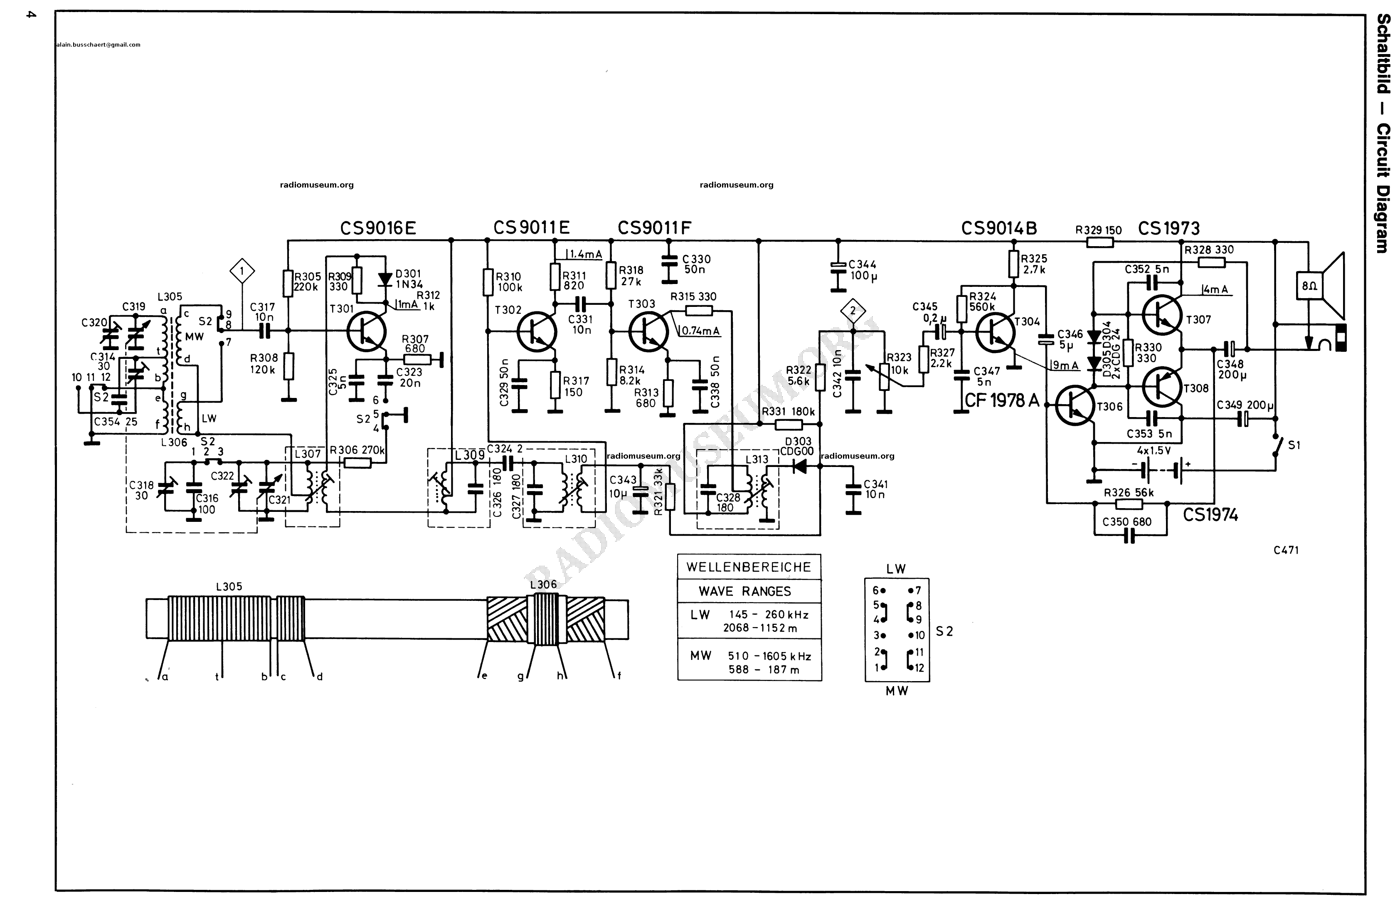
[picture p149: page 1]

www.radiomuseum.org; upload by Thomas Günzel; download by Alain Alain Busschaert Mon May 16 09:19:06 CEST 2016 [3368 x 2174, 61kb]
