LieBtrau/MegawattKS_Radio_Design_101/doc/vintage_radio/Grundig Concert Boy 1100.pdf

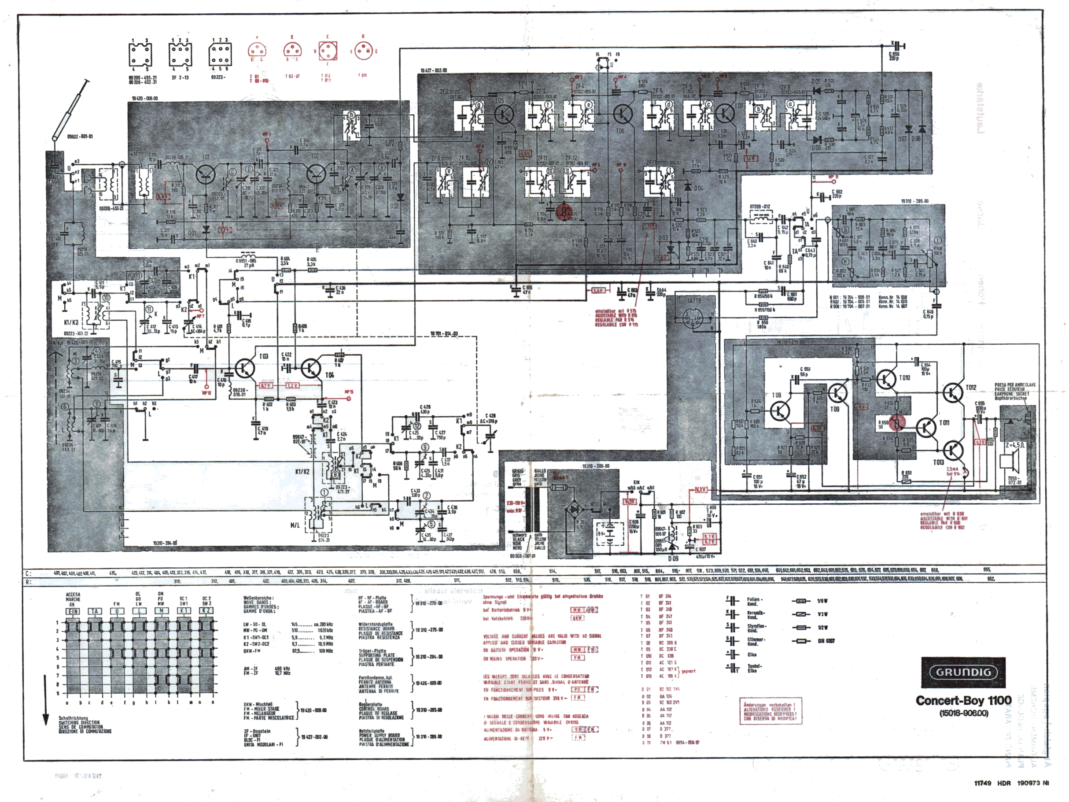
[picture p150: page 1]
