LieBtrau/MegawattKS_Radio_Design_101/LO/JFET_Clapp/doc/De Beste Oscillator.pdf

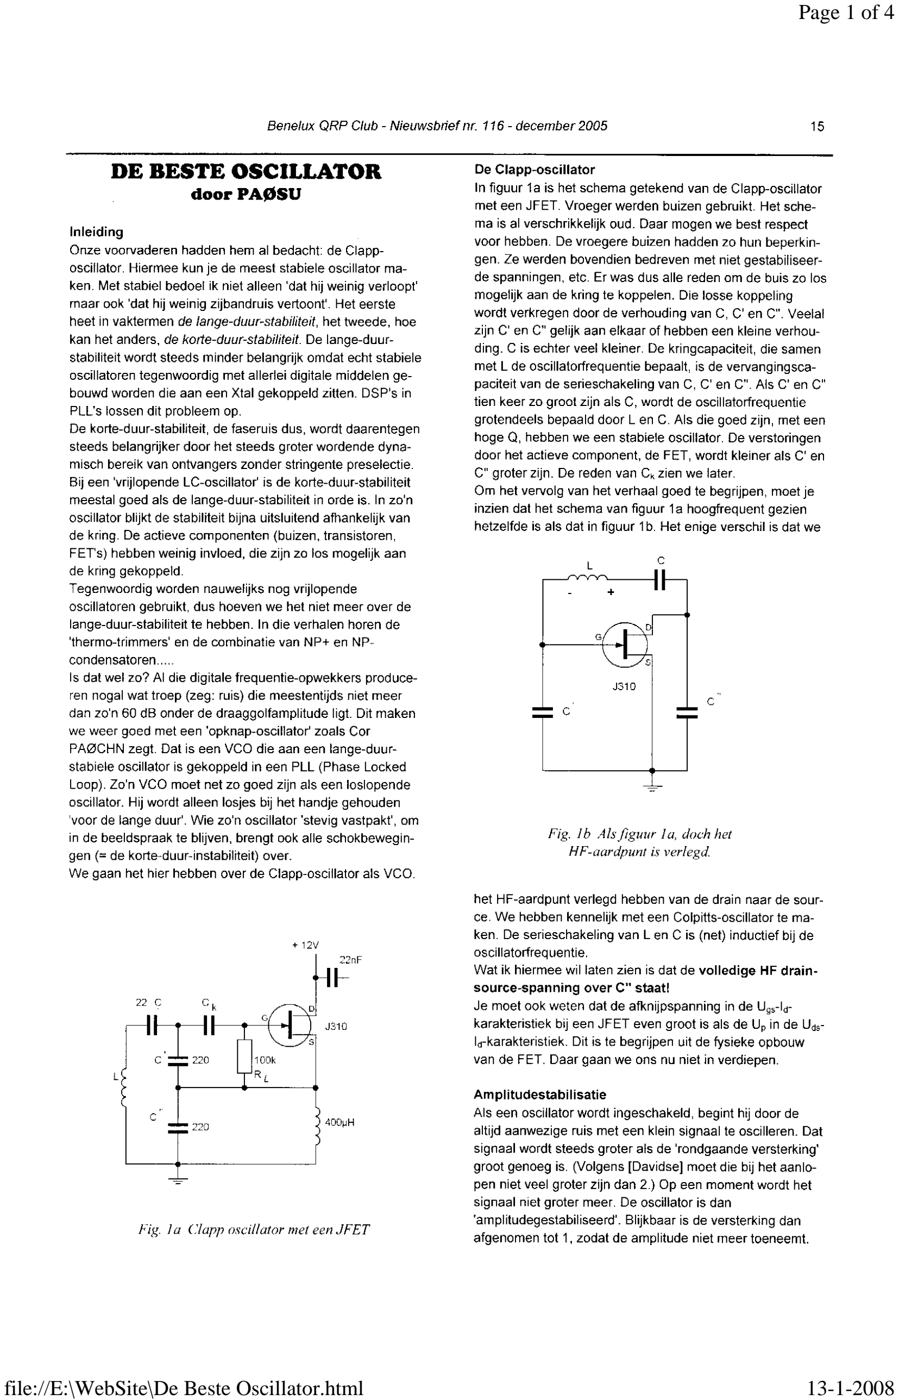
[picture p151: page 1]

file://E:\WebSite\De Beste Oscillator.html | 13-1-2008
