LieBtrau/MegawattKS_Radio_Design_101/doc/vintage_radio/Alain/4 Band Radio Recorder TC414/d_loewe_tc414_s1_titl.pdf

# radiomuseum.org: 4 Band Radio Recorder TC414 Art.-Nr. 58200

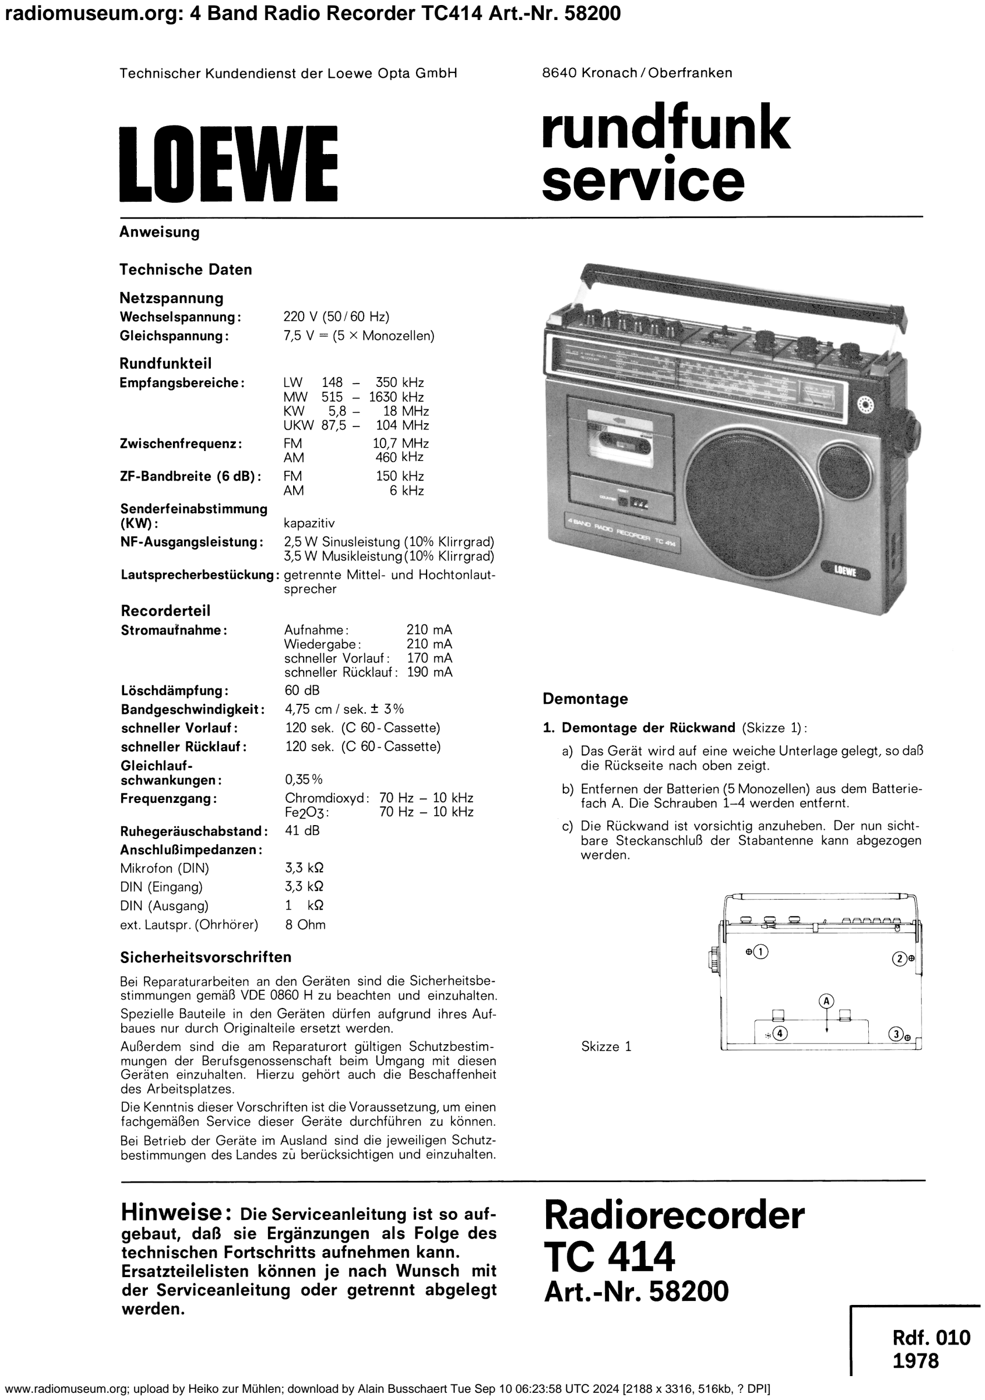
[picture p152: page 1]

www.radiomuseum.org; upload by Heiko zur Mühlen; download by Alain Busschaert Tue Sep 10 06:23:58 UTC 2024 [2188 x 3316, 516kb, ? DPI]
