LieBtrau/MegawattKS_Radio_Design_101/doc/vintage_radio/Alain/4 Band Radio Recorder TC414/d_loewe_tc414_s2_demont.pdf

# radiomuseum.org: 4 Band Radio Recorder TC414 Art.-Nr. 58200

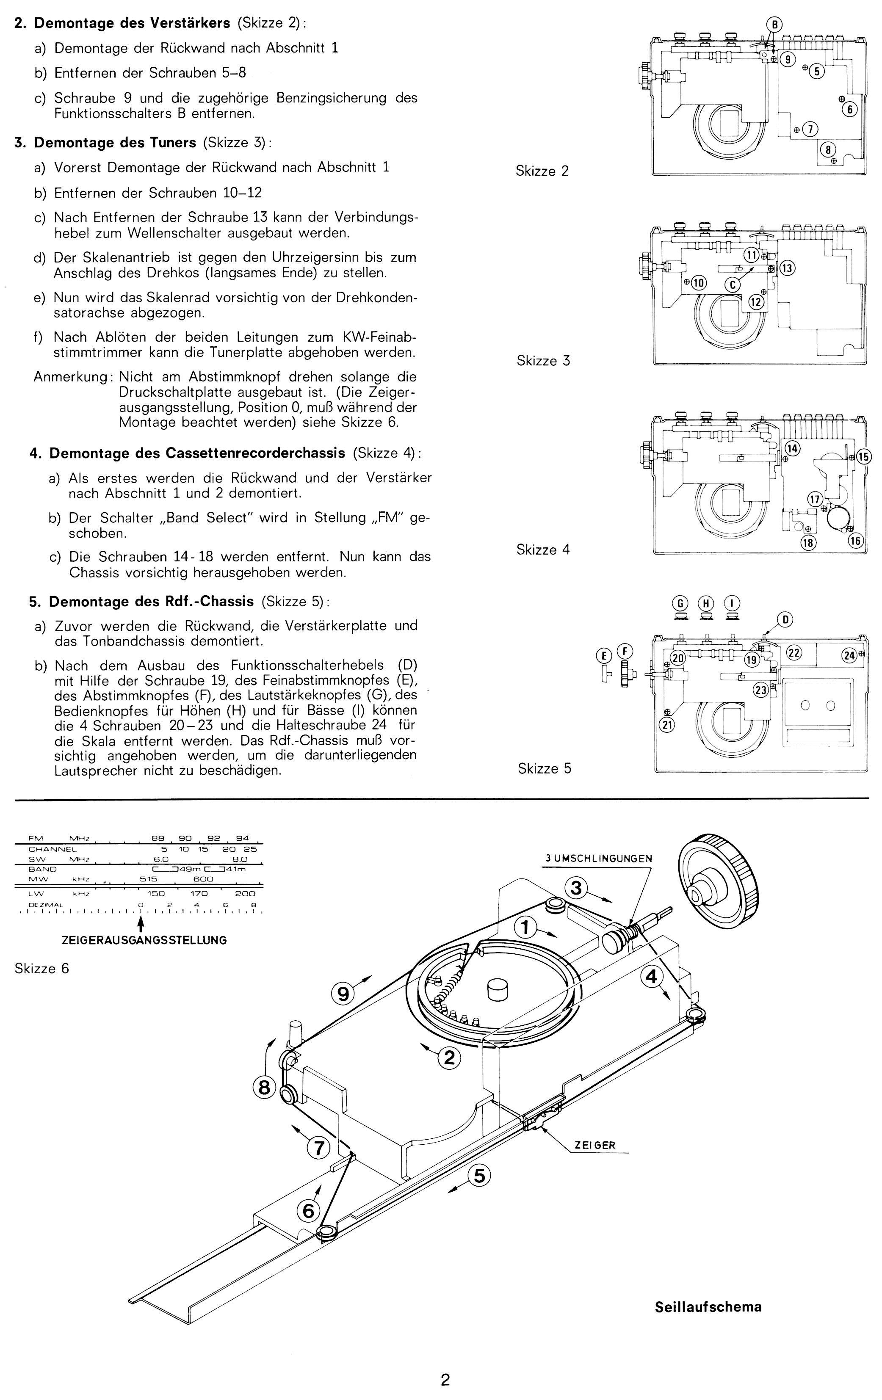
[picture p153: page 1]

www.radiomuseum.org; upload by Heiko zur Mühlen; download by Alain Busschaert Tue Sep 10 06:24:33 UTC 2024 [2083 x 3307, 266kb, ? DPI]
