LieBtrau/MegawattKS_Radio_Design_101/audio_amplifier/doc/simple_final_amplifier.png

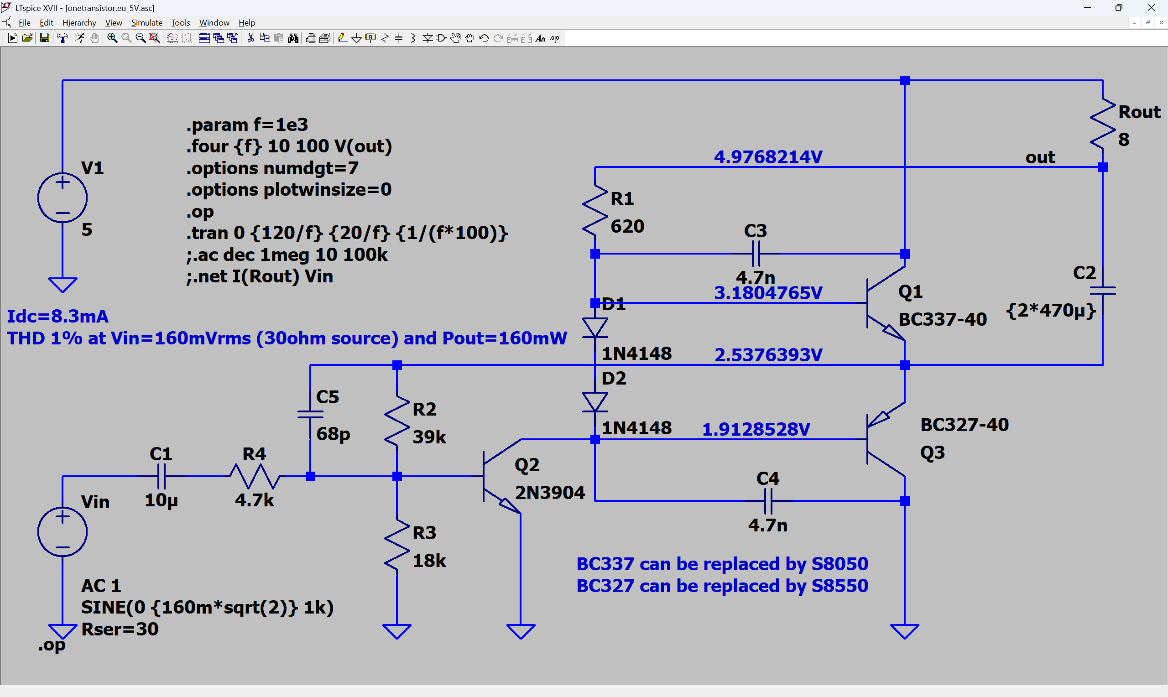
audio_amplifier/doc/simple_final_amplifier.png
