LieBtrau/MegawattKS_Radio_Design_101/CB-CC_amplifier/doc/meas_input_impedance.png

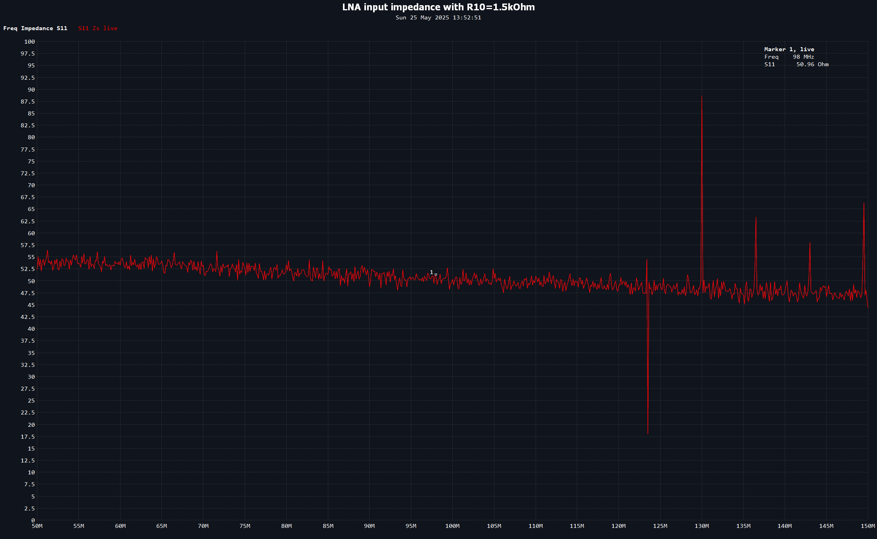
CB-CC_amplifier/doc/meas_input_impedance.png
