LieBtrau/MegawattKS_Radio_Design_101/CB-CC_amplifier/doc/nanovna-h4_2025-07-29_15-47-32.png

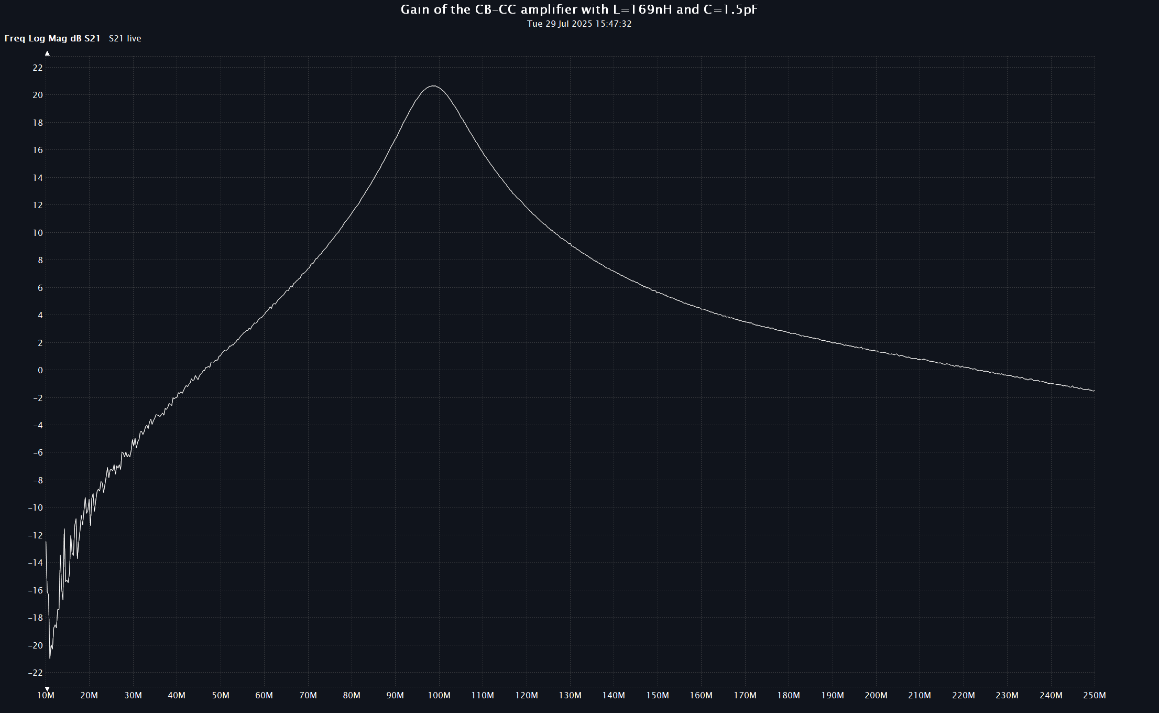
CB-CC_amplifier/doc/nanovna-h4_2025-07-29_15-47-32.png
