LieBtrau/MegawattKS_Radio_Design_101/CB-CC_amplifier/doc/nanovna-h4_2025-07-30_20-36-39.png

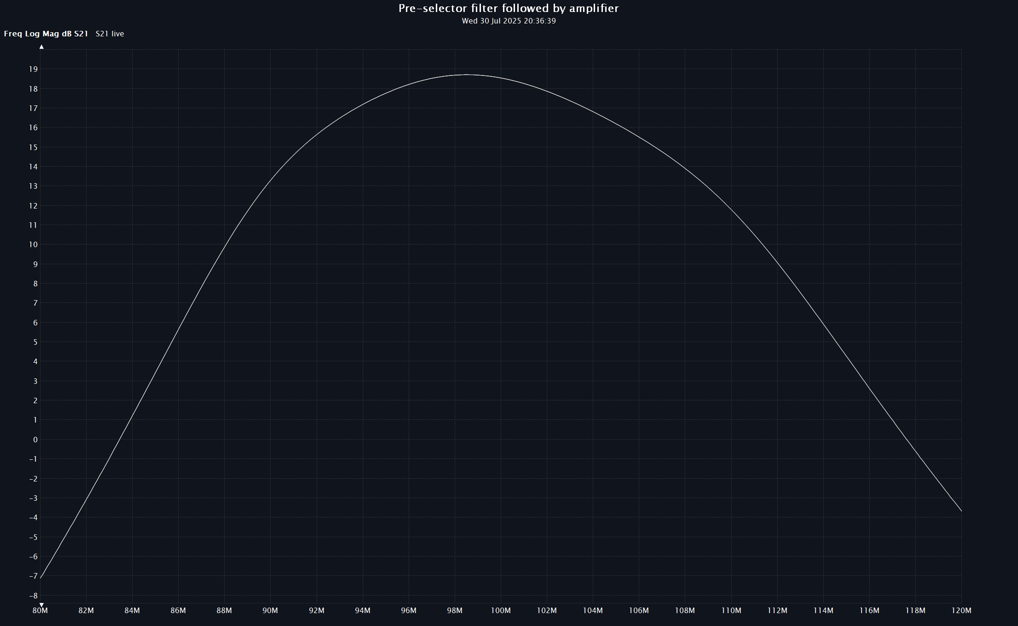
CB-CC_amplifier/doc/nanovna-h4_2025-07-30_20-36-39.png
