LieBtrau/MegawattKS_Radio_Design_101/CB-CC_amplifier/doc/nanovna-h4_2025-07-30_20-41-13.png

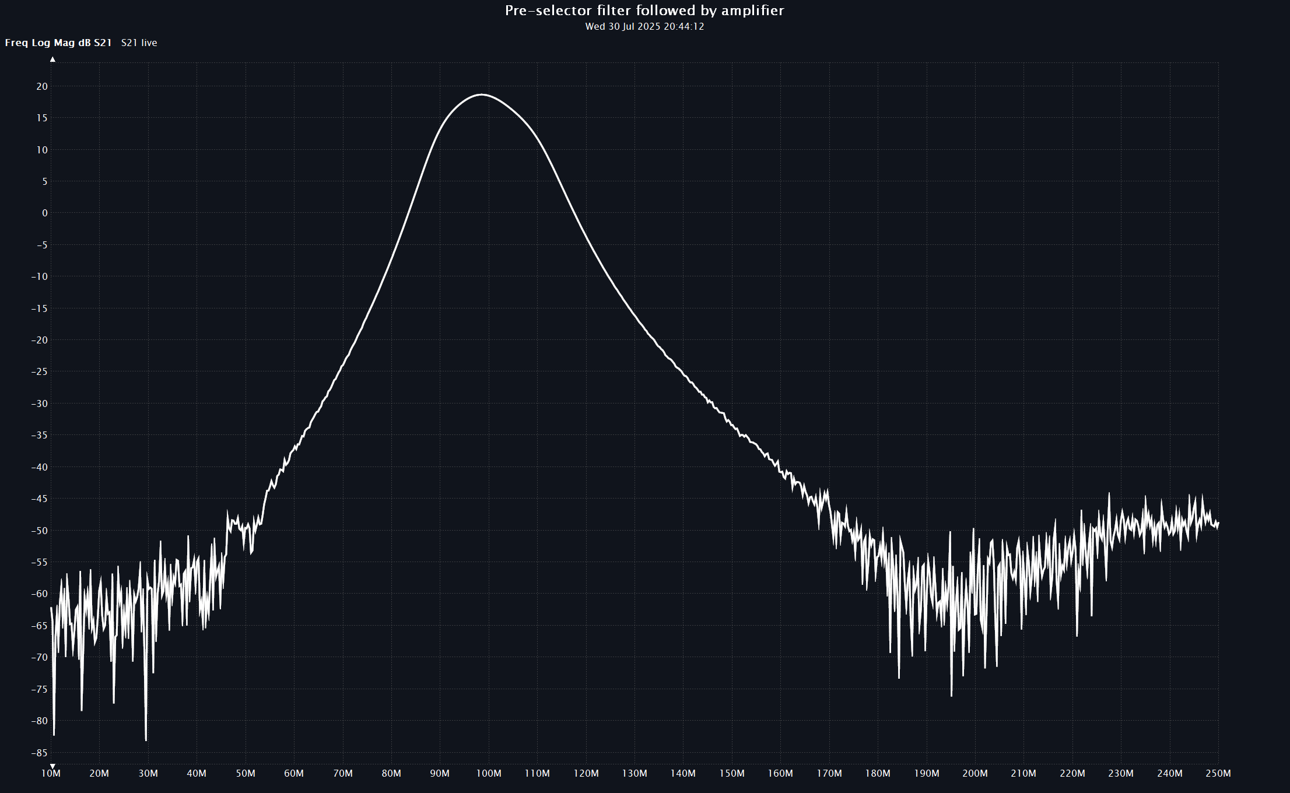
CB-CC_amplifier/doc/nanovna-h4_2025-07-30_20-41-13.png
