LieBtrau/MegawattKS_Radio_Design_101/CB-CC_amplifier/doc/service_band_gain.png

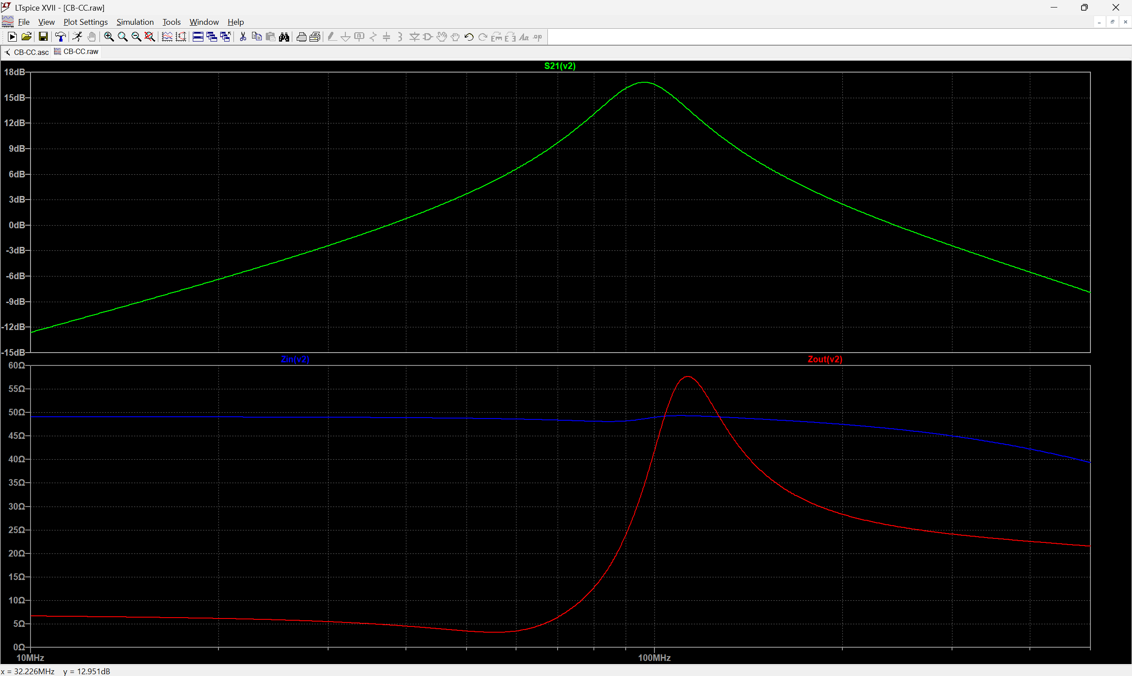
CB-CC_amplifier/doc/service_band_gain.png
