LieBtrau/MegawattKS_Radio_Design_101/detector/doc/buffer_amplifier_f_response.png

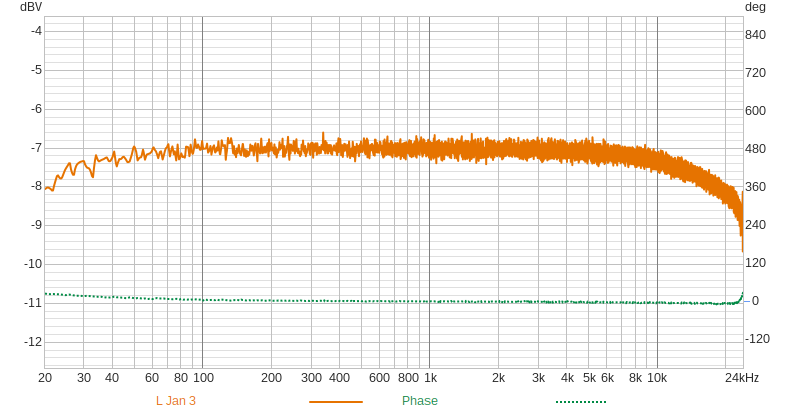
detector/doc/buffer_amplifier_f_response.png
