LieBtrau/MegawattKS_Radio_Design_101/detector/doc/diplexer_simulation.png

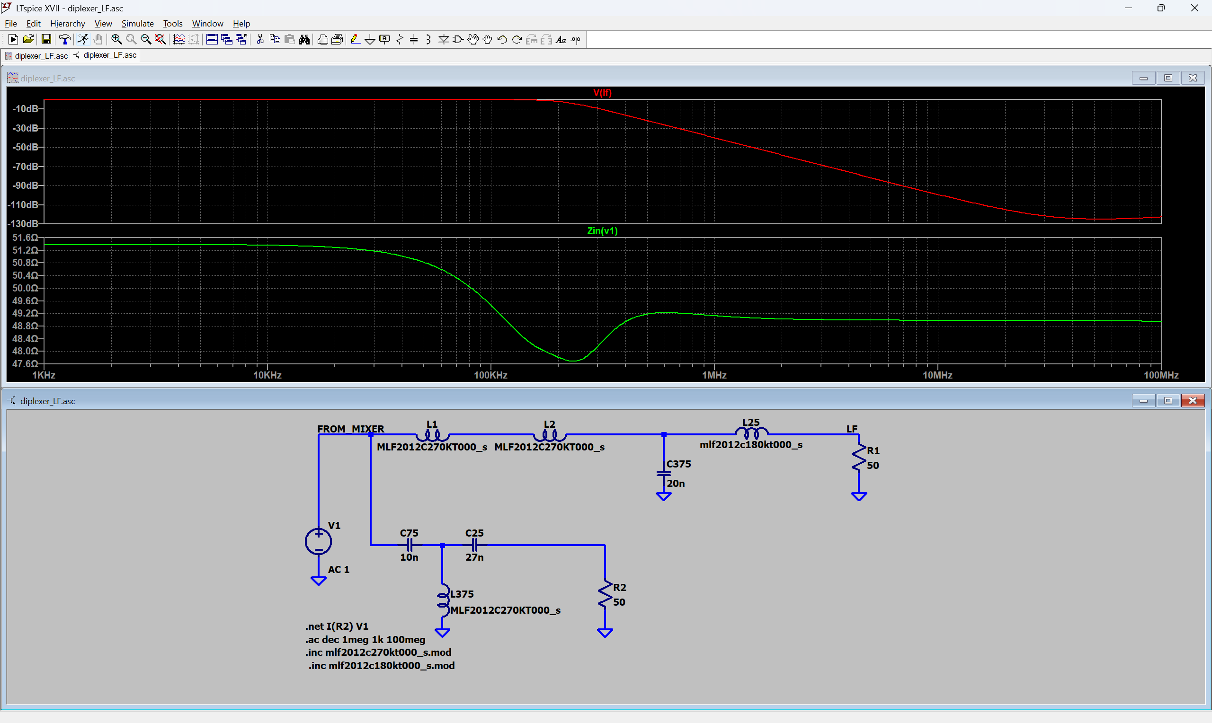
detector/doc/diplexer_simulation.png
