LieBtrau/MegawattKS_Radio_Design_101/detector/doc/EN1975070522.pdf.jpg

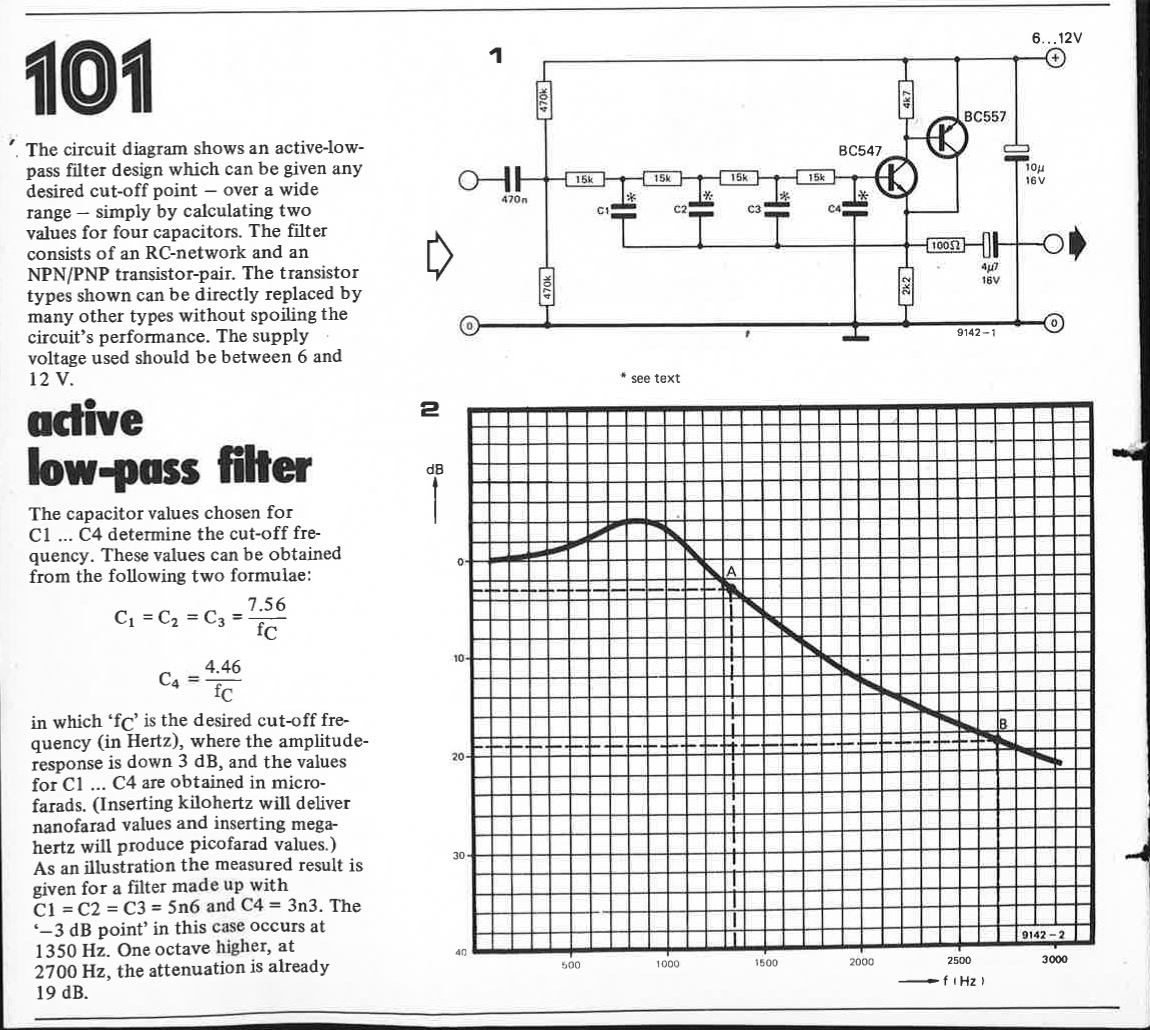
detector/doc/EN1975070522.pdf.jpg
