LieBtrau/MegawattKS_Radio_Design_101/detector/doc/IMG_20260103_141616_264.jpg

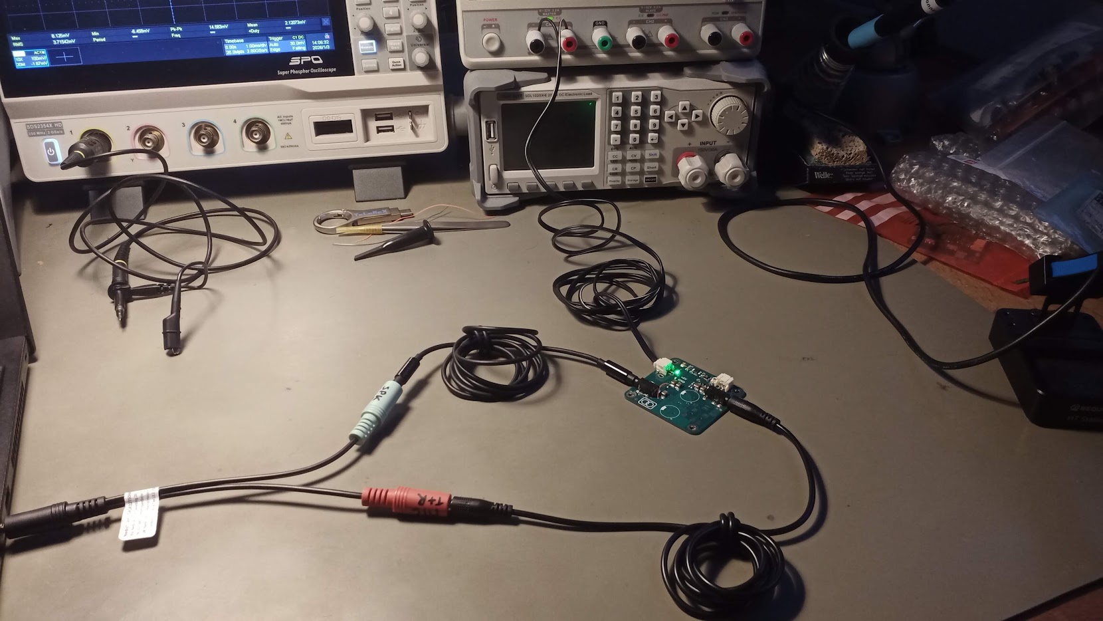
detector/doc/IMG_20260103_141616_264.jpg
