LieBtrau/MegawattKS_Radio_Design_101/detector/doc/IMG_20260103_141625_667.jpg

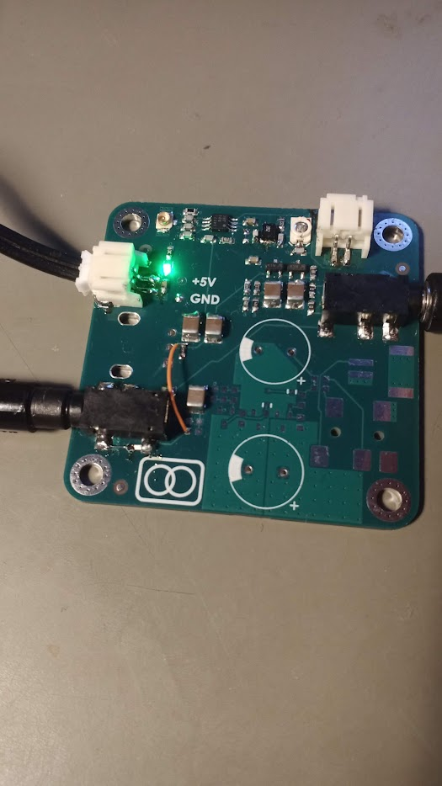
detector/doc/IMG_20260103_141625_667.jpg
