LieBtrau/MegawattKS_Radio_Design_101/detector/doc/lold/EN1975070141.pdf-3897937548.jpg

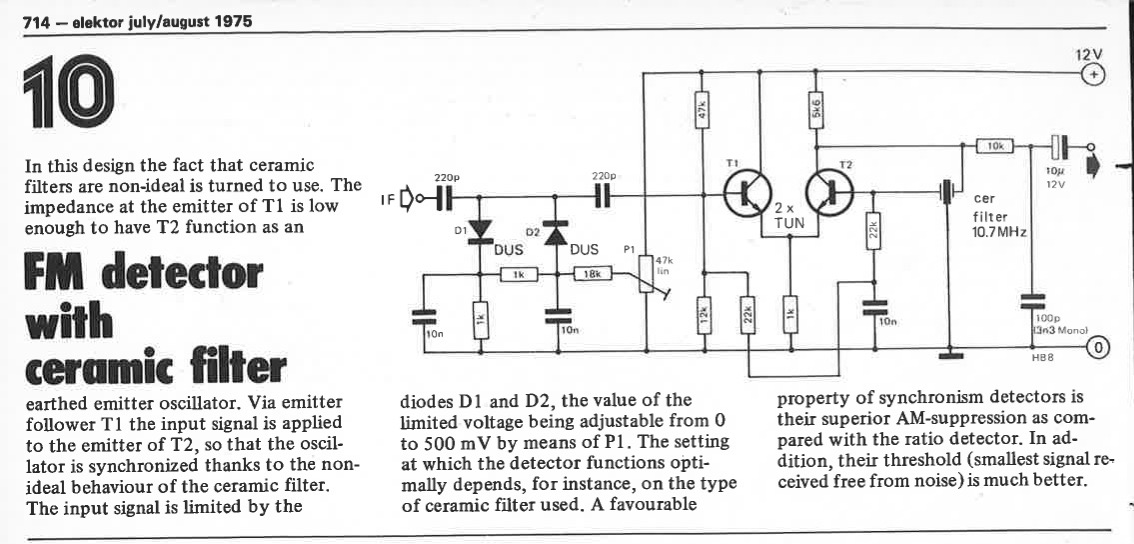
detector/doc/lold/EN1975070141.pdf-3897937548.jpg
