LieBtrau/MegawattKS_Radio_Design_101/detector/doc/NBFM_Crystal_Limiter-Discriminator-3676772606.gif

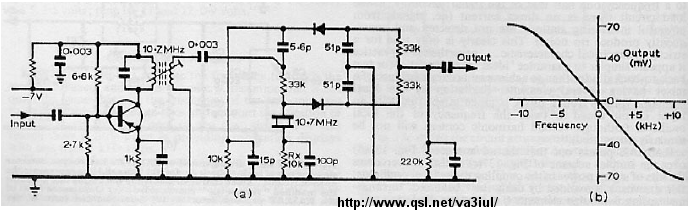
detector/doc/NBFM_Crystal_Limiter-Discriminator-3676772606.gif
