LieBtrau/MegawattKS_Radio_Design_101/detector/doc/OIP-2725269988_audio_filter.jpg

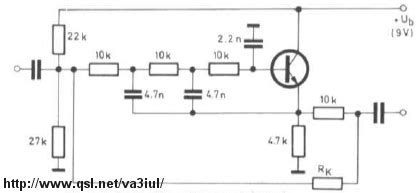
detector/doc/OIP-2725269988_audio_filter.jpg
