LieBtrau/MegawattKS_Radio_Design_101/detector/doc/OIP-4077464096_audio_filter2.jpg

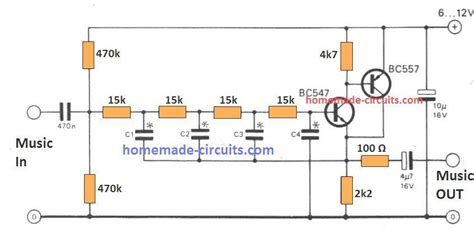
detector/doc/OIP-4077464096_audio_filter2.jpg
