LieBtrau/MegawattKS_Radio_Design_101/detector/doc/pulsecount/microFM.png

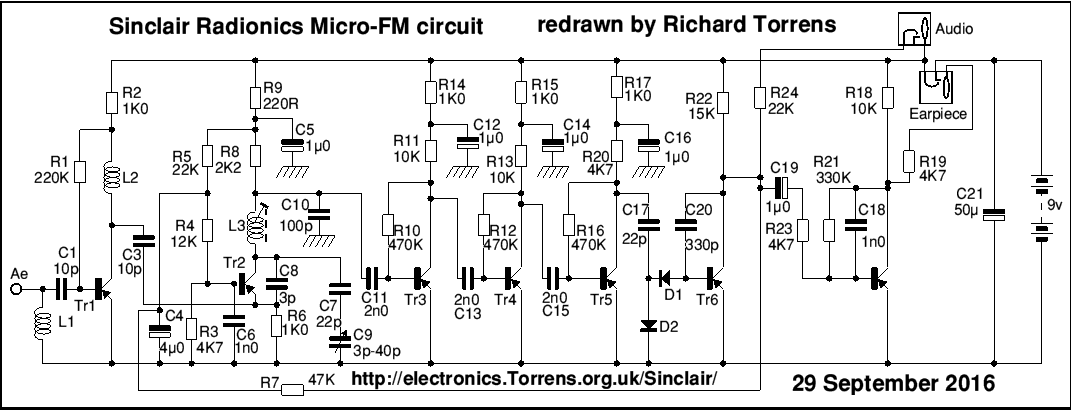
detector/doc/pulsecount/microFM.png
