LieBtrau/MegawattKS_Radio_Design_101/detector/doc/screenshots/SDS2354X_HD_PNG_2.png

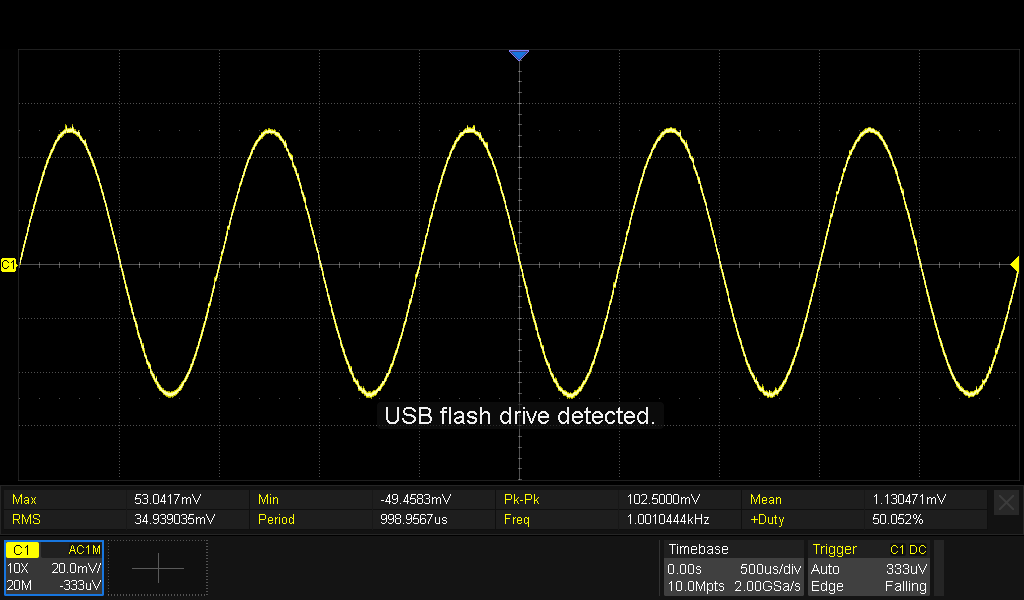
detector/doc/screenshots/SDS2354X_HD_PNG_2.png
