LieBtrau/MegawattKS_Radio_Design_101/detector/doc/weiss/weiss-evolutie_20100818fet.png

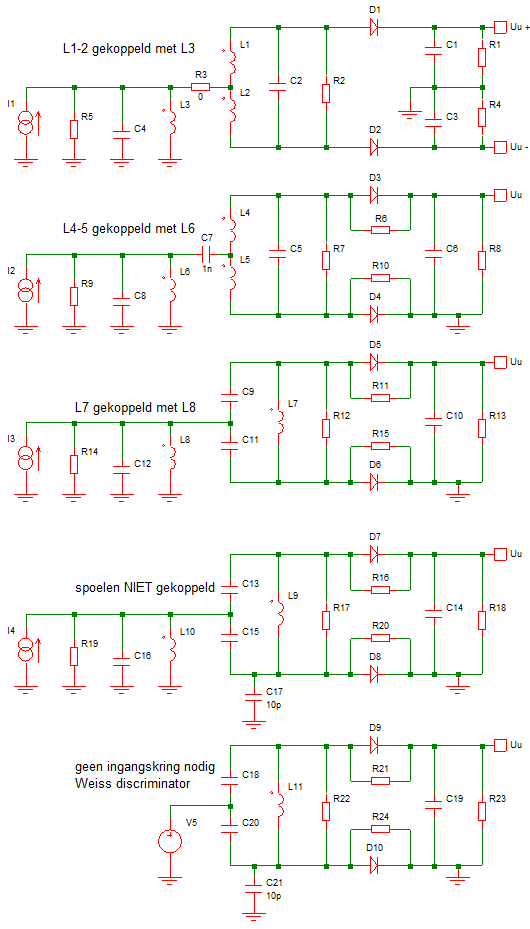
detector/doc/weiss/weiss-evolutie_20100818fet.png
