LieBtrau/MegawattKS_Radio_Design_101/diplexer_filter_IF_port/doc/nanovna-h4_2025-08-15_17-48-01.png

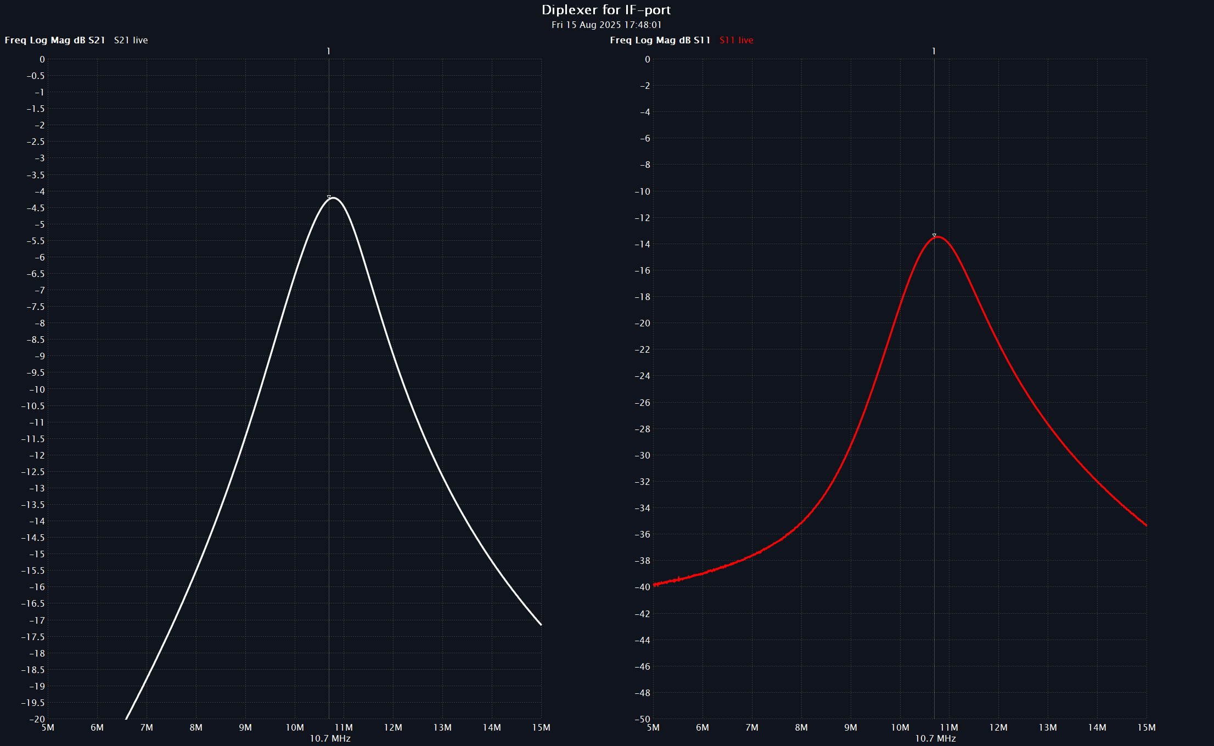
diplexer_filter_IF_port/doc/nanovna-h4_2025-08-15_17-48-01.png
