LieBtrau/MegawattKS_Radio_Design_101/diplexer_filter_IF_port/doc/nanovna-h4_2025-09-21_20-21-28.png

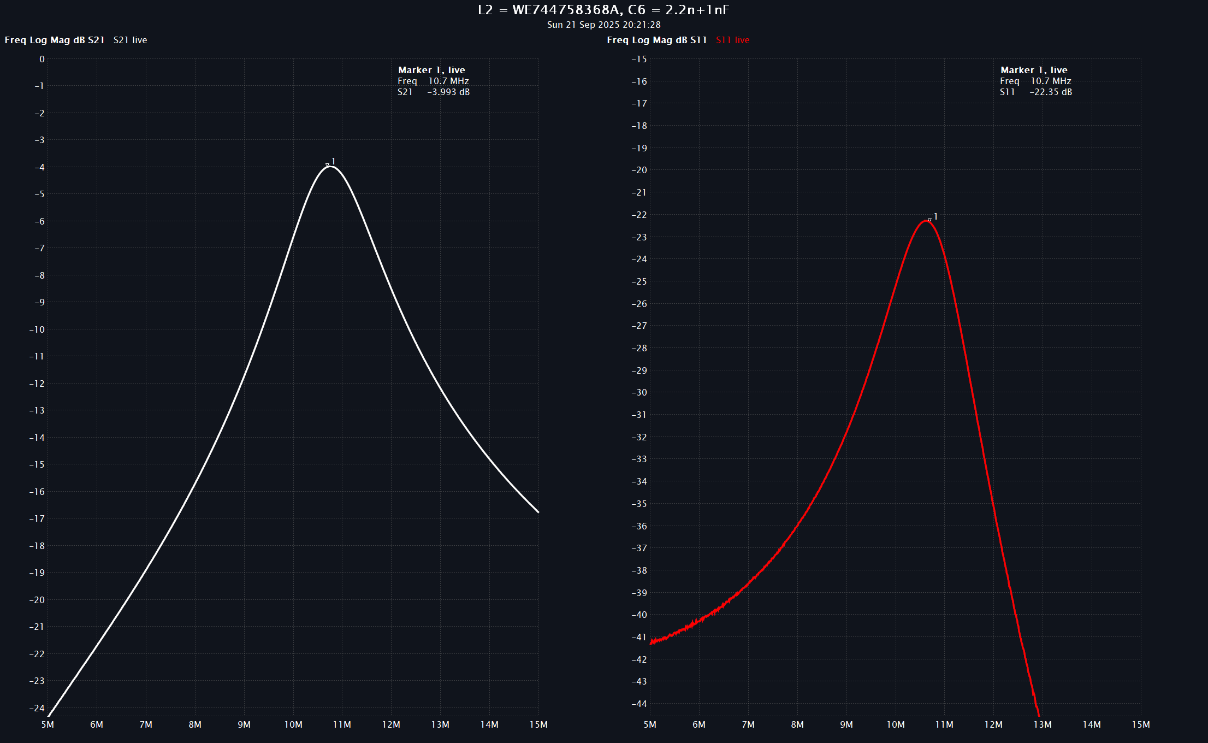
diplexer_filter_IF_port/doc/nanovna-h4_2025-09-21_20-21-28.png
