LieBtrau/MegawattKS_Radio_Design_101/diplexer_filter_RF_port/doc/nanovna-h4_2025-08-15_17-11-01.png

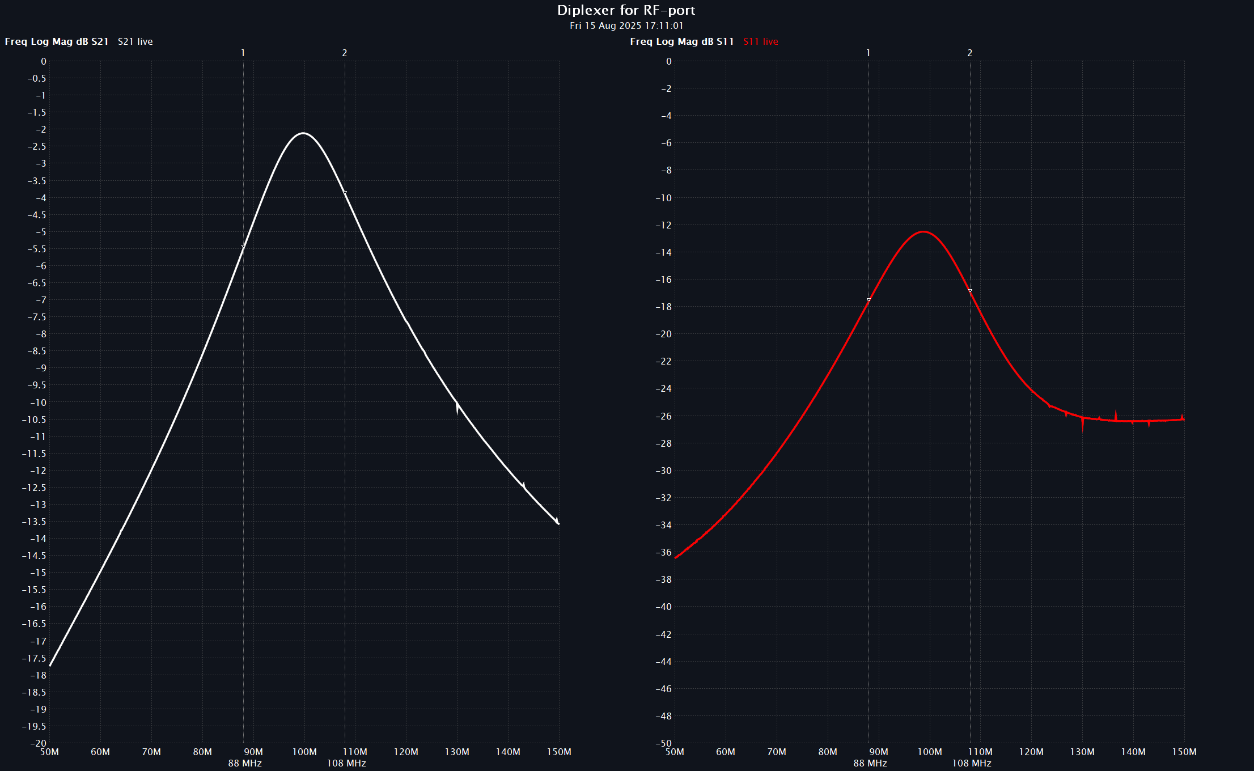
diplexer_filter_RF_port/doc/nanovna-h4_2025-08-15_17-11-01.png
