LieBtrau/MegawattKS_Radio_Design_101/doc/radio_kit/AliExpress_FM_radio_kit.png

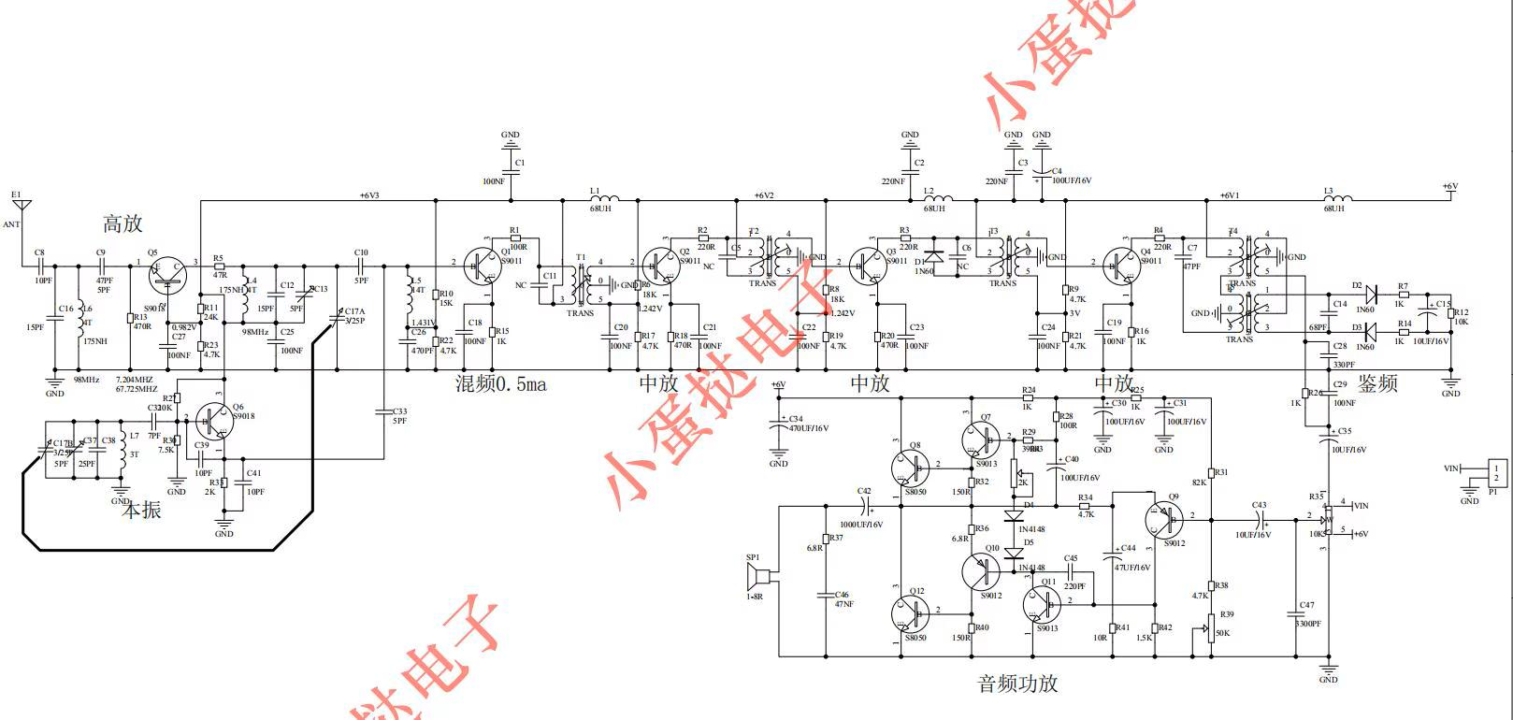
doc/radio_kit/AliExpress_FM_radio_kit.png
