LieBtrau/MegawattKS_Radio_Design_101/IF1_amp/doc/IF3-simulation.png

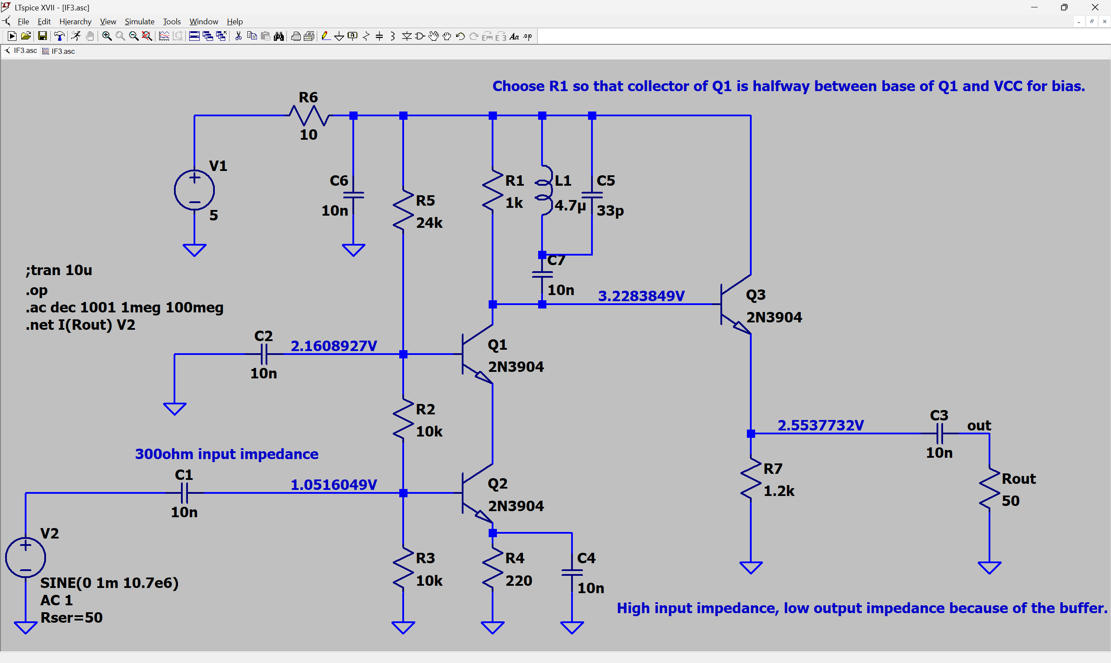
IF1_amp/doc/IF3-simulation.png
