LieBtrau/MegawattKS_Radio_Design_101/IF1_amp/doc/nanovna-h4_2025-11-04_21-05-30.png

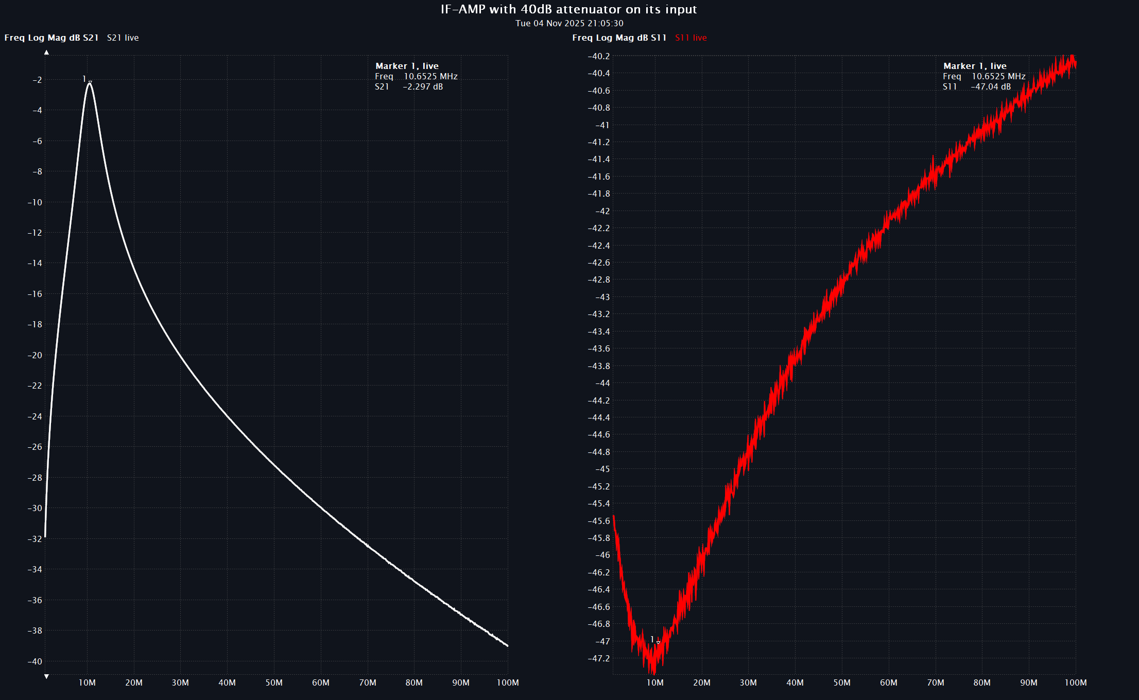
IF1_amp/doc/nanovna-h4_2025-11-04_21-05-30.png
