LieBtrau/MegawattKS_Radio_Design_101/IF1_amp/doc/series_resistance_vsup.png

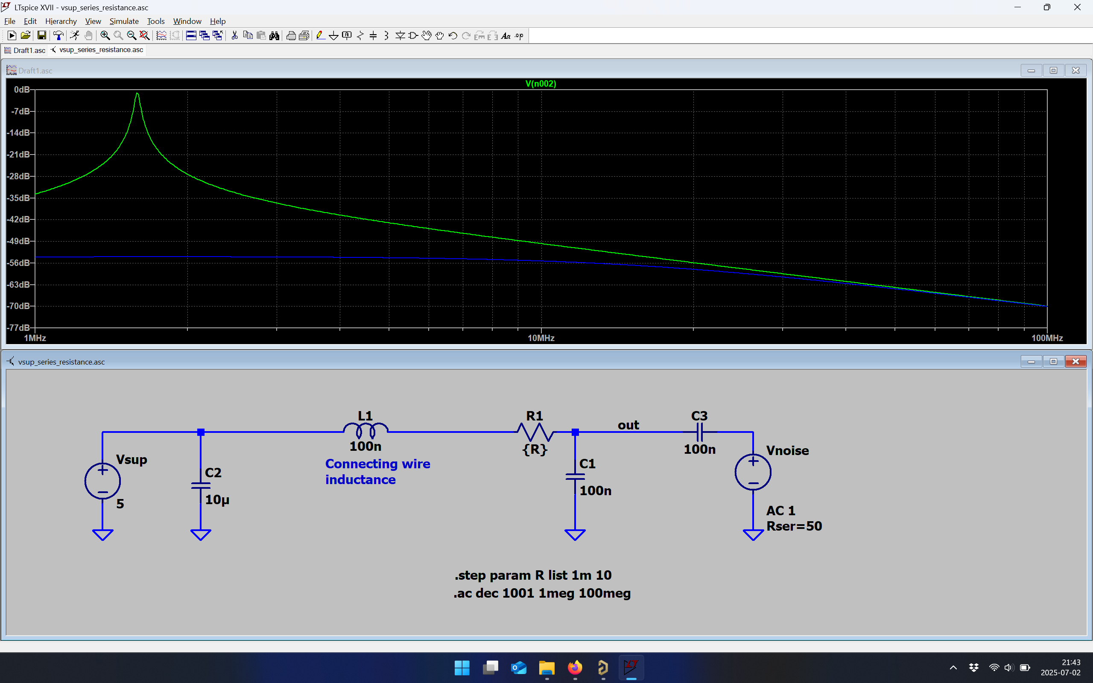
IF1_amp/doc/series_resistance_vsup.png
