LieBtrau/MegawattKS_Radio_Design_101/IF1_mixer/doc/DBM_vs_DDBM.png

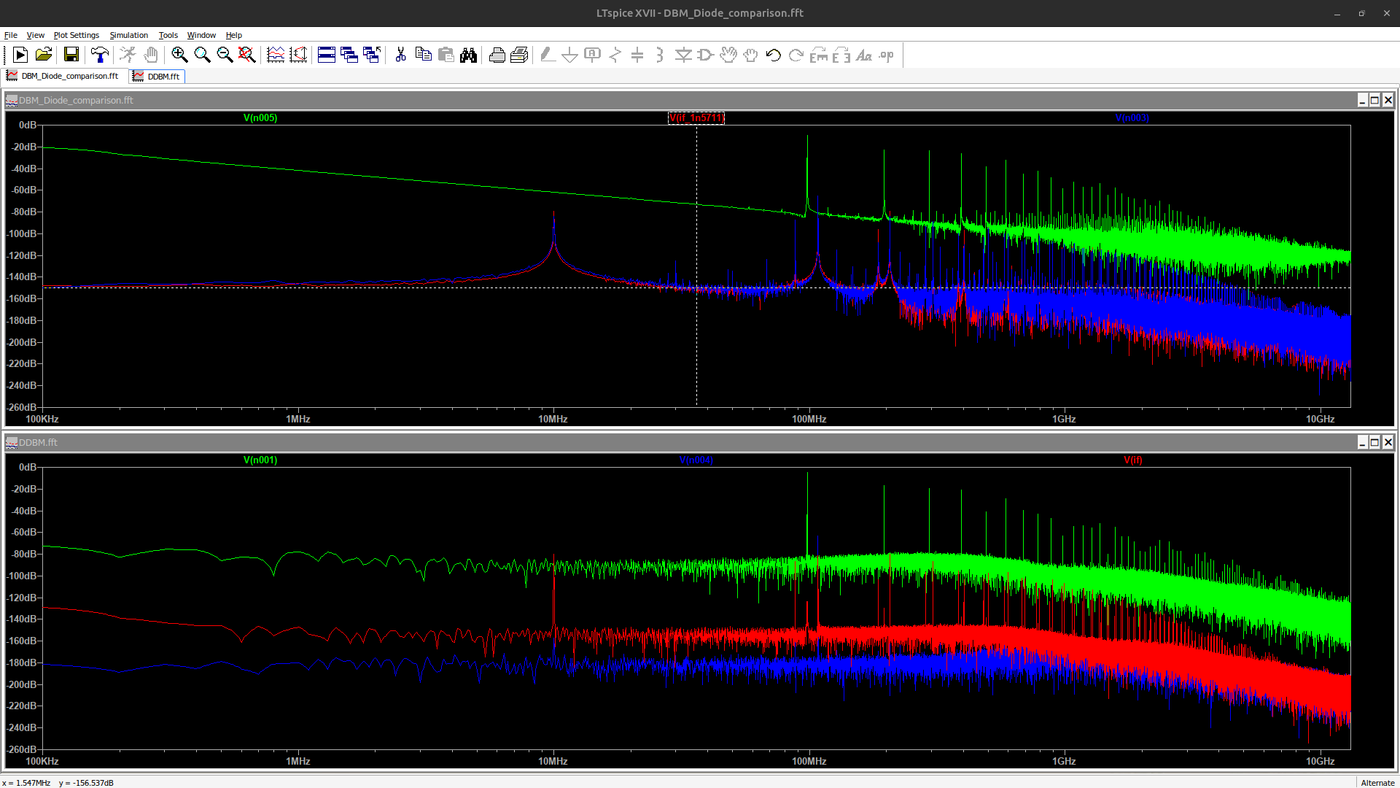
IF1_mixer/doc/DBM_vs_DDBM.png
