LieBtrau/MegawattKS_Radio_Design_101/IF1_mixer/doc/simulation/1N5711_vs_BAT15.png

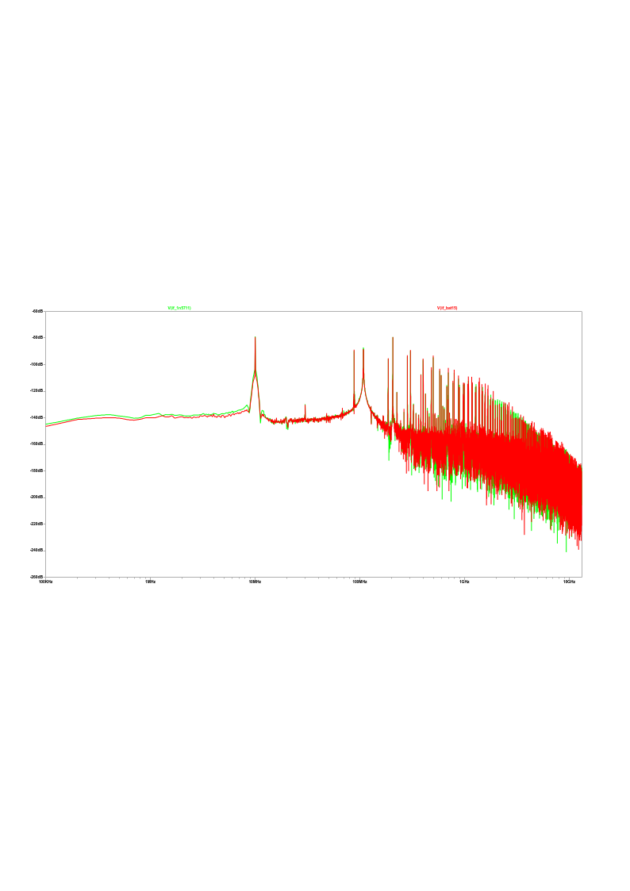
IF1_mixer/doc/simulation/1N5711_vs_BAT15.png
