LieBtrau/MegawattKS_Radio_Design_101/IF1_mixer/doc/simulation/Screenshot from 2026-06-19 21-50-04.png

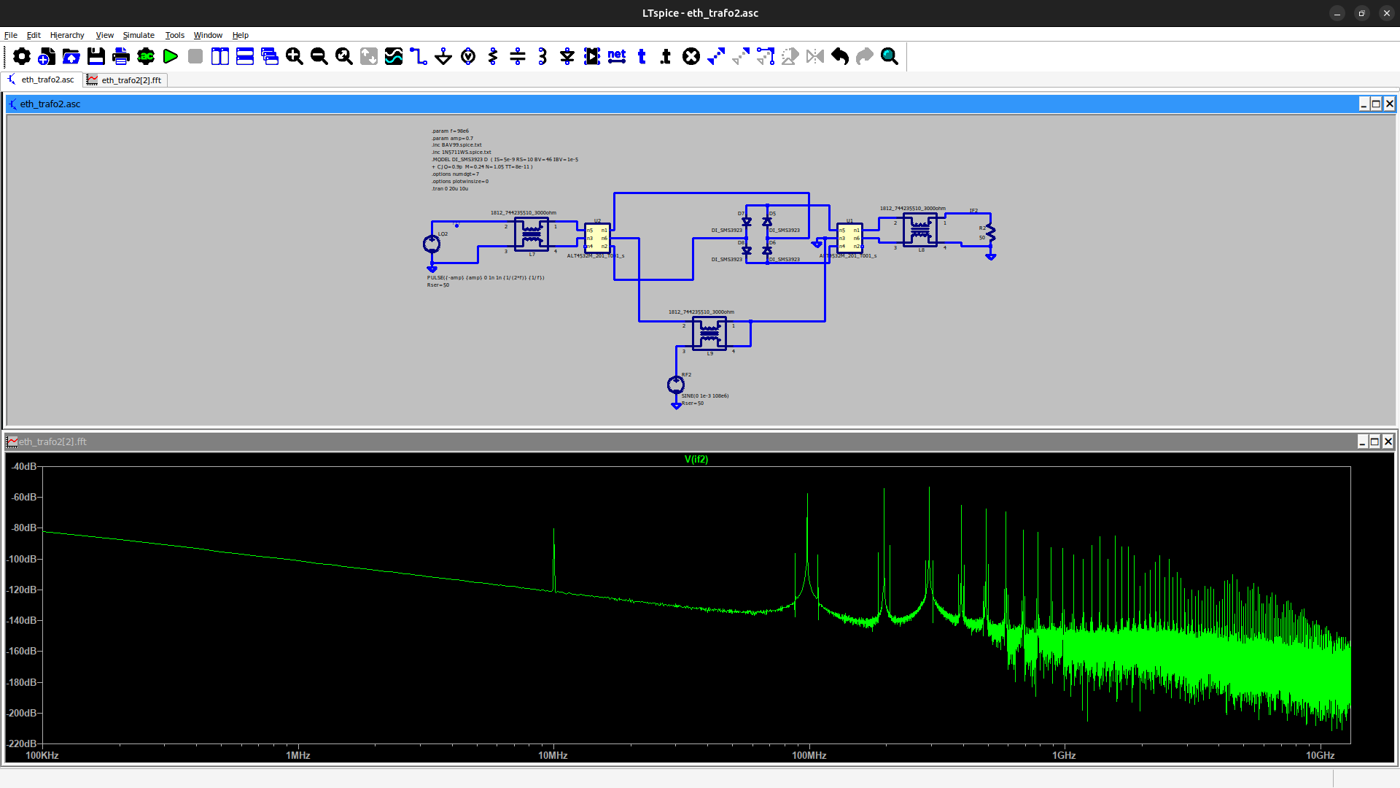
IF1_mixer/doc/simulation/Screenshot from 2026-06-19 21-50-04.png
