LieBtrau/MegawattKS_Radio_Design_101/LNA/doc/IMG_20250729_211953_138.jpg

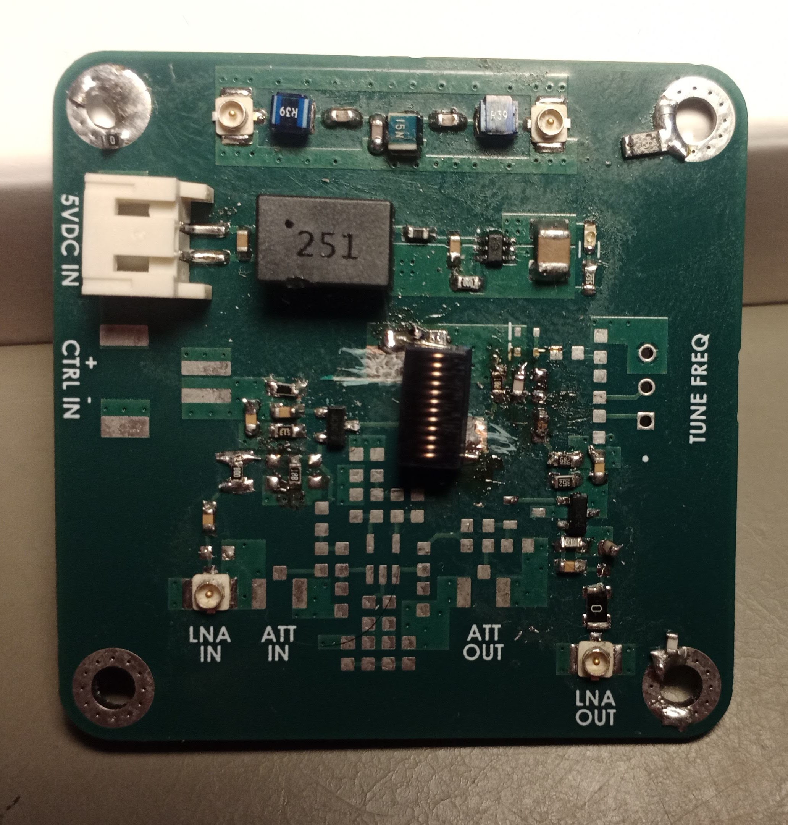
LNA/doc/IMG_20250729_211953_138.jpg
