LieBtrau/MegawattKS_Radio_Design_101/LNA/doc/IMG_20250730_204305_936.jpg

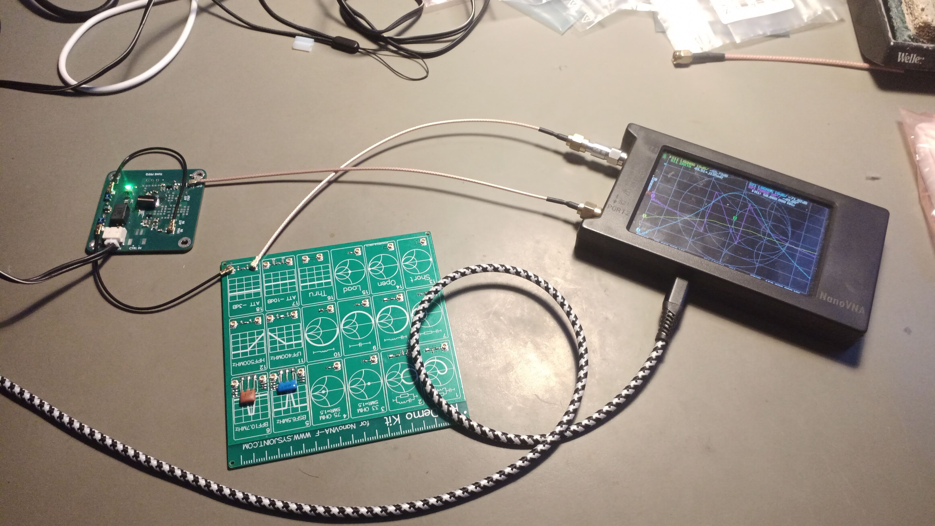
LNA/doc/IMG_20250730_204305_936.jpg
