LieBtrau/MegawattKS_Radio_Design_101/LNA/doc/simulation/2_Av_no_load.png

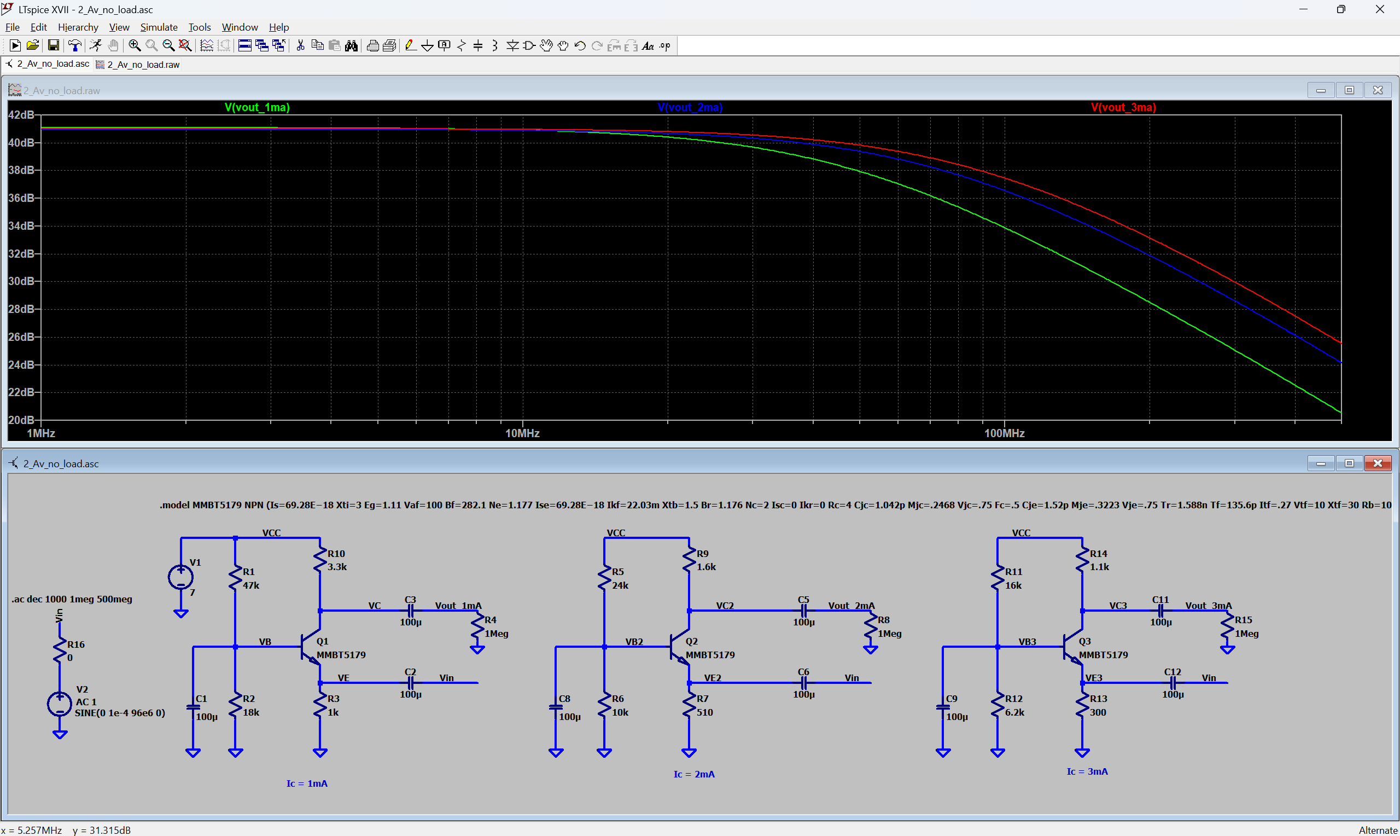
LNA/doc/simulation/2_Av_no_load.png
