LieBtrau/MegawattKS_Radio_Design_101/LNA/doc/simulation/3_input_impedance.png

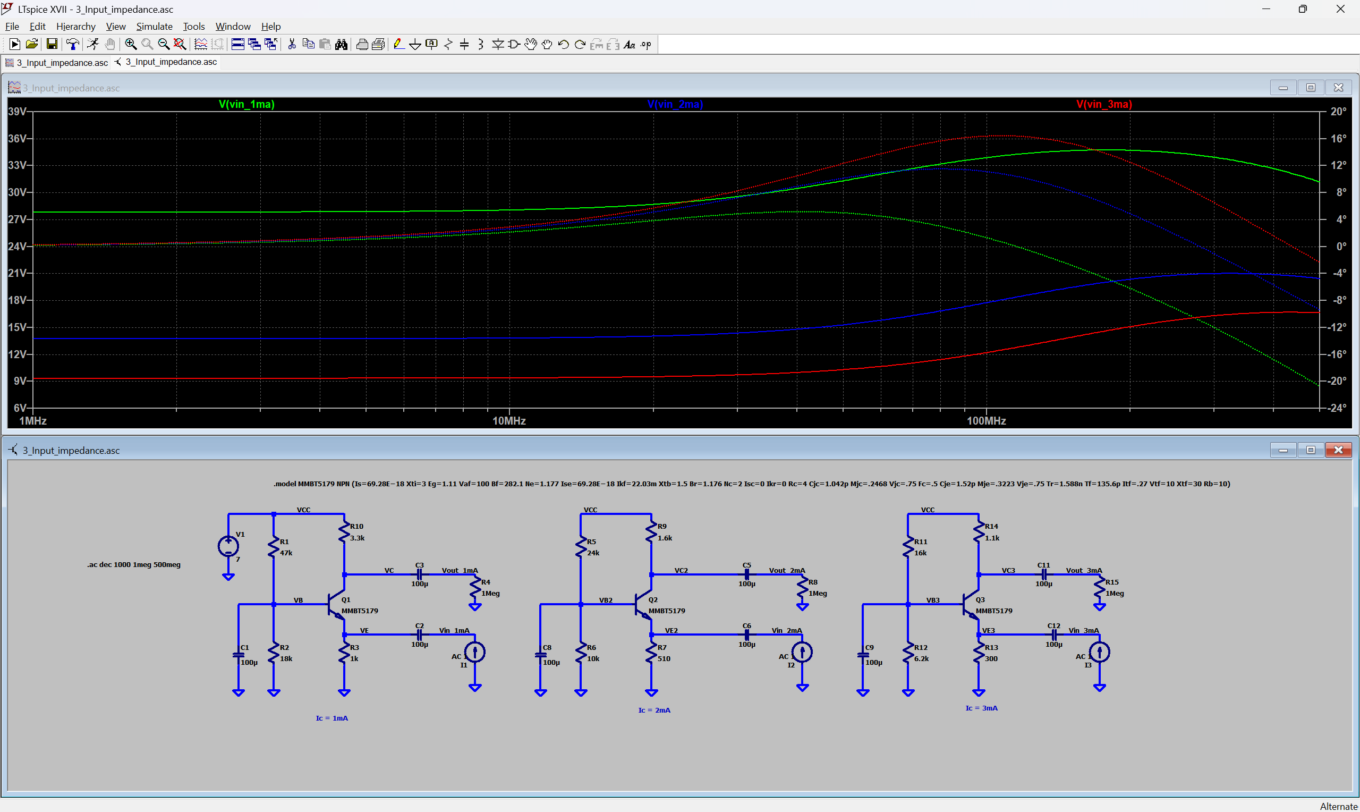
LNA/doc/simulation/3_input_impedance.png
