LieBtrau/MegawattKS_Radio_Design_101/LNA/doc/simulation/4_input_match.png

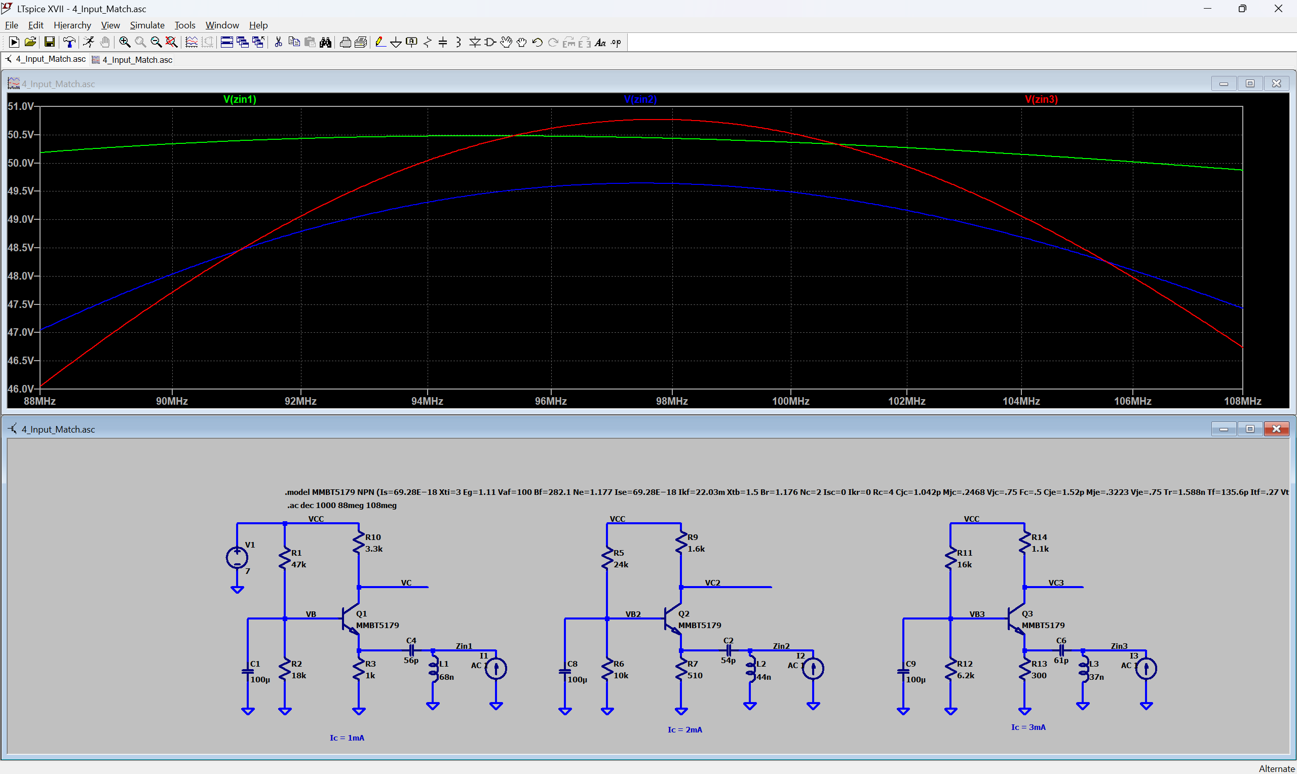
LNA/doc/simulation/4_input_match.png
