LieBtrau/MegawattKS_Radio_Design_101/LNA/doc/simulation/5_output_impedance.png

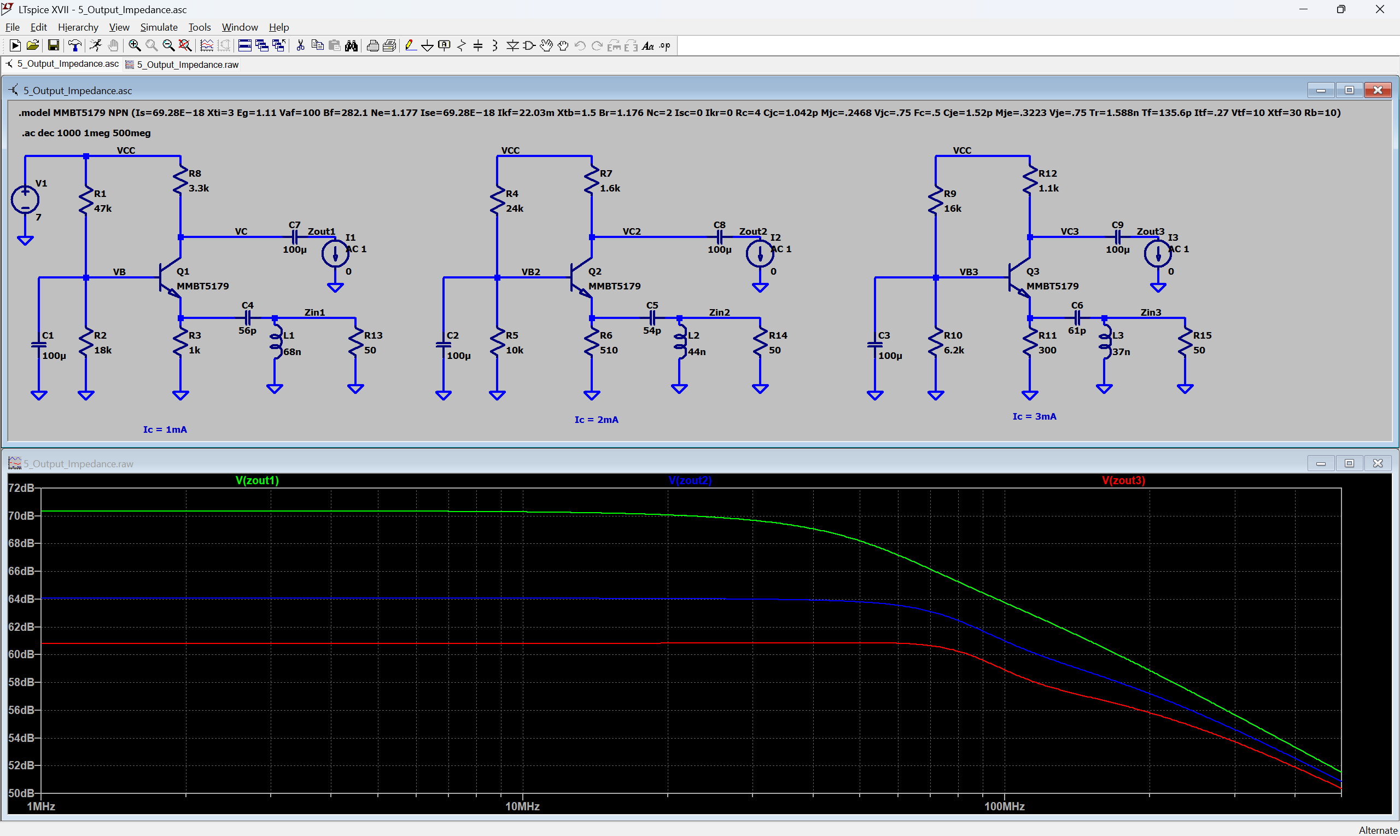
LNA/doc/simulation/5_output_impedance.png
