LieBtrau/MegawattKS_Radio_Design_101/LNA/doc/simulation/6_image_filter.png

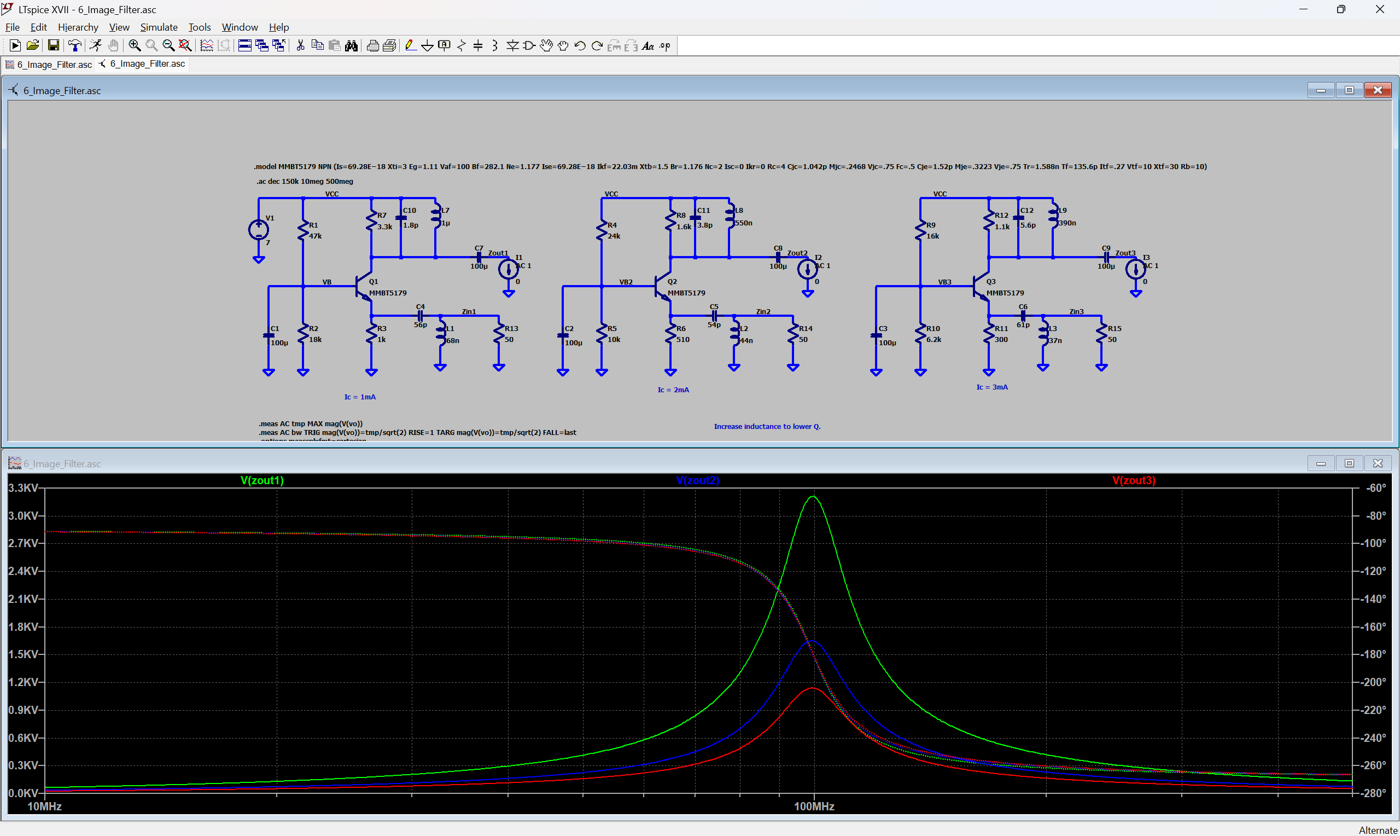
LNA/doc/simulation/6_image_filter.png
