LieBtrau/MegawattKS_Radio_Design_101/LNA/doc/simulation/7_output_match.png

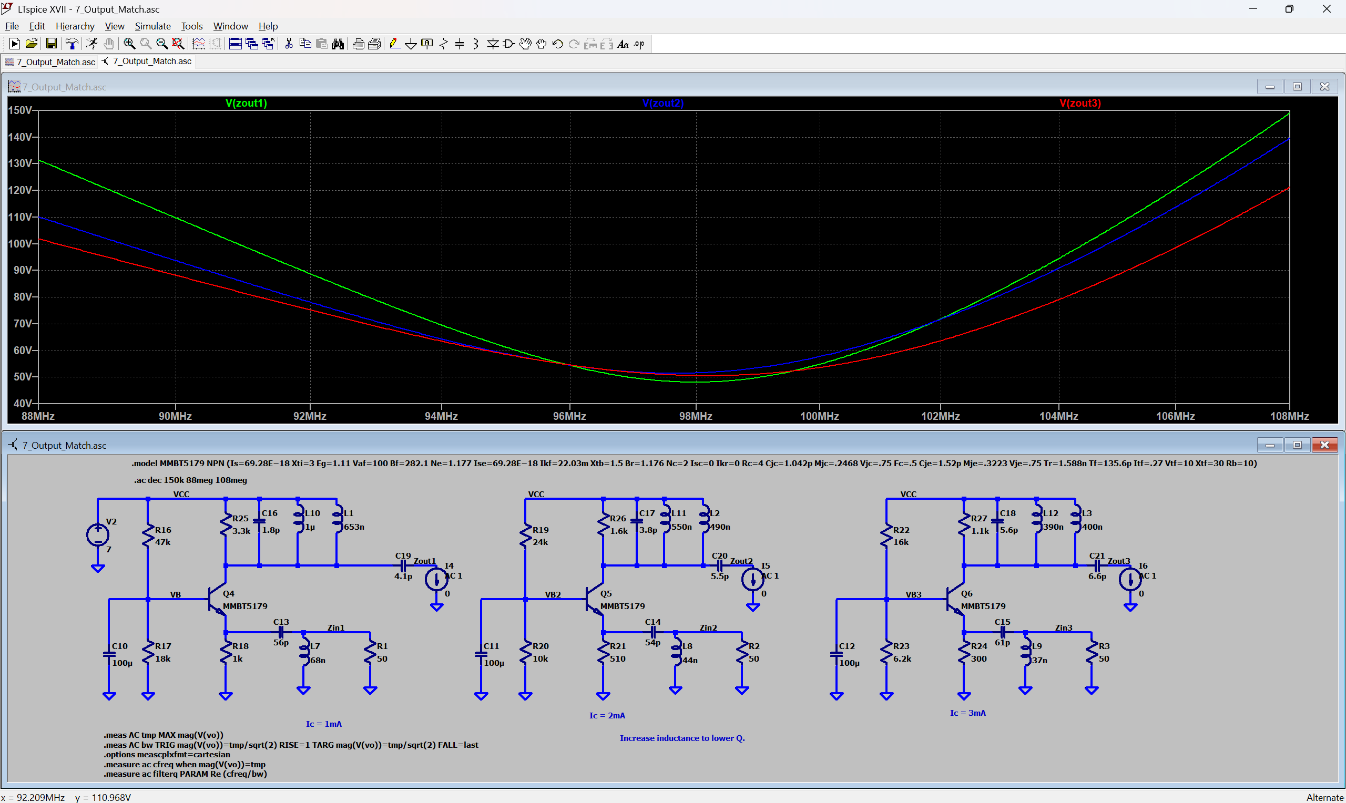
LNA/doc/simulation/7_output_match.png
