LieBtrau/MegawattKS_Radio_Design_101/LNA/doc/simulation/8_wideband_gain.png

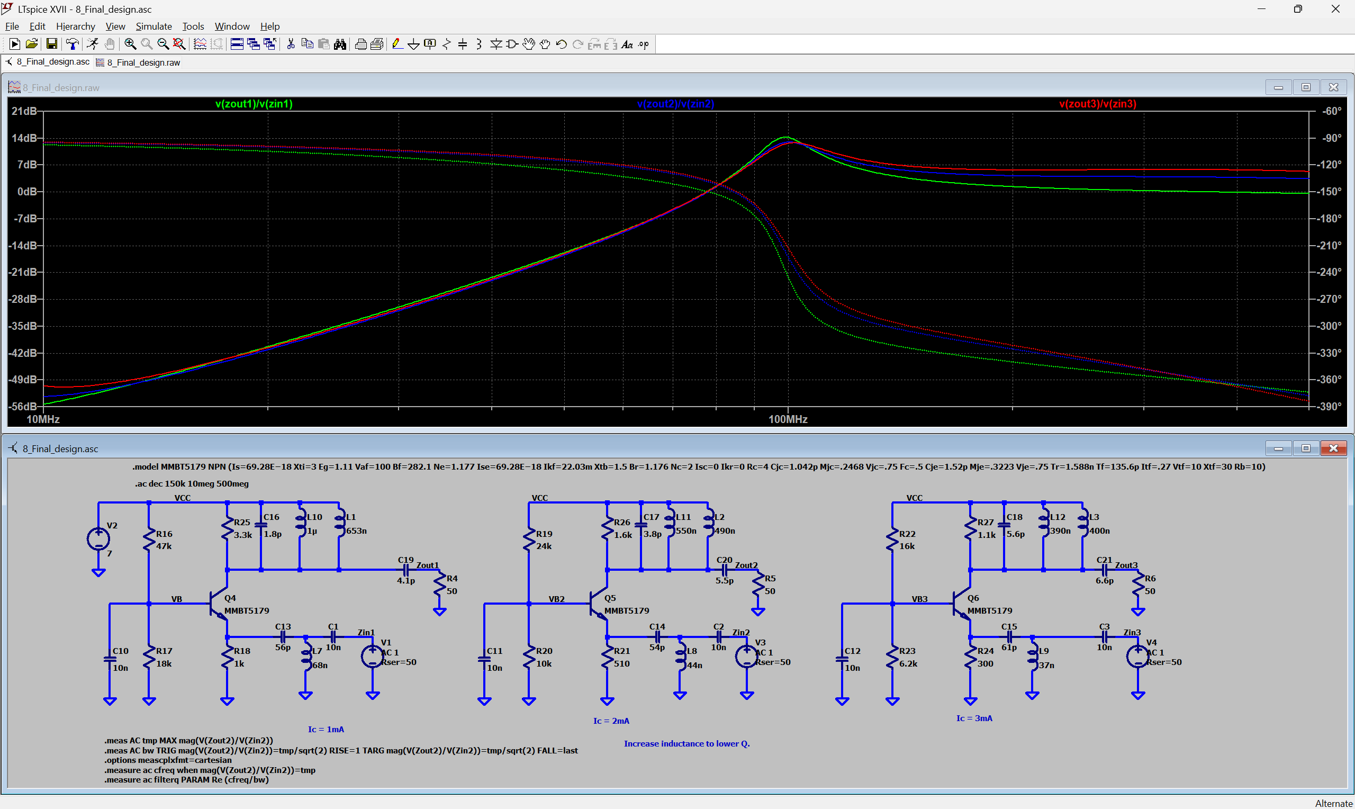
LNA/doc/simulation/8_wideband_gain.png
