LieBtrau/MegawattKS_Radio_Design_101/LNA/doc/simulation/two-port-network.png

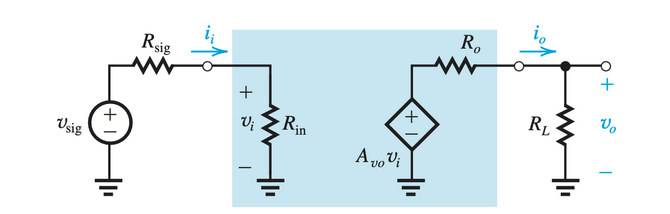
LNA/doc/simulation/two-port-network.png
