LieBtrau/MegawattKS_Radio_Design_101/LO/doc/random_devices_as_varactors.png

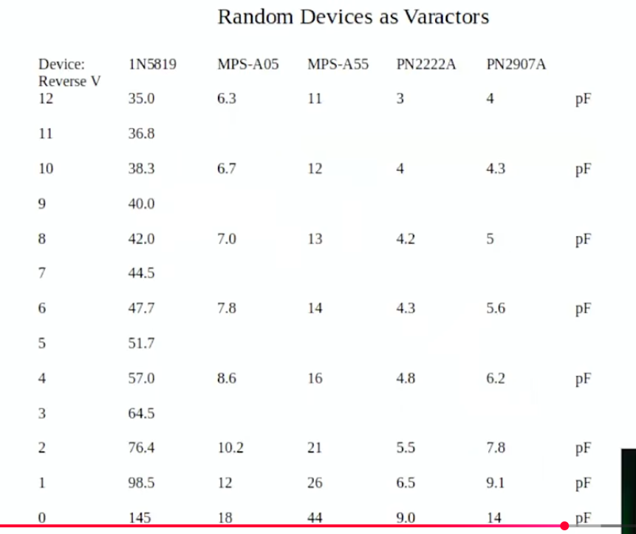
LO/doc/random_devices_as_varactors.png
