LieBtrau/MegawattKS_Radio_Design_101/LO/doc/vackar.png

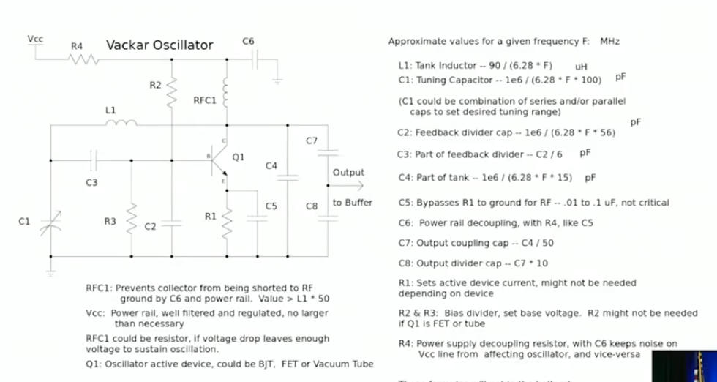
LO/doc/vackar.png
