LieBtrau/MegawattKS_Radio_Design_101/LO/JFET_Clapp/doc/Rutgers_simulation.png

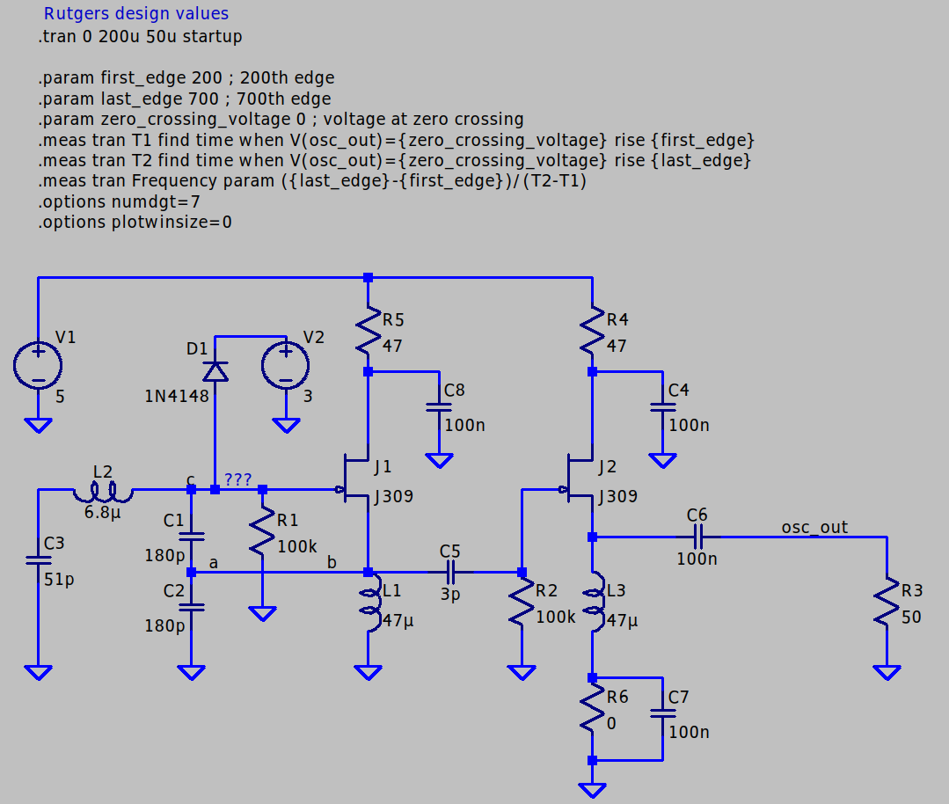
LO/JFET_Clapp/doc/Rutgers_simulation.png
