LieBtrau/MegawattKS_Radio_Design_101/post_mixer_amplifier/doc/nanovna-h4_2025-08-11_21-12-49.png

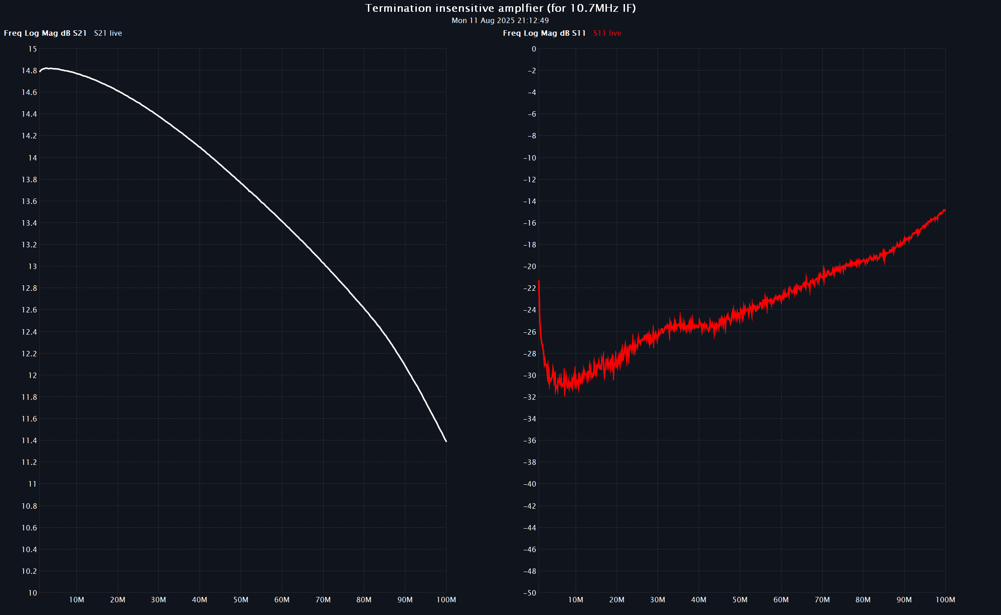
post_mixer_amplifier/doc/nanovna-h4_2025-08-11_21-12-49.png
