LieBtrau/MegawattKS_Radio_Design_101/post_mixer_amplifier/doc/TIA5V_sch.png

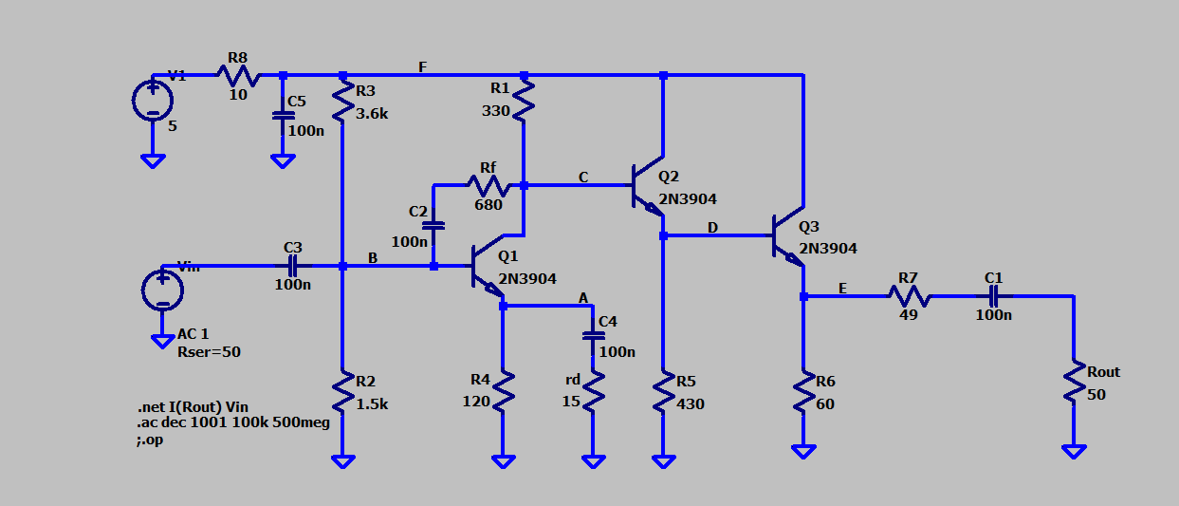
post_mixer_amplifier/doc/TIA5V_sch.png
