LieBtrau/MegawattKS_Radio_Design_101/post_mixer_amplifier/simulation/TIA3_12V_op.png

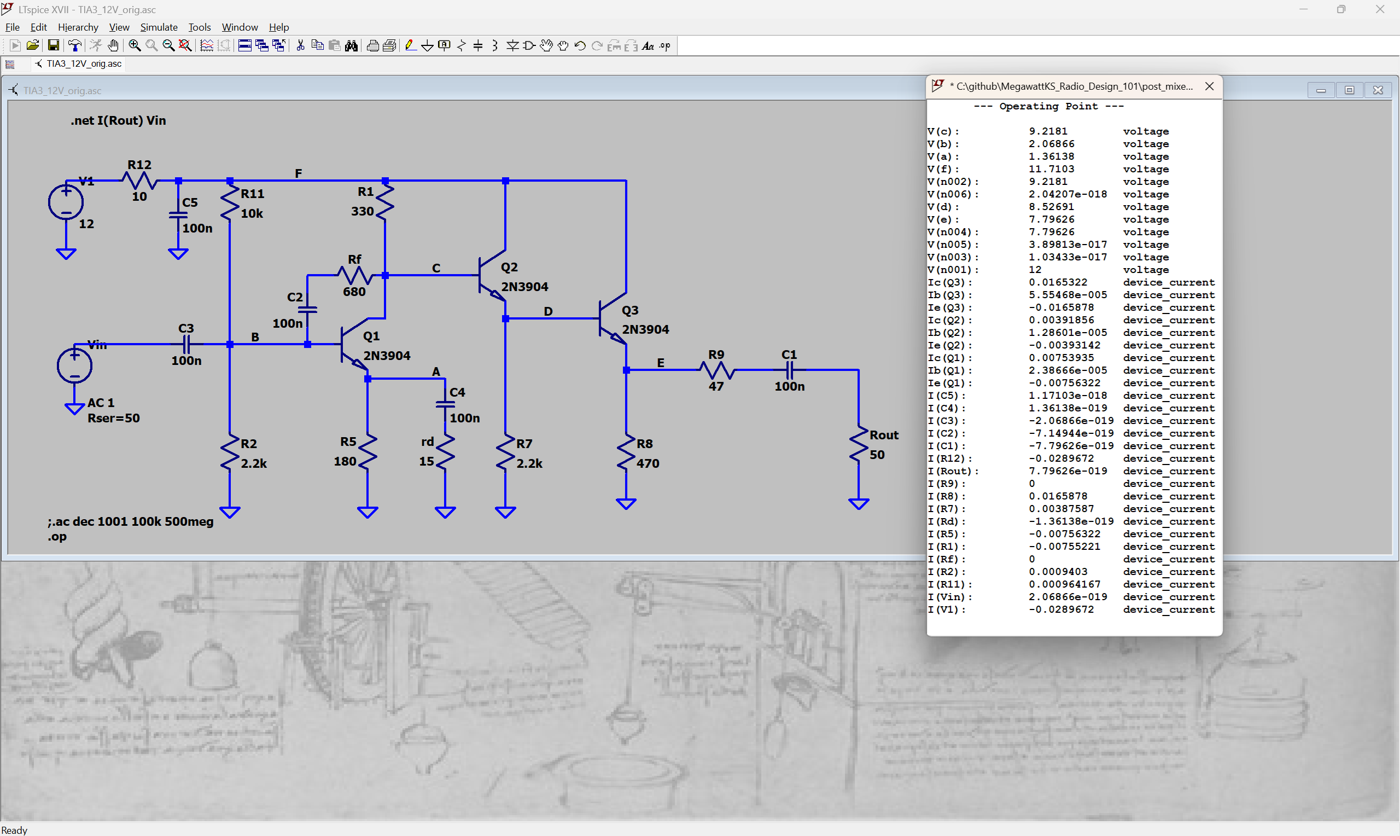
post_mixer_amplifier/simulation/TIA3_12V_op.png
