LieBtrau/MegawattKS_Radio_Design_101/preselector_filter/doc/IMG_20250518_123001_412.jpg

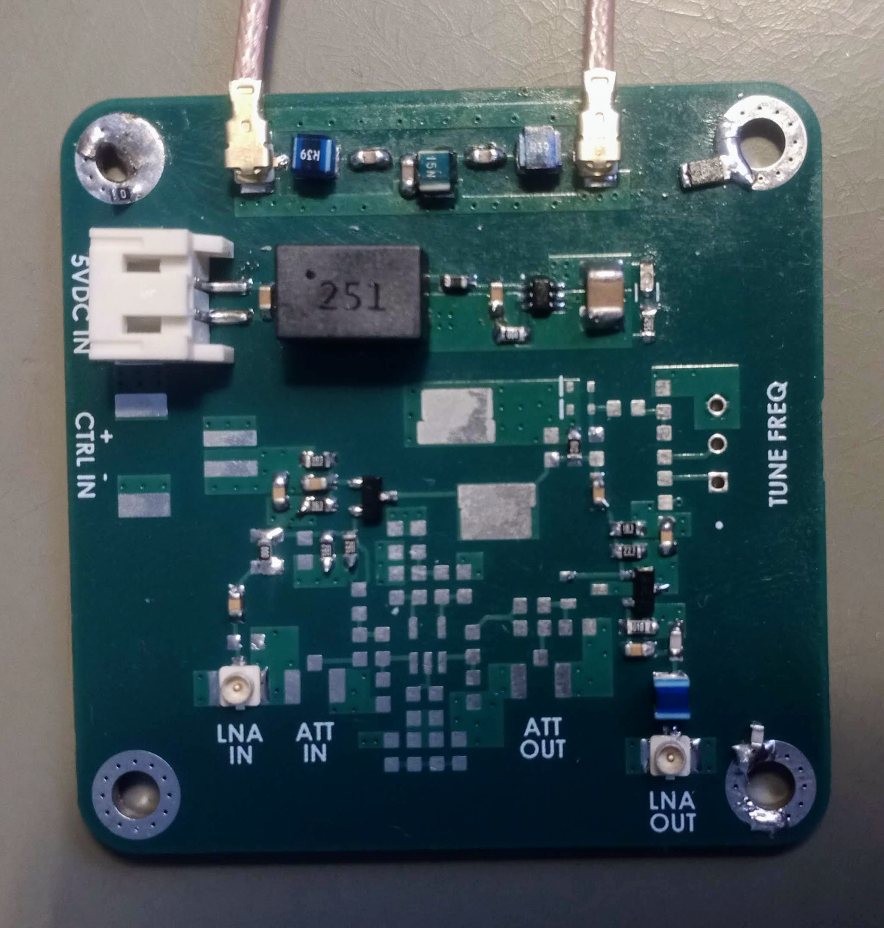
preselector_filter/doc/IMG_20250518_123001_412.jpg
