LieBtrau/MegawattKS_Radio_Design_101/preselector_filter/doc/implementation.png

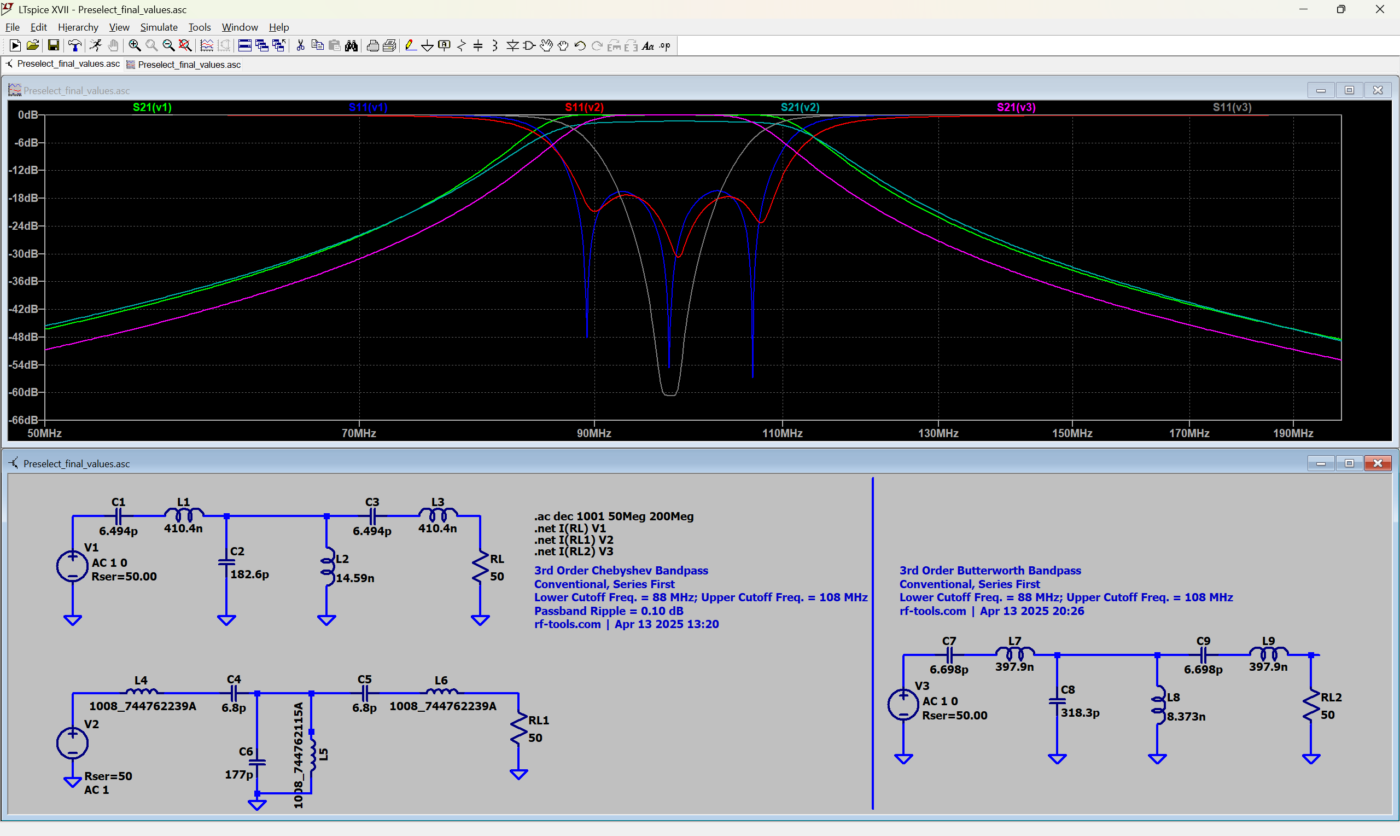
preselector_filter/doc/implementation.png
