LieBtrau/MegawattKS_Radio_Design_101/preselector_filter/doc/nanovna-h4_2025-05-18_12-00-23.png

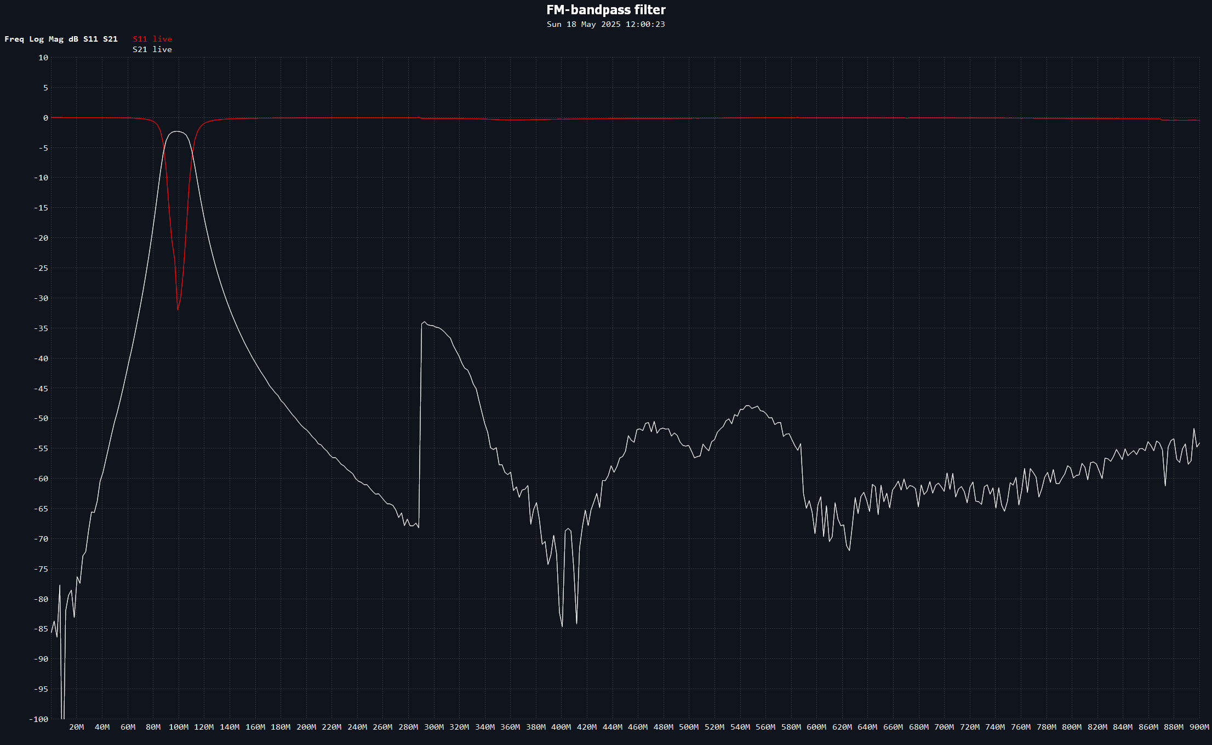
preselector_filter/doc/nanovna-h4_2025-05-18_12-00-23.png
