LieBtrau/MegawattKS_Radio_Design_101/preselector_filter/doc/pre-selector-filter.png

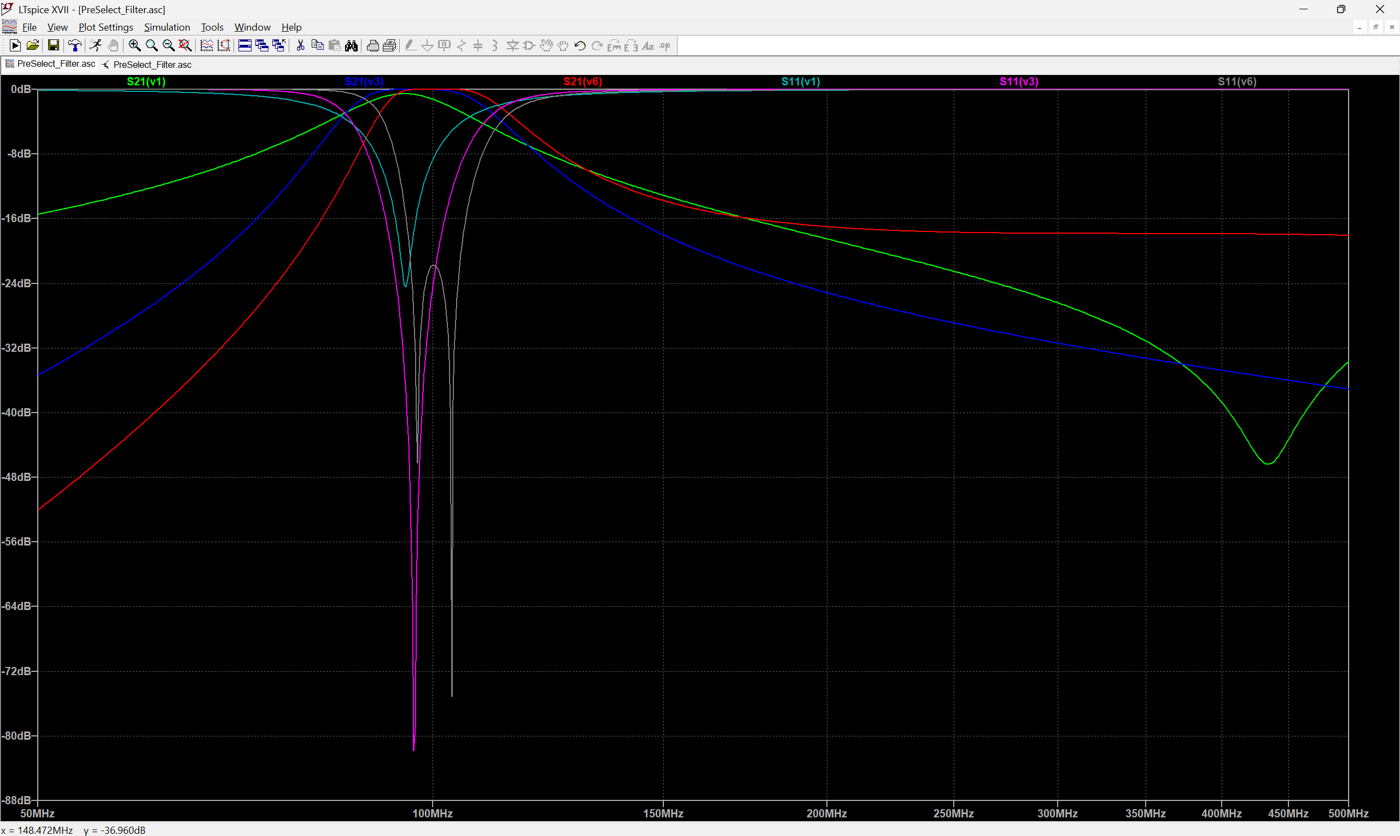
preselector_filter/doc/pre-selector-filter.png
