LieBtrau/MegawattKS_Radio_Design_101/preselector_filter/doc/S21_S11_finished_filter.png

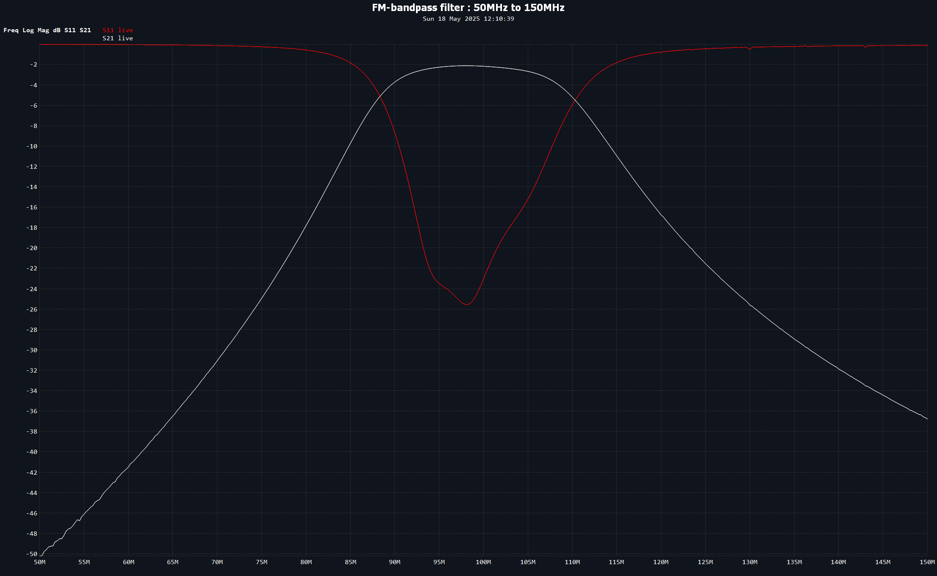
preselector_filter/doc/S21_S11_finished_filter.png
