LieBtrau/MegawattKS_Radio_Design_101/preselector_filter/doc/WTWH_Bandpass-Filters_Pt2_Fig1.png

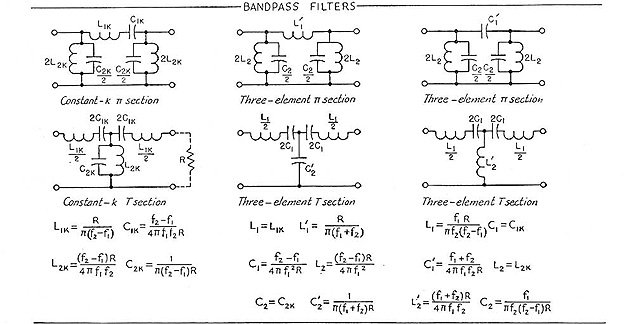
preselector_filter/doc/WTWH_Bandpass-Filters_Pt2_Fig1.png
