LieBtrau/MegawattKS_Radio_Design_101/rf-frontend/doc/118188519_731192181057607_6884754674382554886_n.jpg

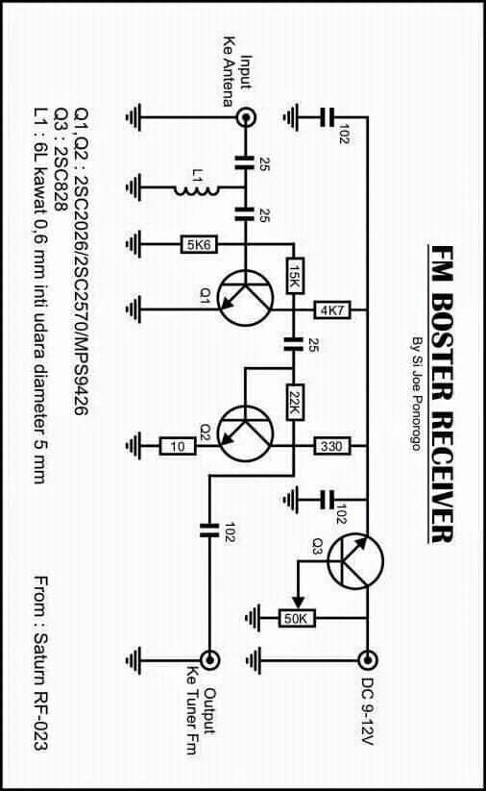
rf-frontend/doc/118188519_731192181057607_6884754674382554886_n.jpg
