LieBtrau/MegawattKS_Radio_Design_101/rf-frontend/doc/20241213111621770.png

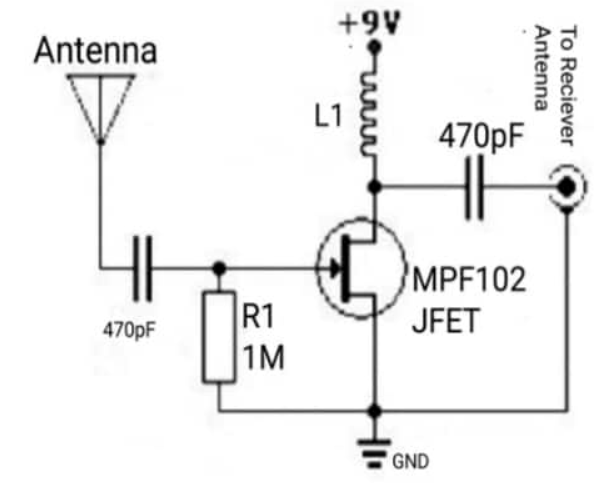
rf-frontend/doc/20241213111621770.png
