LieBtrau/MegawattKS_Radio_Design_101/VFO/doc/CB-colpitts_oscillator.png

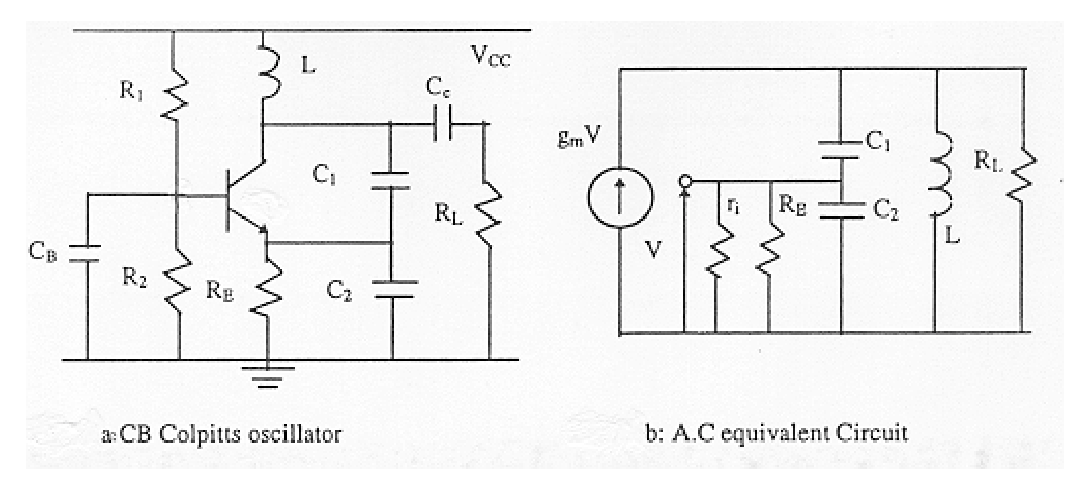
VFO/doc/CB-colpitts_oscillator.png
