LieBtrau/MegawattKS_Radio_Design_101/VFO/doc/circuit.png

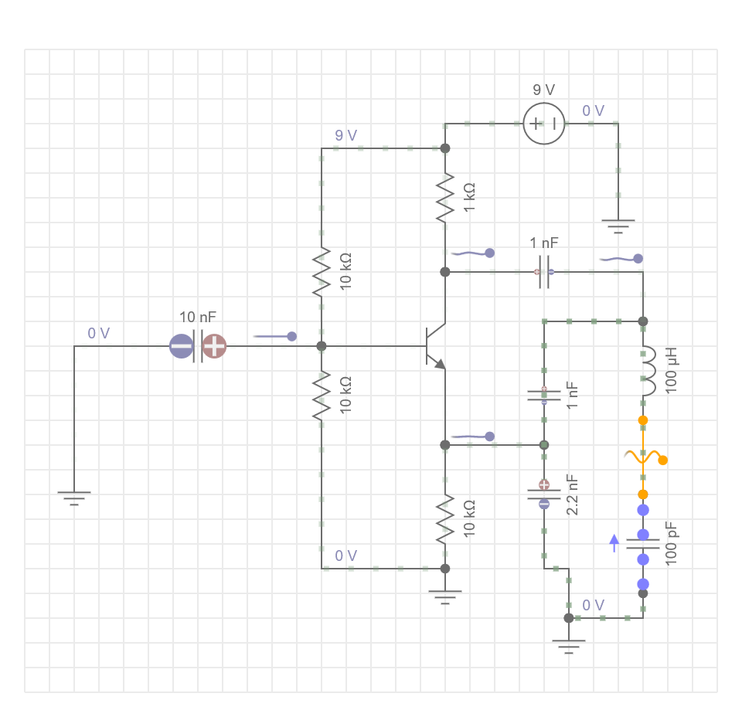
VFO/doc/circuit.png
