LieBtrau/MegawattKS_Radio_Design_101/VFO/doc/Clapp_88MHz-108MHz_from_EDABoard.jpg

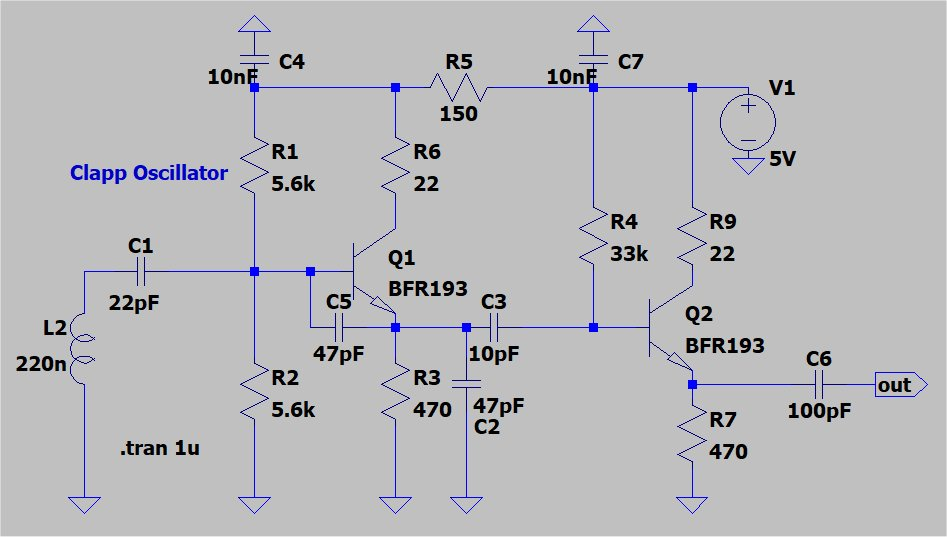
VFO/doc/Clapp_88MHz-108MHz_from_EDABoard.jpg
