LieBtrau/MegawattKS_Radio_Design_101/VFO/doc/EMRFD_fig.4.11.png

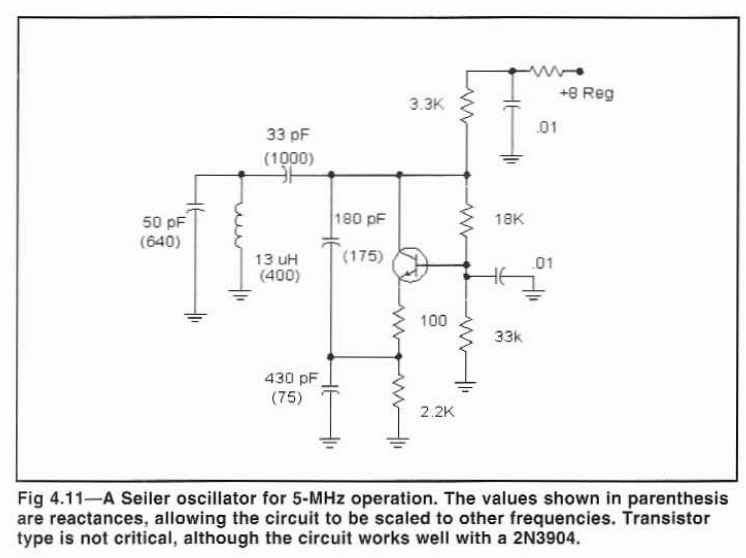
VFO/doc/EMRFD_fig.4.11.png
