LieBtrau/MegawattKS_Radio_Design_101/VFO/doc/OSFM963.jpg

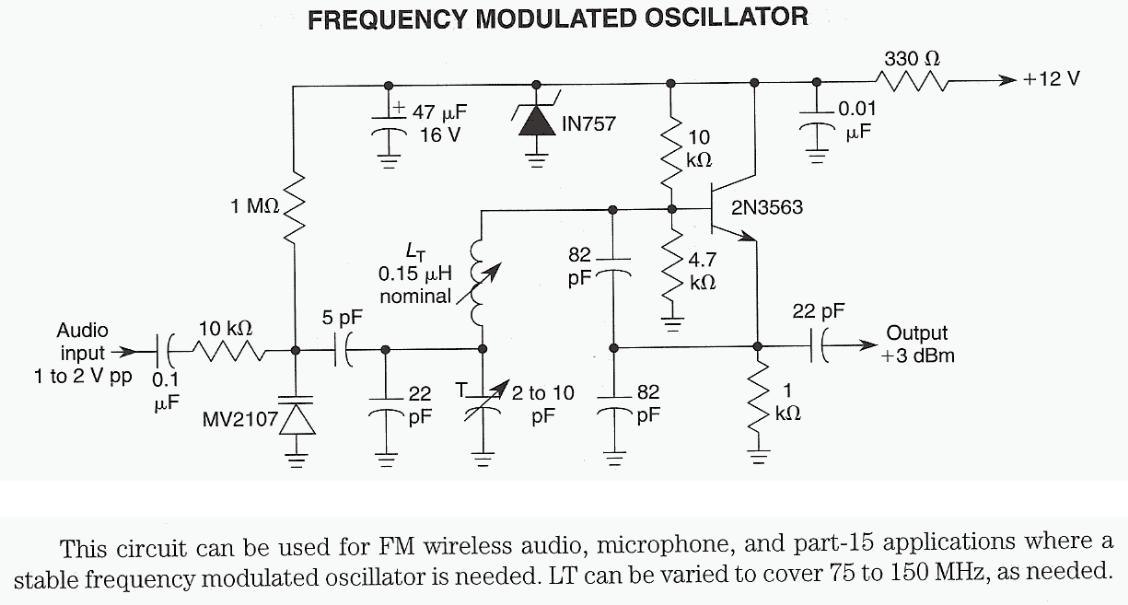
VFO/doc/OSFM963.jpg
