LieBtrau/MegawattKS_Radio_Design_101/VFO/doc/SSDRA_p34.png

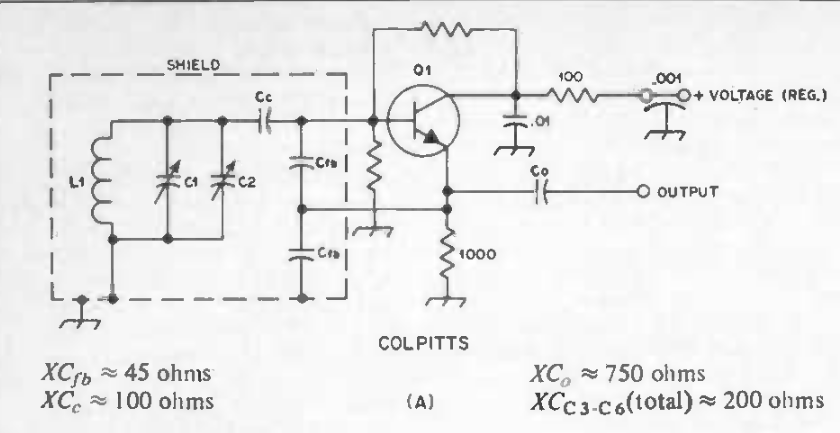
VFO/doc/SSDRA_p34.png
