LieBtrau/MegawattKS_Radio_Design_101/VFO/vackar/doc/vackar-circuit.jpg

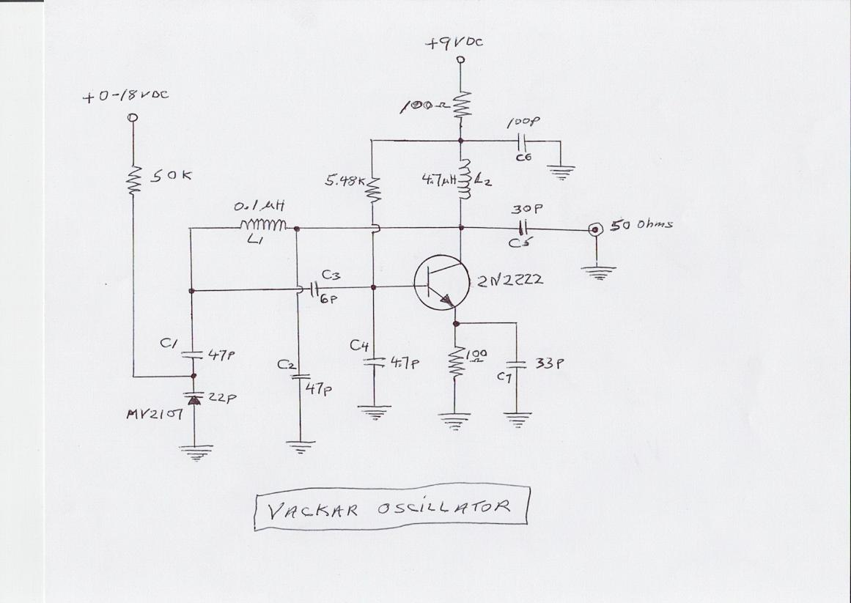
VFO/vackar/doc/vackar-circuit.jpg
