LieBtrau/MegawattKS_Radio_Design_101/doc/vintage_radio/Alain/4 Band Radio Recorder TC414/d_loewe_tc414_s6_nf_print.pdf

# radiomuseum.org: 4 Band Radio Recorder TC414 Art.-Nr. 58200

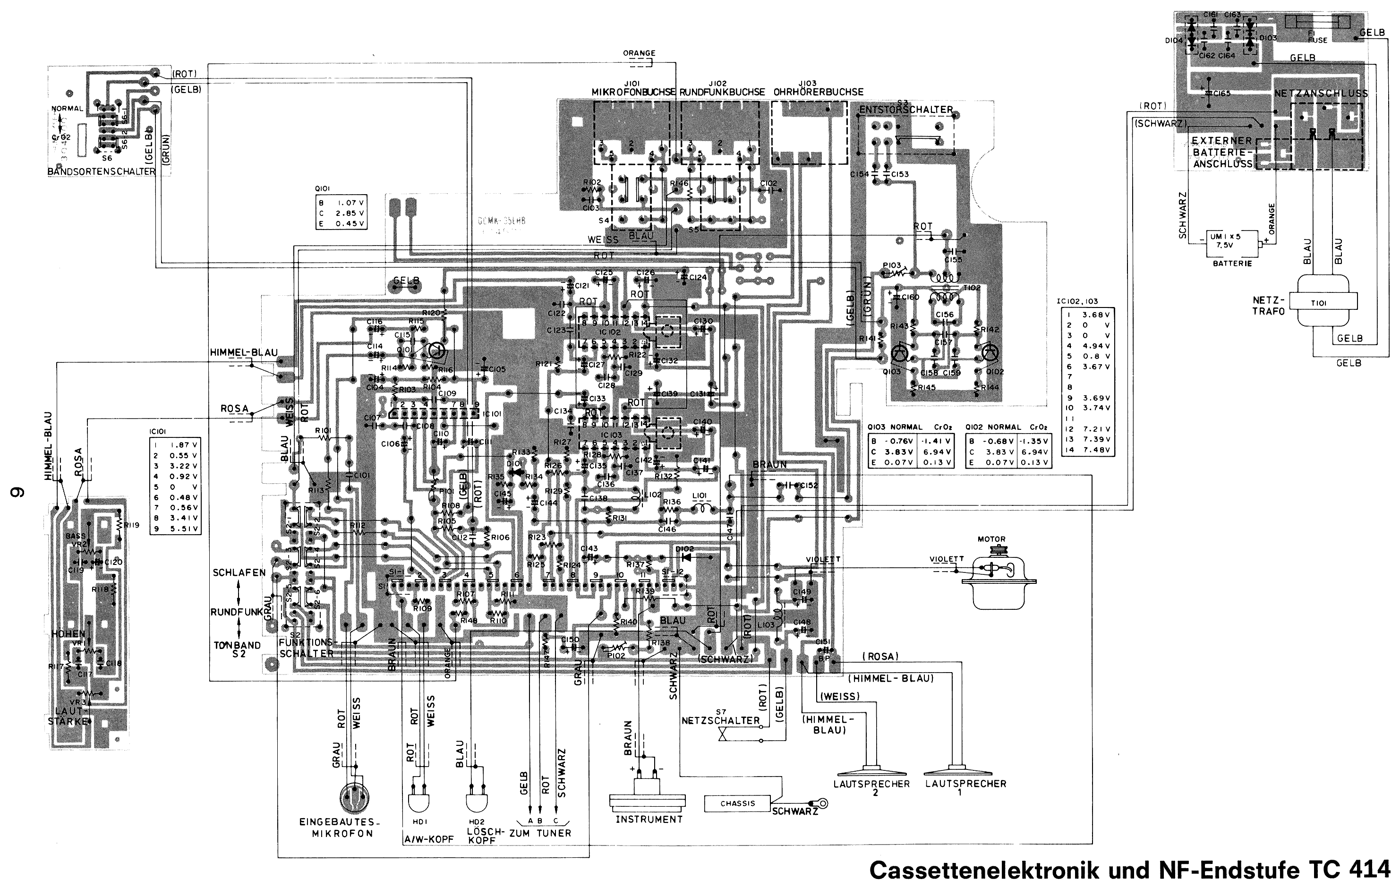
[picture p247: page 1]

www.radiomuseum.org; upload by Heiko zur Mühlen; download by Alain Busschaert Tue Sep 10 06:25:30 UTC 2024 [2964 x 1880, 468kb, ? DPI]
