LieBtrau/MegawattKS_Radio_Design_101/IF1_mixer/measurement/FULLSETUP.bmp

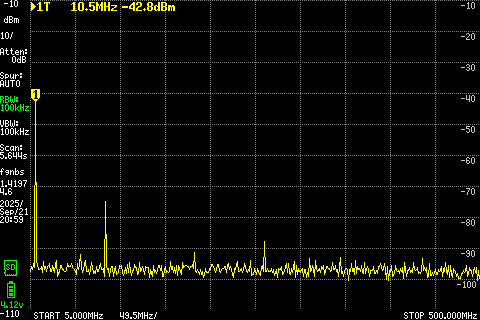
IF1_mixer/measurement/FULLSETUP.bmp
