LieBtrau/MegawattKS_Radio_Design_101/IF1_mixer/measurement/ade1_lo_only.bmp

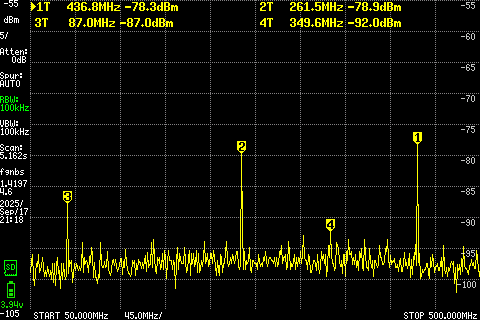
IF1_mixer/measurement/ade1_lo_only.bmp
