LieBtrau/MegawattKS_Radio_Design_101/IF1_mixer/measurement/ade1_withRF.bmp

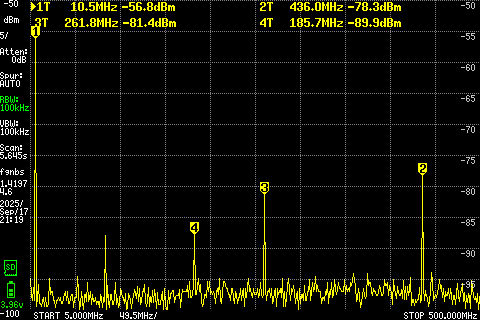
IF1_mixer/measurement/ade1_withRF.bmp
