LieBtrau/MegawattKS_Radio_Design_101/IF1_mixer/measurement/custom_mixer_lo_only.bmp

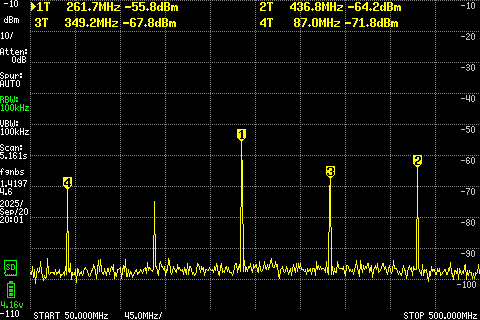
IF1_mixer/measurement/custom_mixer_lo_only.bmp
