LieBtrau/MegawattKS_Radio_Design_101/IF1_mixer/measurement/custom_mixer_WITH_RF.bmp

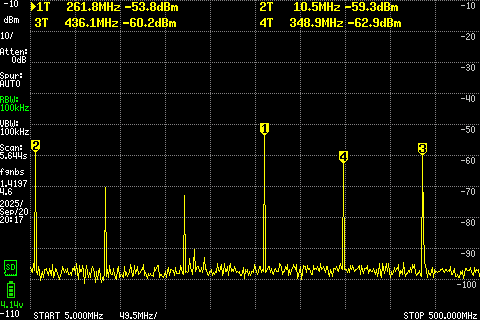
IF1_mixer/measurement/custom_mixer_WITH_RF.bmp
