LieBtrau/MegawattKS_Radio_Design_101/VFO/measurements/1VF0UT.bmp

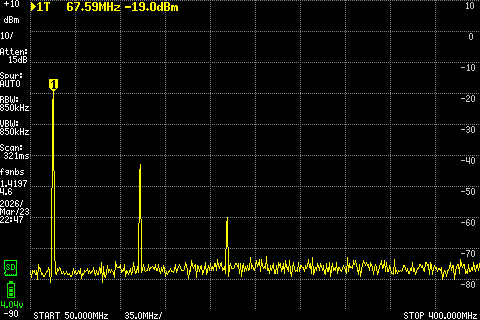
VFO/measurements/1VF0UT.bmp
