LieBtrau/MegawattKS_Radio_Design_101/VFO/measurements/75M.bmp

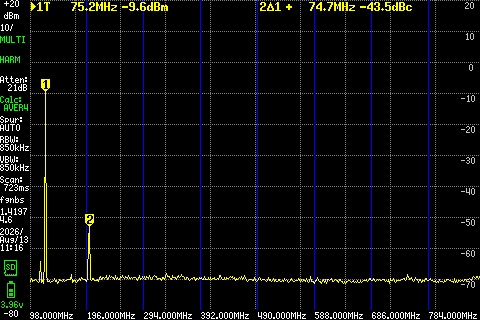
VFO/measurements/75M.bmp
