LieBtrau/MegawattKS_Radio_Design_101/VFO/measurements/98M.bmp

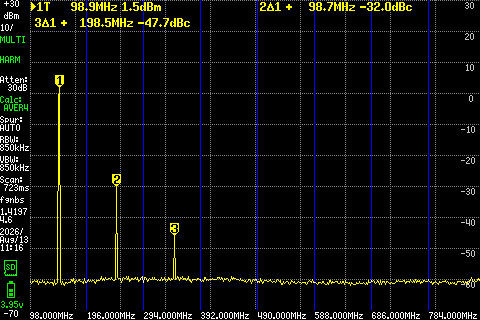
VFO/measurements/98M.bmp
