LieBtrau/MegawattKS_Radio_Design_101/VFO/measurements/F_OUT_F_TUNE_1V.png

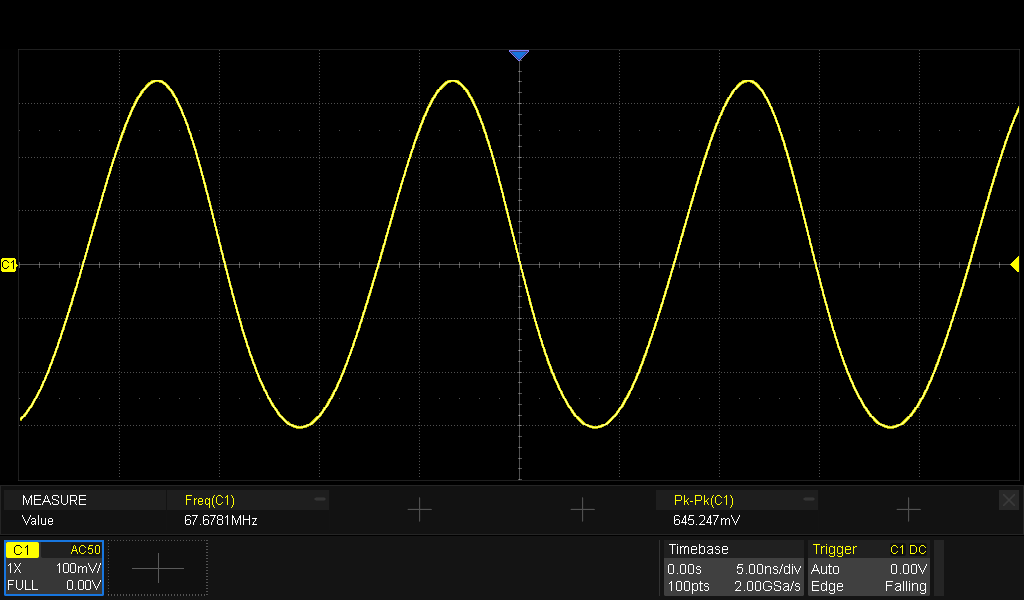
VFO/measurements/F_OUT_F_TUNE_1V.png
