LieBtrau/MegawattKS_Radio_Design_101/VFO/measurements/R15_0E_FTUNE_4V.png

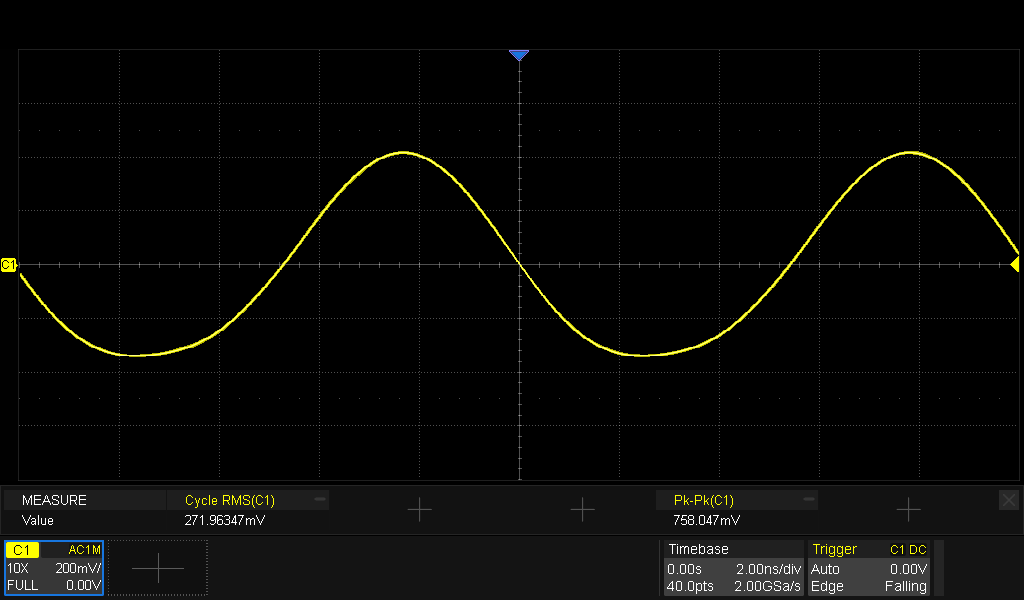
VFO/measurements/R15_0E_FTUNE_4V.png
