LieBtrau/MegawattKS_Radio_Design_101/VFO/measurements/Seiler_Ftune_4V_1mA_bias.png

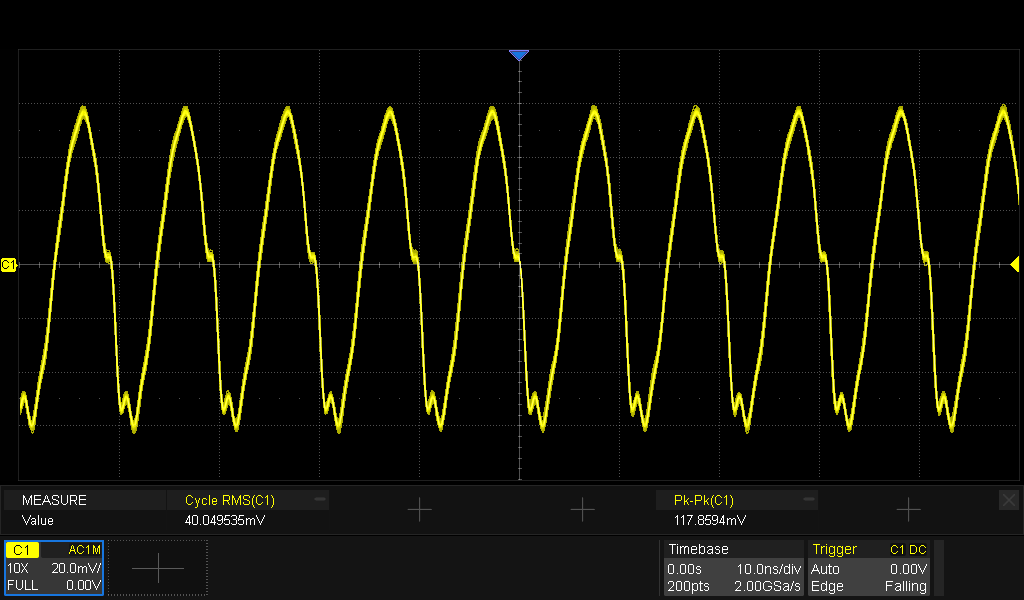
VFO/measurements/Seiler_Ftune_4V_1mA_bias.png
