LieBtrau/MegawattKS_Radio_Design_101/VFO/measurements/simulation_extra_10nH.png

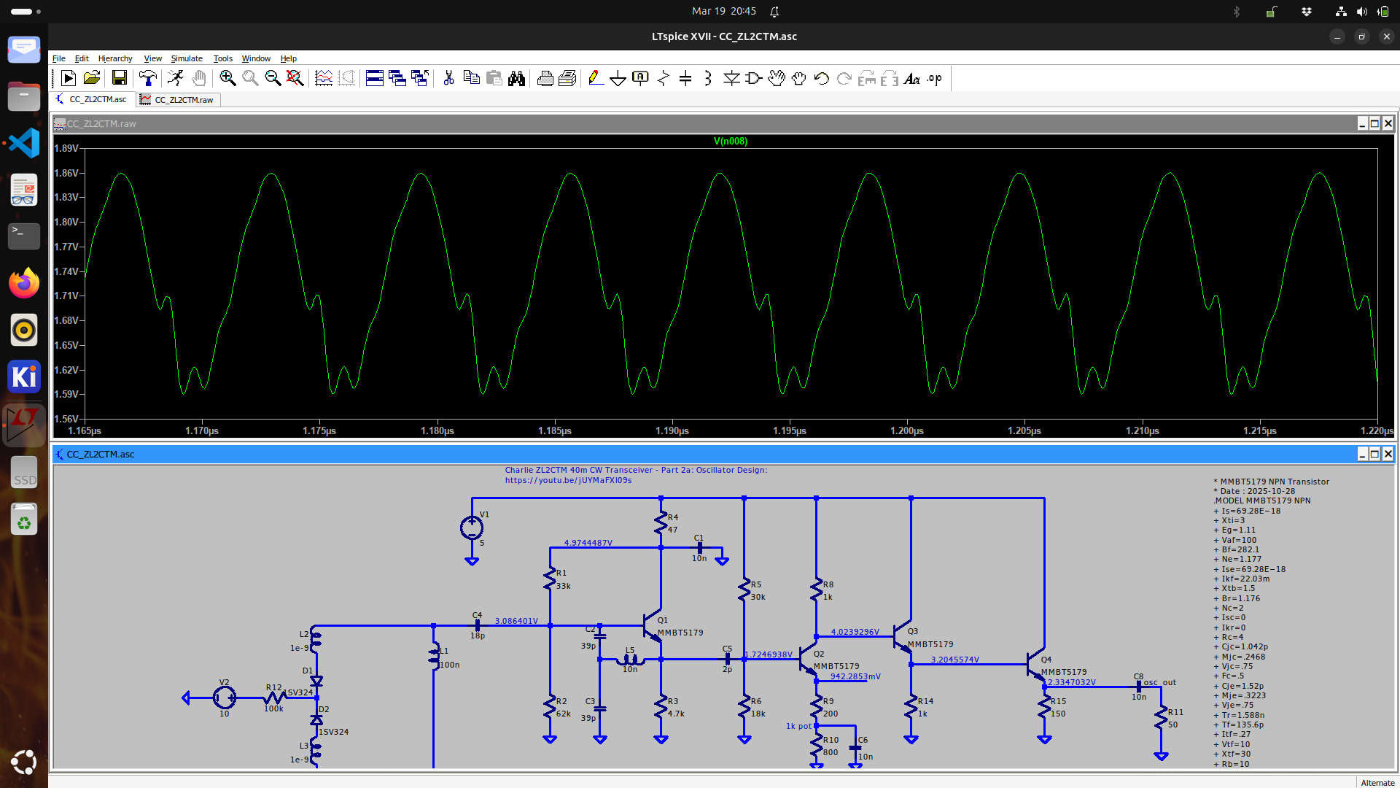
VFO/measurements/simulation_extra_10nH.png
