LieBtrau/MegawattKS_Radio_Design_101/doc/kvdijken.pdf

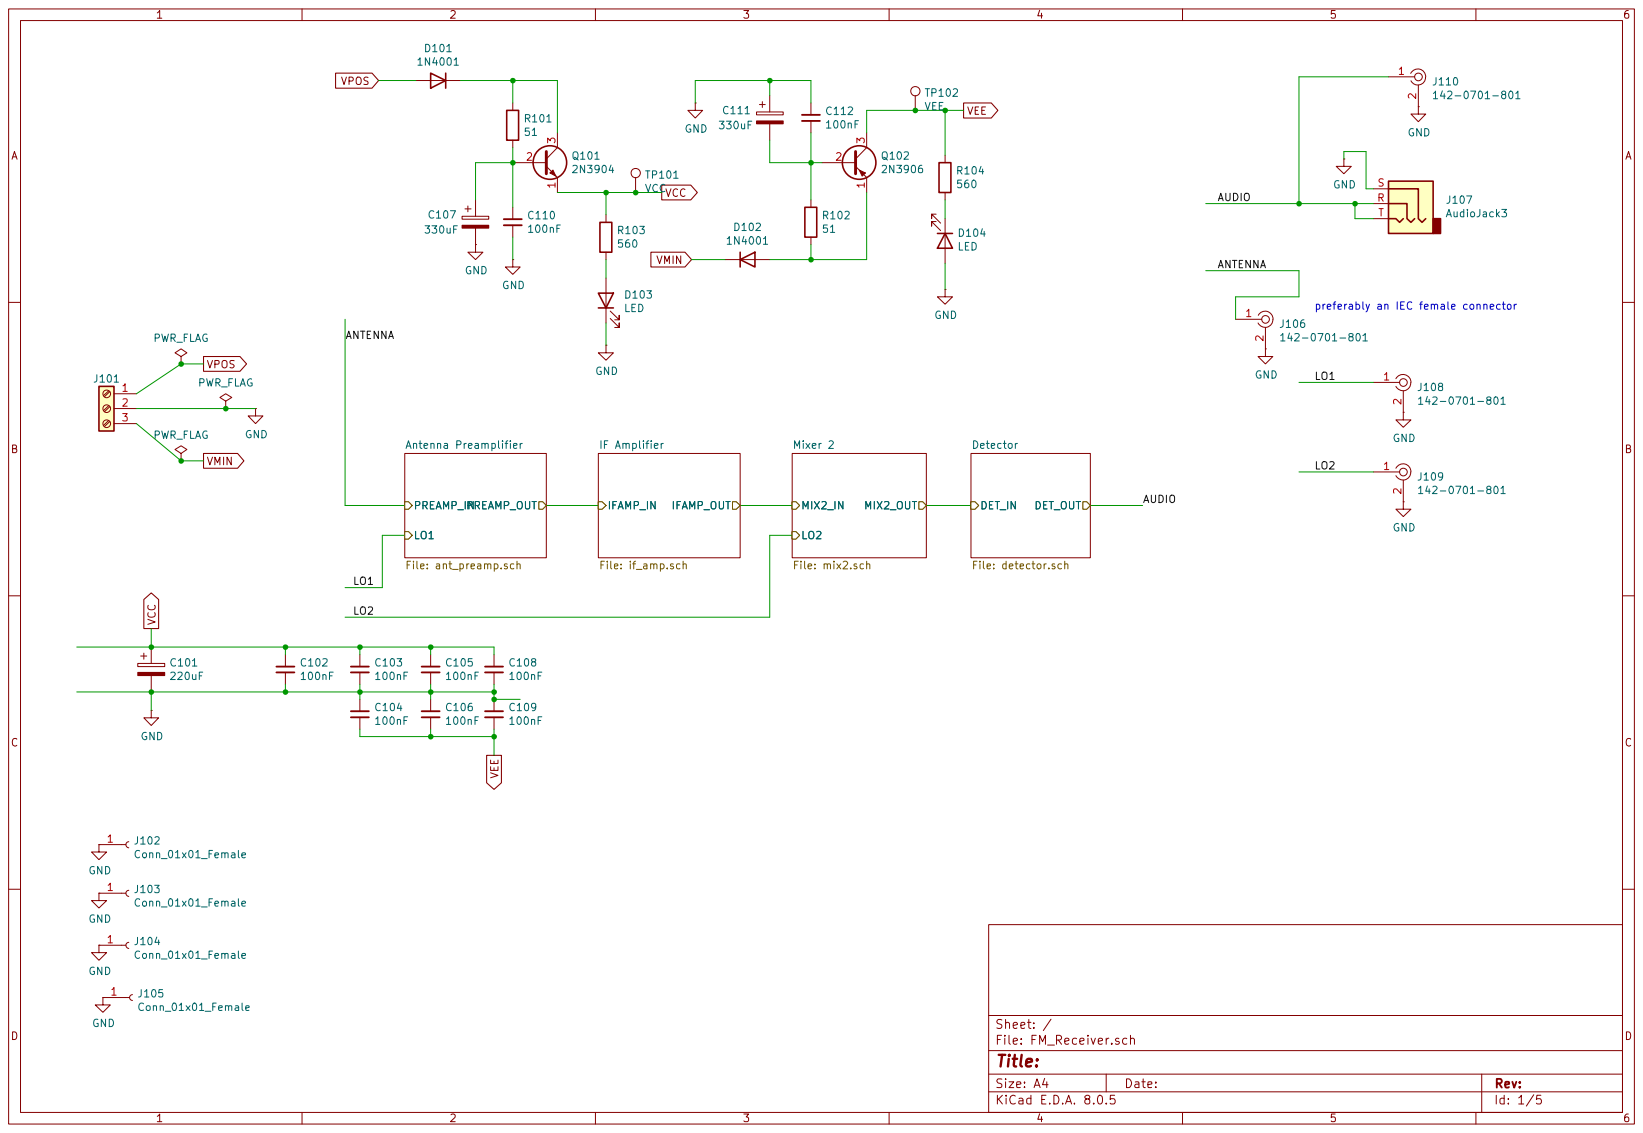
[picture p270: page 1]

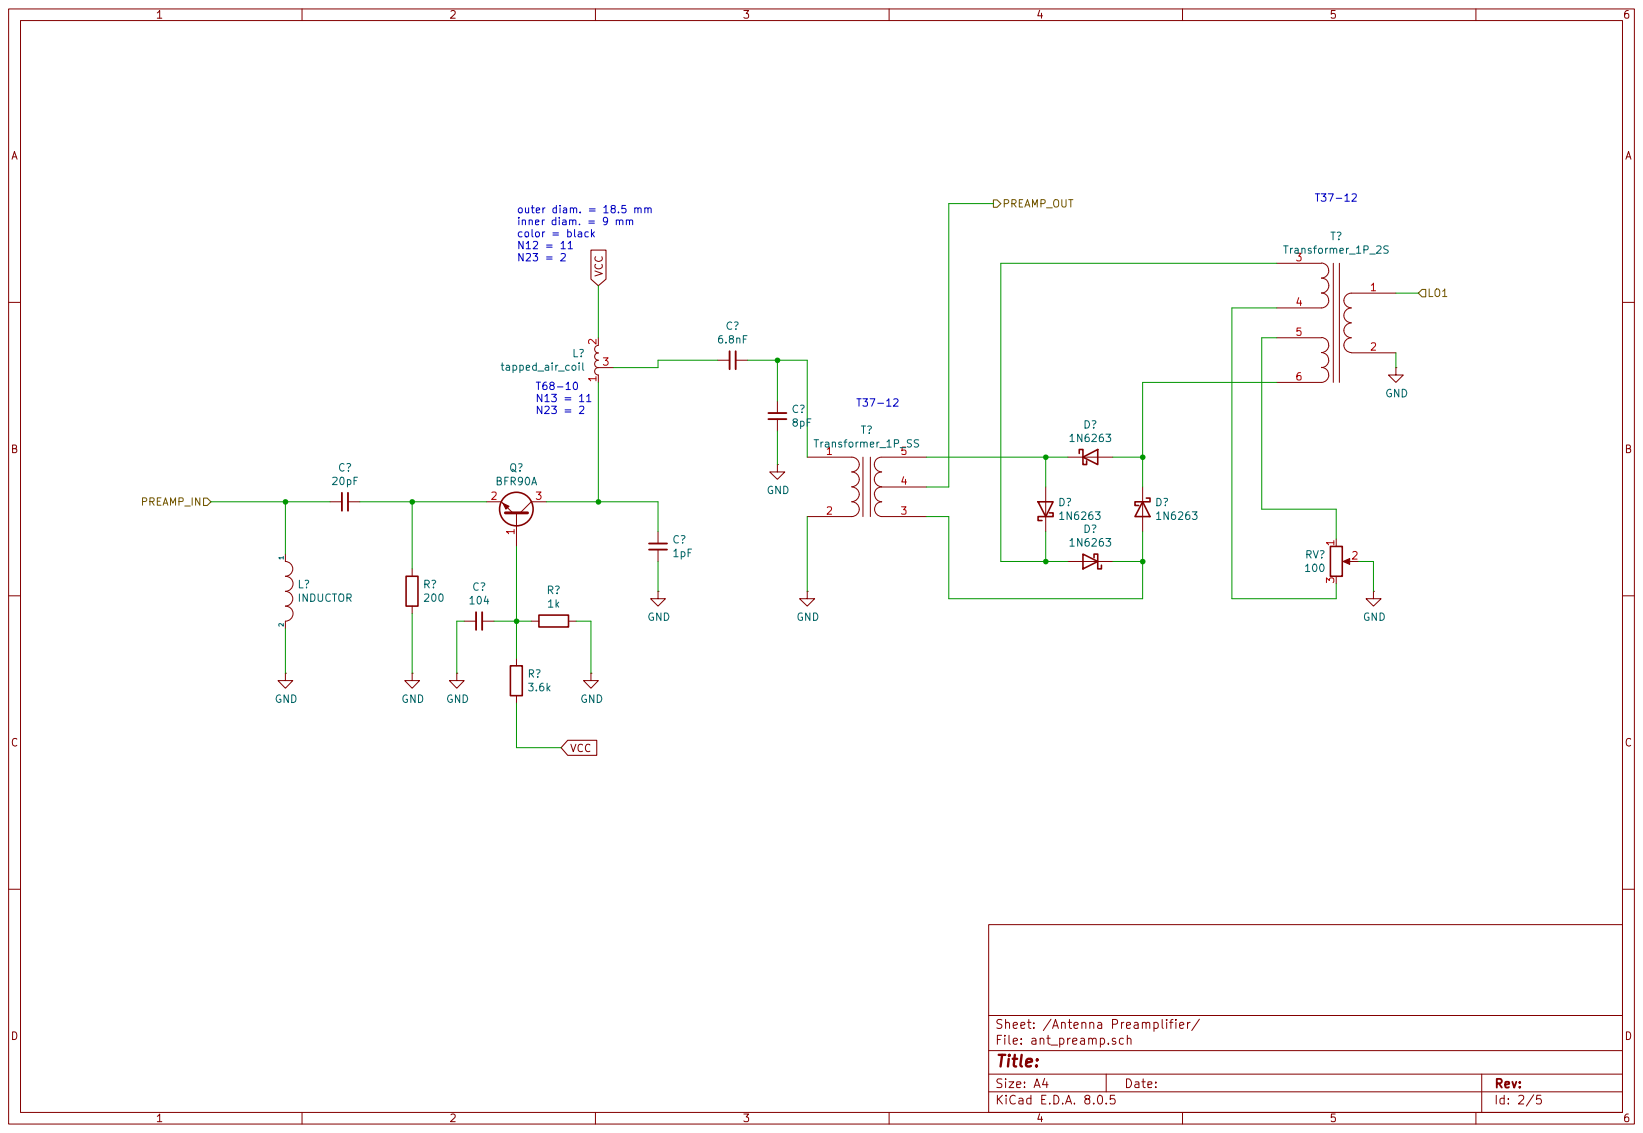
[picture p271: page 2]

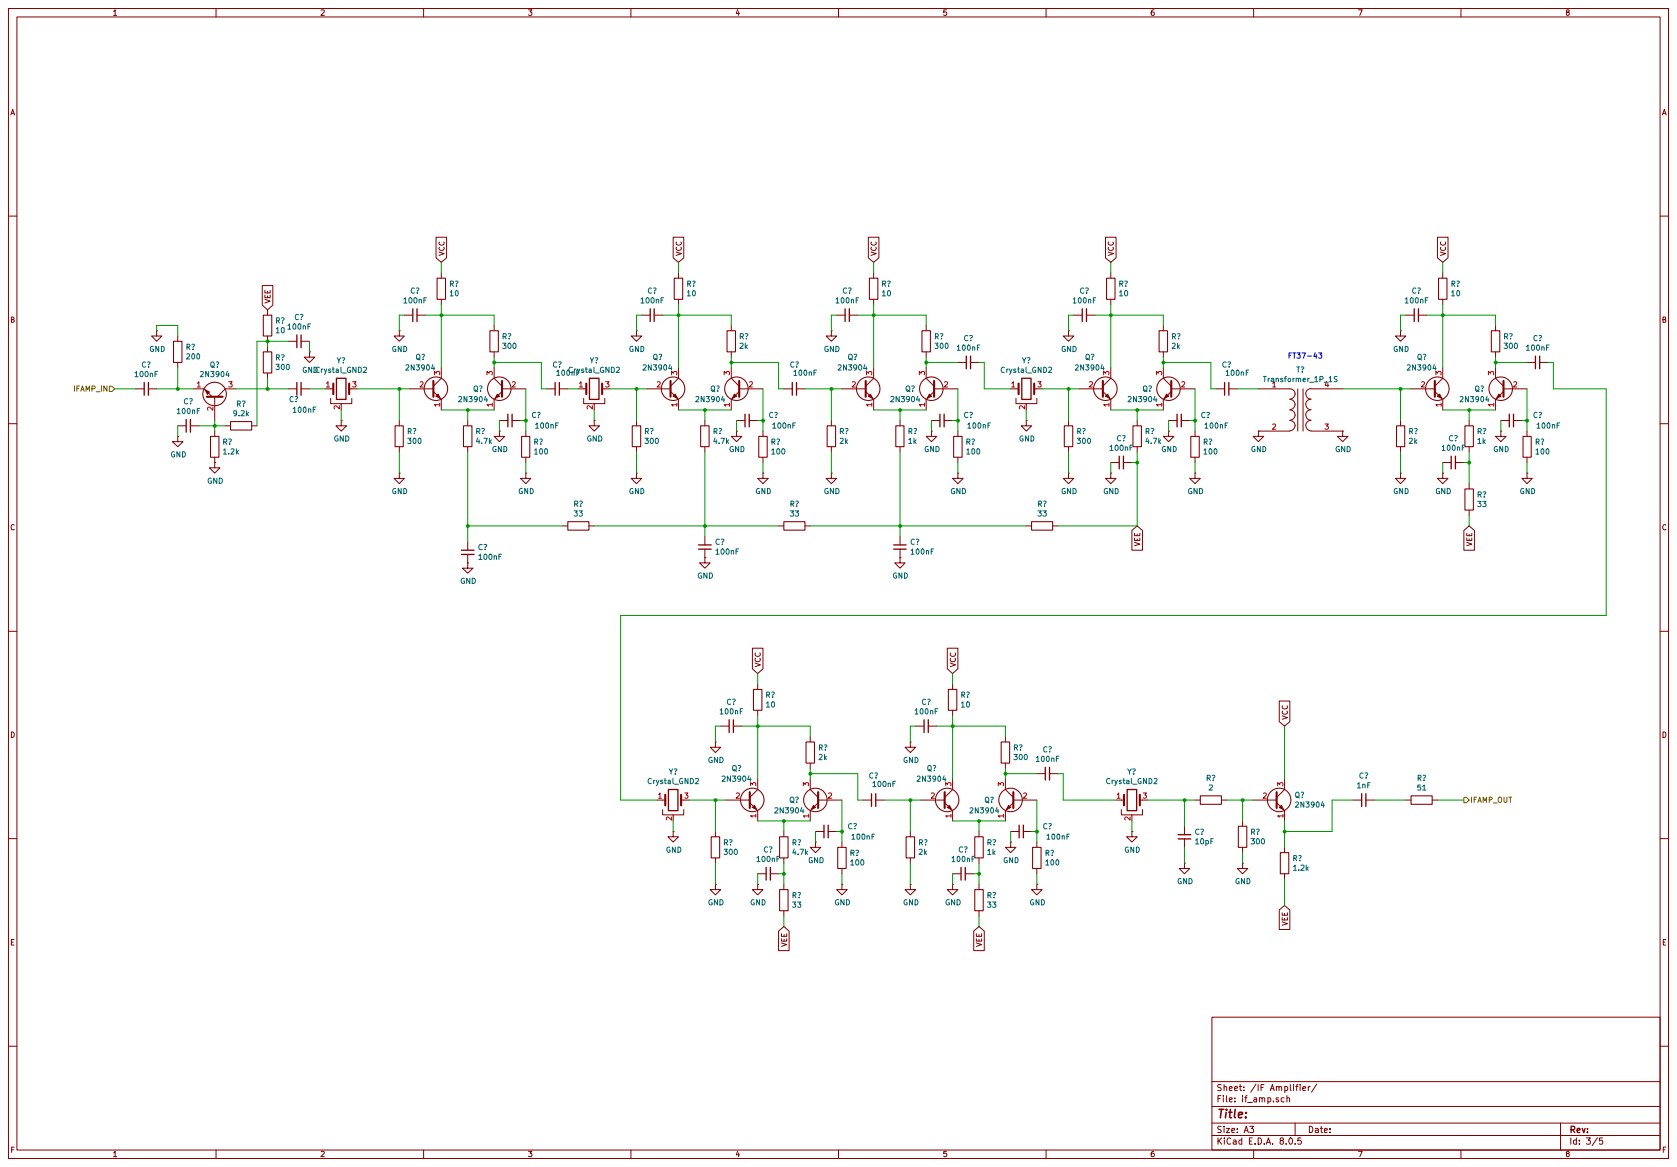
[picture p272: page 3]

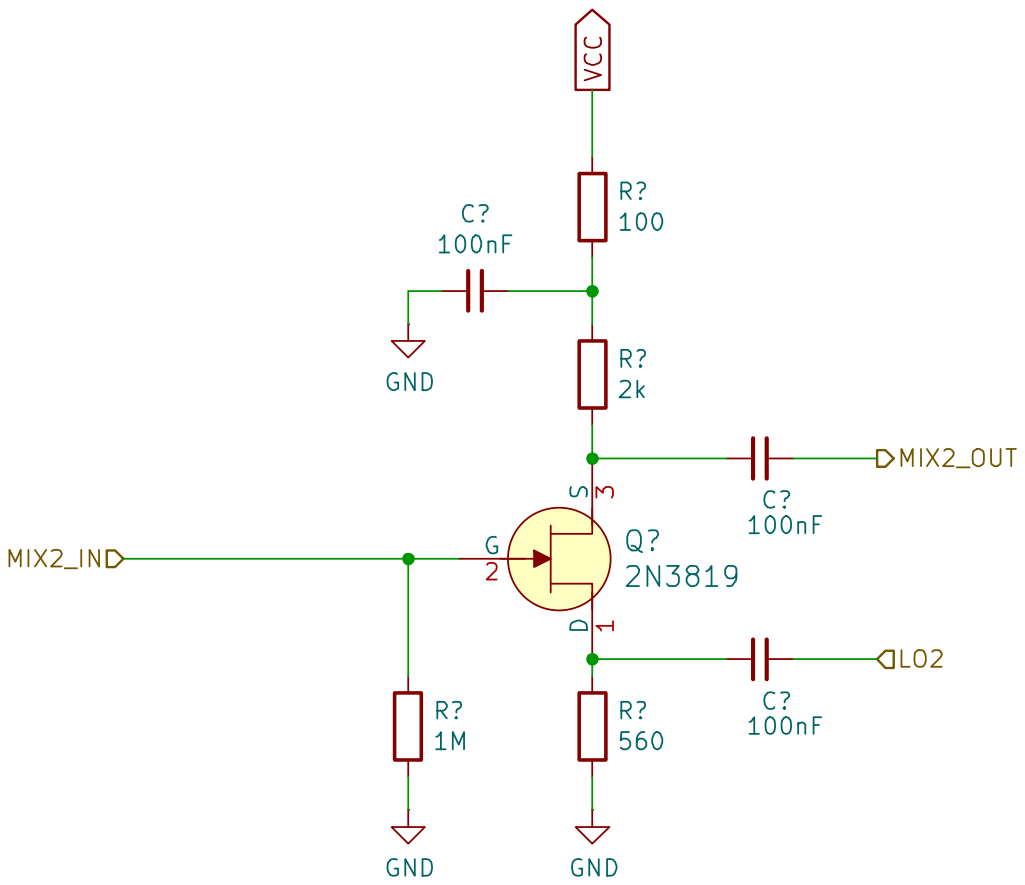
[picture p273: page 4]

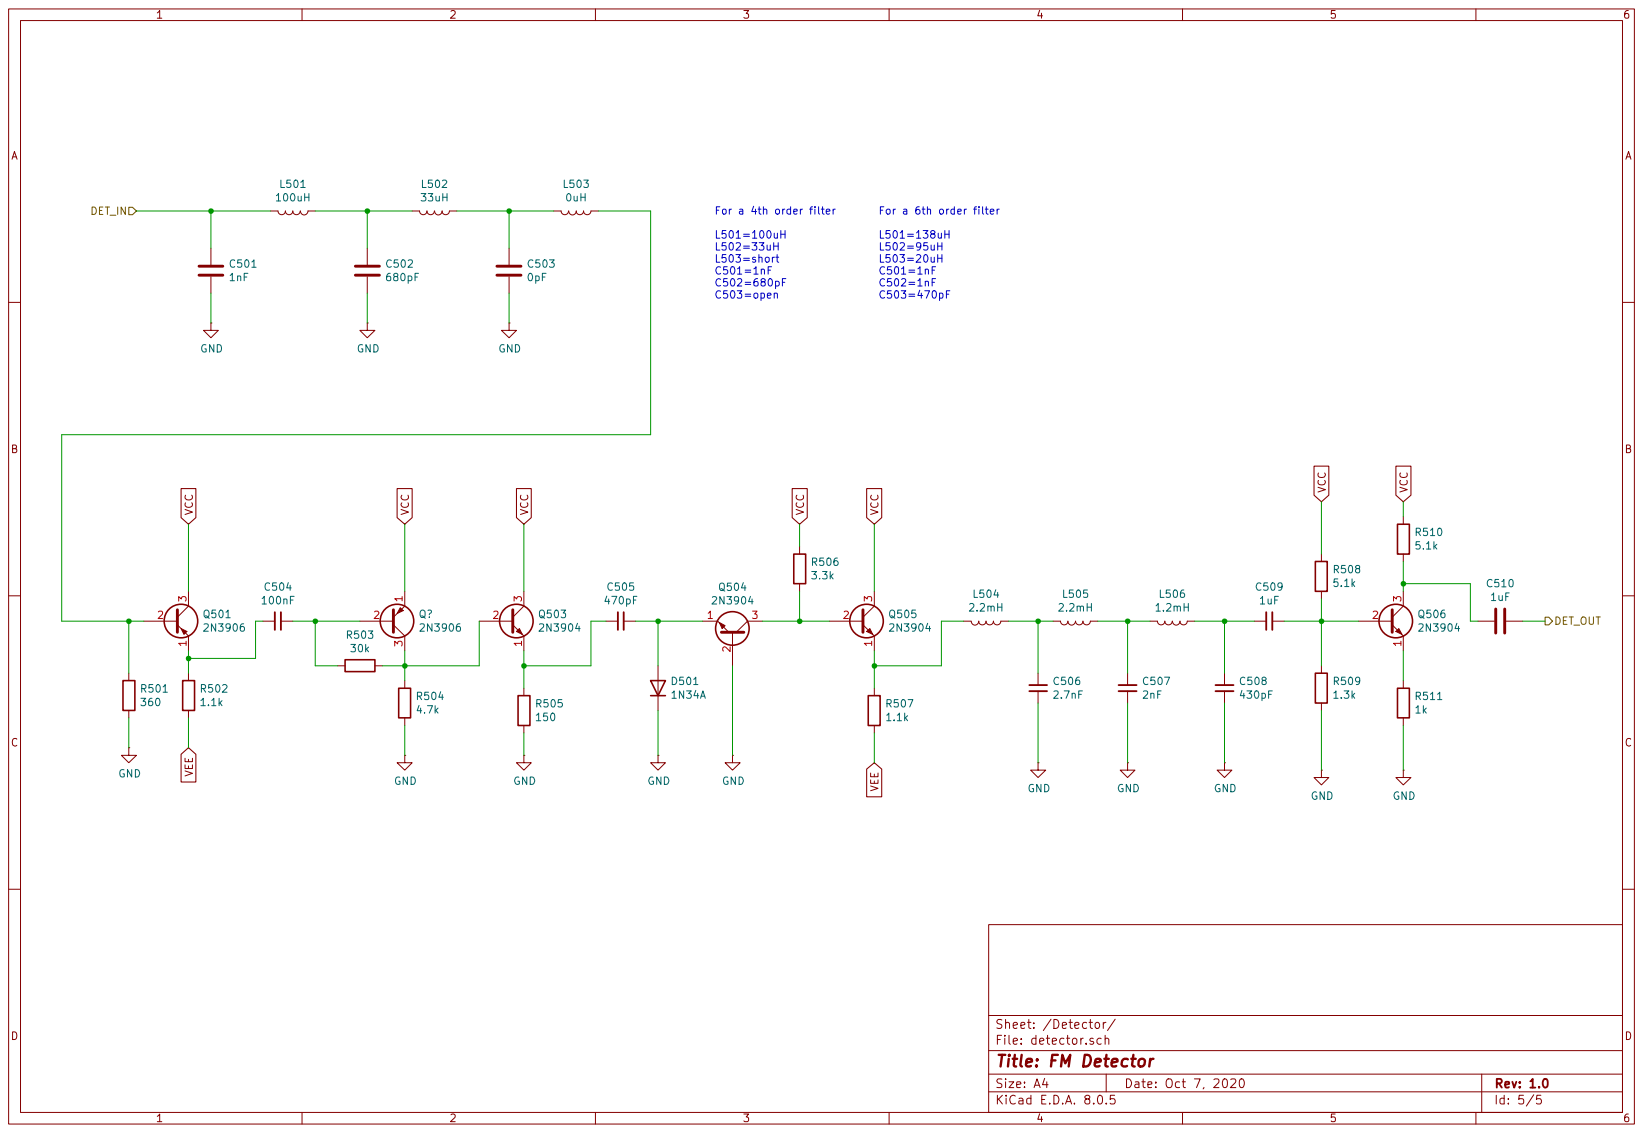
[picture p274: page 5]
