LieBtrau/MegawattKS_Radio_Design_101/IF1_amp/simulation/cascode_test.asc

C1: cap; 10n
C2: cap; 10n
C3: cap; 10n
C6: cap; 10n
Q1: npn; 2N3904
Q2: npn; 2N3904
R1: res; 2k
R2: res; 2.4k
R3: res; 100
R4: res; 19.6k
R5: res; 1k
R6: res; 10
Rout: res; 10k
V1: voltage; 12
V2: voltage; SINE(0 10u 10.7e6); AC 1; Rser=50
Named nets: 0, BQ2, CQ1, BQ1, out
.net I(Rout) V2
.tran 10u
Zin should match output impedance of the filter (or add an impedance matching network)
