LieBtrau/MegawattKS_Radio_Design_101/VFO/vackar/simulation/design1.asc

C1: cap; 120p
C2: cap; 6p
C3: cap; 30p
C4: cap; 33p; Rpar=1meg
C5: cap; 100n
J1: njf; J309
L1: ind; 4.7µ; Rser=1m
L2: ind; 150n; Rser=0.1
R1: res; 4.7k
R2: res; 10k
V1: voltage; 5
Named nets: 0, osc_out
.tran 0 60u 50u 1n
 
.param first_edge 200 ; 200th edge
.param last_edge 700 ; 700th edge
.param zero_crossing_voltage 0 ; voltage at zero crossing
.meas tran T1 find time when V(osc_out)={zero_crossing_voltage} rise {first_edge}
.meas tran T2 find time when V(osc_out)={zero_crossing_voltage} rise {last_edge}
.meas tran Frequency param ({last_edge}-{first_edge})/(T2-T1)
.options numdgt=7
.options plotwinsize=0
For varicap tuning, voltage over C1 must be reduced.  That can be can by playing with
values of C1 and C4, which are actually in series.  Decreasing C1 and raising C4
will reduce voltage over C4.  Don't overdo it because it will decrease spectral purity.
