LieBtrau/MegawattKS_Radio_Design_101/VFO/vackar/simulation/design2.asc

C1: cap; 120p
C2: cap; 10p
C3: cap; 47p
C4: cap; 100p
C5: cap; 100n
C6: cap; 10p
J1: njf; J309
L1: ind; 4.7µ; Rser=10
L2: ind; 150n; Rser=0.2
R1: res; 4.7k
R2: res; 10k
R3: res; 50k
V1: voltage; 5
V2: voltage; 5
Named nets: 0, osc_out
.tran 0 100u 50u 1n
 
.param first_edge 200 ; 200th edge
.param last_edge 700 ; 700th edge
.param zero_crossing_voltage 0 ; voltage at zero crossing
.meas tran T1 find time when V(osc_out)={zero_crossing_voltage} rise {first_edge}
.meas tran T2 find time when V(osc_out)={zero_crossing_voltage} rise {last_edge}
.meas tran Frequency param ({last_edge}-{first_edge})/(T2-T1)
.options numdgt=7
.options plotwinsize=0
.model 1SV324 D(Is=2.593E-15 Rs=0.4 N=1.024 BV=10 Ibv=1.00E-04 Cjo=7.672E-11 Vj=100 M=49.19)
Voltage over varicaps must be limited, so that means that they should be quite large
in comparison to the capacitors in series.
Unfortunately, in a series capacitor network, the largest capacitor doesn't have a lot 
of influence on the frequency.
