LieBtrau/MegawattKS_Radio_Design_101/VFO/vackar/simulation/design3.asc

C1: cap; 120p
C2: cap; 10p
C3: cap; 56p
C4: cap; 10p; Rpar=1meg
C5: cap; 100n
C6: cap; 10n
J1: njf; J309
L1: ind; 4.7µ; Rser=1m
L2: ind2; 150n; Rser=0.1
R1: res; 4.7k
R2: res; 10k
R3: res; 100
V1: voltage; 5
Named nets: 0, osc_out
.tran 0 60u 50u 1n
 
.param first_edge 200 ; 200th edge
.param last_edge 700 ; 700th edge
.param zero_crossing_voltage 0 ; voltage at zero crossing
.meas tran T1 find time when V(osc_out)={zero_crossing_voltage} rise {first_edge}
.meas tran T2 find time when V(osc_out)={zero_crossing_voltage} rise {last_edge}
.meas tran Frequency param ({last_edge}-{first_edge})/(T2-T1)
.options numdgt=7
.options plotwinsize=0
VFO for broadcast FM when C4 = 15 pF to 33 pF
Disadvantage is that voltage over C4 is 33 Vpp.  This is not suitable for varicaps.
Capacitor in series with C4 is needed, to reduce voltage over C4.  The drawback is that
C4 will have to change a lot more to yield the equivalent 18 pF capacitance change.
Can be a ferrite bead.
