LieBtrau/MegawattKS_Radio_Design_101/audio_amplifier/simulation/protection/design2.asc

R1: res; 13K
R2: res; {Rthermistor}
R3: res; 1K
R4: res; 27k
U1: LM4041_N_ADJC1P233
V1: voltage; SINE(5 100m 50)
Named nets: VCC, 0, out
;op
.step param Rthermistor list 1.5K 10K
Thermistor is 1.5K at 85°C
Advantage of LM4041 is that thermistor can be ground referenced.
So only one trace is needed to connect it.
.tran 100m
The LM4041 functions as regulated current source.  This allows for cancelling out power 
supply fluctuations at the output.
Connect to a 3V power supply monitor (e.g. TLV803)
