LieBtrau/MegawattKS_Radio_Design_101/audio_amplifier/simulation/speaker/kits_and_parts.asc

C1: cap; 47µ
C2: cap; 1µ
C3: cap; 100µ
C4: cap; 47n
D1: diode; 1N4148
D2: diode; 1N4148
Q1: npn; 2N3904
Q2: pnp; 2N3906
Q3: pnp; 2N3906
Q4: npn; 2N3904
R1: res; 1.1
R2: res; 1.1
R3: res; 1k
R4: res; 100
R5: res; 56k
R6: res; 100k
R7: res; 47k
Rout: res; 8
V2: voltage; 12
Vin: voltage; SINE(0 10m 1k); AC 1; Rser=0
Named nets: 0, out
.param f=1e3
.four {f} 10 100 V(out)
.options numdgt=7
.options plotwinsize=0
.op
.inc BCP53T.txt
.inc BCP56T.txt
.tran 0 {120/f} {20/f} {1/(f*100)}
;.ac dec 1meg 10 100k
.net I(Rout) Vin
https://www.kitsandparts.com/audioamp_v2.php
7.5% THD at 35mW output
