LieBtrau/MegawattKS_Radio_Design_101/rf-frontend/simulation/jfet_buffer.asc

C1: cap; 10n
C2: cap; 10n
Cp: cap; 15p
J1: njf; J309
L1: ind; 4.7µ
Lmatch: ind; 120n
R1: res; 47
R2: res; 1k
R3: res; 50
Rtest: res; 50k
V1: voltage; 5
V2: voltage; ""; AC 1
Named nets: 0
.ac dec 1001 50meg 200meg
