LieBtrau/MegawattKS_Radio_Design_101/rf-frontend/simulation/LC-matching.asc

C1: cap; 100p
C2: cap; 128p
C3: cap; 100p
L1: ind; 45n
R1: res; 3
R2: res; 50
R3: res; 3
R4: res; 50
V1: voltage; ""; AC 1
Named nets: 0, OUT1, OUT2
.ac dec 1001 50meg 150meg
.net I(R1) V1
Antenna
Matching network
Antenna
No matching network
Matching network yields about 6dB of gain.
