LieBtrau/MegawattKS_Radio_Design_101/IF2_amp/simulation/Yates_2010.asc

C1: cap; 100n
C2: cap; 100n
C3: cap; 100n
C4: cap; 4.7n
C5: cap; 12n
C6: cap; 100n
C7: cap; 100n
C8: cap; 100n
C9: cap; 100n
C10: cap; 100n
C11: cap; 100n
C15: cap; 100n
C16: cap; {Cc}
C17: cap; {Cc}
C18: cap; {Cc}
L1: ind; mlf2012c180kt000_s
L3: ind; mlf2012c180kt000_s
Q1: npn; 2N3904
Q2: npn; 2N3904
Q3: npn; 2N3904
Q5: npn; 2N3904
R1: res; 1Meg
R2: res; {Rc}
R3: res; 100
R4: res; 1Meg
R5: res; 3.6k
R6: res; 1.5k
R7: res; 1Meg
R8: res; {Rc}
R9: res; 100
R10: res; {Rc}
R11: res; 1.2k
R12: res; 100
R13: res; 51
Rout: res; 50
V1: voltage; 5
Vin: voltage; SINE(0 1µV 200e3); AC 1; Rser=50
Named nets: 0, out
.ac dec 1meg 10k 100meg
.tran 0 2m 1.95m
.net I(Rout) Vin
.param Rc=3.9k
.step param Cc list 1p 100p 150p
.inc mlf2012c180kt000_s.mod
200kHz center frequency, 200kHz bandwidth
100dB gain
Zin = 50ohm
