LieBtrau/MegawattKS_Radio_Design_101/audio_filter/simulations/filter2.asc

C1: cap; 390p
C2: cap; 390p
C3: cap; 100n
Q1: npn; 2N3904
R1: res; 39k
R2: res; 10k
R3: res; 10k
R4: res; 10k
R5: res; 150k
V1: voltage; 0; AC 1
V2: voltage; 5
Named nets: 0
;op
.ac dec 1000 100 1meg
Calculator : http://sim.okawa-denshi.jp/en/OPstool.php
Stopband limitation
https://ez.analog.com/cfs-filesystemfile/__key/communityserver-wikis-components-files/00-00-00-06-97/KWIK_5F00_FAQ-_2D00_-Design-of-an-anti_2D00_aliasing-Sallen_2D00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
