LieBtrau/MegawattKS_Radio_Design_101/rf-frontend/simulation/jfet.asc

C1: cap; 10p
C2: cap; 10n
C3: cap; 10n
C4: cap; 10n
C_Whip1: cap; 12p
J1: njf; J309
J2: njf; J309
L1: ind; 250n
L2: ind; 400n
R2: res; 2k
R3: res; 50
R4: res; 100k
R5: res; 220k
V1: voltage; 0; AC 1; Rser=5k
V2: voltage; 10
Named nets: 0, out
.ac dec 101 50meg 500meg
15dB gain with respect to setup without amp in which C2 is connected to 50 ohm load.
One might wonder if a preamp is really needed.  Is the problem sensitivity
or is it selectivity?
