LieBtrau/MegawattKS_Radio_Design_101/IF1_mixer/simulation/eth_trafo.asc

C1: cap; 100n
D1: schottky; 1N5819
D2: schottky; 1N5819
D3: schottky; 1N5819
D4: schottky; 1N5819
L1: ind2; 33µ
L2: ind2; 33µ
L3: ind2; 33µ
L4: ind2; 33µ
L5: ind2; 33µ
L6: ind2; 33µ
LO1: voltage; PULSE(0 1 0 1n 1n {1/(2*f)} {1/f}); Rser=50
R1: res; 50
R2: res; 50
RF1: voltage; SINE(0 1e-3 10e6)
Named nets: 0, IF1
K1 L1 L2 L3 1
K2 L4 L5 L6 1
.param f=8.8e6
.tran 0 500u 490u
Suitable for asymmetric drive.  Will work with SI5351.
Diodes unsuitable for RF
