LieBtrau/MegawattKS_Radio_Design_101/IF1_mixer/simulation/eth_trafo2.asc

D5: diode; DI_SMS3923
D6: diode; DI_SMS3923
D7: diode; DI_SMS3923
D8: diode; DI_SMS3923
L7: WE-CNSW
L8: WE-CNSW
LO2: voltage; PULSE({-amp} {amp} 0 1n 1n {1/(2*f)} {1/f}); Rser=50
R2: res; 50
RF2: voltage; SINE(0 1e-3 108e6); Rser=50
U1: ALT4532M_201_T001_s
U2: ALT4532M_201_T001_s
U3: ALT4532M_201_T001_s
Named nets: 0, RF, OUT
.param f=98e6
.param amp=0.7
.inc BAV99.spice.txt
.inc 1N5711WS.spice.txt
.MODEL DI_SMS3923 D  ( IS=5e-9 RS=10 BV=46 IBV=1e-5
+ CJO=0.9p  M=0.24 N=1.05 TT=8e-11 )
.options numdgt=7
.options plotwinsize=0
.tran 0 20u 10u
