LieBtrau/MegawattKS_Radio_Design_101/IF1_mixer/simulation/eth_trafo4.asc

D1: diode; DI_SMS3923
D2: diode; DI_SMS3923
D3: diode; DI_SMS3923
D4: diode; DI_SMS3923
D5: diode; DI_SMS3923
D6: diode; DI_SMS3923
D7: diode; DI_SMS3923
D8: diode; DI_SMS3923
L1: WE-CNSW
L2: WE-CNSW
L3: WE-CNSW
L4: WE-CNSW
L5: ind2; 55µ; Rser=0.1
L6: ind2; 55µ; Rser=0.1
L7: ind2; 65µ; Rser=0.1
L8: ind2; 65µ; Rser=0.1
L9: ind2; 55µ; Rser=.1
L10: ind2; 55µ; Rser=0.1
L11: ind2; 55µ; Rser=0.1
L12: ind2; 55µ; Rser=0.1
LO1: voltage; PULSE({-amp} {amp} 0 1n 1n {1/(2*f)} {1/f}); Rser=50
LO2: voltage; PULSE({-amp} {amp} 0 1n 1n {1/(2*f)} {1/f}); Rser=50
R1: res; 50
R2: res; 50
R3: res; 0.001
RF1: voltage; SINE(0 1e-3 108e6); Rser=50
RF2: voltage; SINE(0 1e-3 108e6); Rser=50
Named nets: 0, RF, OUT, OUT2
.param f=98e6
.param amp=0.7
.inc BAV99.spice.txt
.inc 1N5711WS.spice.txt
.MODEL DI_SMS3923 D  ( IS=5e-9 RS=10 BV=46 IBV=1e-5
+ CJO=0.9p  M=0.24 N=1.05 TT=8e-11 )
.options numdgt=7
.options plotwinsize=0
.tran 0 20u 10u
K1 L5 L6 1
K2 L7 L8 1
K3 L9 L10 1
K4 L11 L12 1
