LieBtrau/MegawattKS_Radio_Design_101/IF2_amp/simulation/complicated_IF_amp.asc

C1: cap; 100n
C2: cap; 100n
C3: cap; 100n
C4: cap; 100n
C5: cap; 10n
C6: cap; 100n
C7: cap; 100n
C8: cap; 10n
C9: cap; 10n
Q1: npn; 2N3904
Q2: npn; 2N3904
R1: res; 3.6k
R2: res; 1.5k
R3: res; 51
R4: res; 120
R5: res; 10
R6: res; 3.6k
R7: res; 1.5k
R8: res; 300
R9: res; 22
R10: res; 120
R11: res; 22
R12: res; 22
Rout: res; 100k
V1: voltage; 5
Vin: voltage; SINE(0 55e-3 {f}); AC 1; Rser=50
Named nets: 0, B, F
.net I(Rout) Vin
.ac dec 1001 10k 100meg
;.op
;.tran 0 10e-6 0 1e-10
.param f=10.7e6
.options numdgt=7
.options plotwinsize=0
.four {f} V(out) 10 100
Final design
Complicated 200kHz amplifier.  Better to use the Yates 2010 design.
Only 26dB amplification
