LieBtrau/MegawattKS_Radio_Design_101/IF1_mixer/simulation/DBM_Diode_comparison.asc

D1: schottky; DI_1N5711WS
D2: schottky; DI_1N5711WS
D3: schottky; DI_1N5711WS
D4: schottky; DI_1N5711WS
D5: diode; DI_SMS3923
D6: diode; DI_SMS3923
D7: diode; DI_SMS3923
D8: diode; DI_SMS3923
L1: ind2; 33µ
L2: ind2; 33µ
L3: ind2; 33µ
L4: ind2; 33µ
L5: ind2; 33µ
L6: ind2; 33µ
L7: ind2; 33µ
L8: ind2; 33µ
L9: ind2; 33µ
L10: ind2; 33µ
L11: ind2; 33µ
L12: ind2; 33µ
LO1: voltage; PULSE(0 1 0 1n 1n {1/(2*f)} {1/f}); Rser=50
LO2: voltage; PULSE(0 0.65 0 1n 1n {1/(2*f)} {1/f}); Rser=50
R1: res; 50
R3: res; 50
RF1: voltage; SINE(0 1e-3 108e6); Rser=50
RF2: voltage; SINE(0 1e-3 108e6); Rser=50
Named nets: 0, IF_1N5711, IF_SMS3923
K1 L1 L2 L3 1
K2 L4 L5 L6 1
.param f=98e6
.inc BAV99.spice.txt
.inc 1N5711WS.spice.txt
.MODEL DI_SMS3923 D  ( IS=5e-9 RS=10 BV=46 IBV=1e-5
+ CJO=0.9p  M=0.24 N=1.05 TT=8e-11 )
.options numdgt=7
.options plotwinsize=0
.tran 0 12u 2u
Suitable for asymmetric drive.  Will work with SI5351.
K3 L7 L8 L9 1
K4 L10 L11 L12 1
