LieBtrau/MegawattKS_Radio_Design_101/IF1_mixer/simulation/eth_trafo3.asc

D5: diode; DI_SMS3923
D6: diode; DI_SMS3923
D7: diode; DI_SMS3923
D8: diode; DI_SMS3923
LO2: voltage; PULSE(0 1.4 0 1n 1n {1/(2*f)} {1/f}); Rser=50
R2: res; 50
RF2: voltage; SINE(0 1e-3 108e6); Rser=50
T1: WE-STST
T2: WE-STST
Named nets: 0, IF2
.param f=98e6
.inc BAV99.spice.txt
.inc 1N5711WS.spice.txt
.MODEL DI_SMS3923 D  ( IS=5e-9 RS=10 BV=46 IBV=1e-5
+ CJO=0.9p  M=0.24 N=1.05 TT=8e-11 )
;.options numdgt=7
.options plotwinsize=0
.tran 0 20u 10u
