LieBtrau/MegawattKS_Radio_Design_101/audio_filter/simulations/audio_filter.asc

C1: cap; 470n
C2: cap; 390p
C3: cap; 390p
C4: cap; 4.7µ
C6: cap; 10n
C7: cap; 390p
Q1: npn; 2N3904
R1: res; 470k
R2: res; 470k
R3: res; 15k
R4: res; 15k
R5: res; 15k
R6: res; 8.2k
R8: res; 2.2k
R9: res; 1k
V1: voltage; SINE(0 0.5 1k); AC 1
V2: voltage; 5
Named nets: 0, out
Circuit idea from Elektor EN1975070522:Active low pass filter
A Sallen-Key offers the same performance with a lot less components.
.op
;.tran 2m
.ac dec 1meg 1 1meg
.param f=100e3
R6, C6 = FM de-emphasis
