LieBtrau/MegawattKS_Radio_Design_101/audio_filter/simulations/filter3.asc

C1: cap; 1.5n
C2: cap; 820p
C3: cap; 100n
J1: njf; SST309
R1: res; 100k
R2: res; 16k
R3: res; 3.3k
R4: res; 10k
V1: voltage; 0; AC 1
V2: voltage; 5
Named nets: 0
;op
.ac dec 1000 100 1meg
Calculator : http://sim.okawa-denshi.jp/en/OPstool.php
Stopband limitation
https://ez.analog.com/cfs-filesystemfile/__key/communityserver-wikis-components-files/00-00-00-06-97/KWIK_5F00_FAQ-_2D00_-Design-of-an-anti_2D00_aliasing-Sallen_2D00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
The BJT version performs better.
