LieBtrau/MegawattKS_Radio_Design_101/IF1_mixer/simulation/DDBM2.asc

D1: schottky; 1N5711
D2: schottky; 1N5711
D3: schottky; 1N5711
D4: schottky; 1N5711
D5: schottky; 1N5711
D6: schottky; 1N5711
D7: schottky; 1N5711
D8: schottky; 1N5711
L1: ind2; 33µ; Rser=0.0001
L2: ind2; 33µ; Rser=0.0001
L3: ind2; 33µ; Rser=0.0001
L4: ind2; 33µ
L5: ind2; 33µ
L6: ind2; 33µ
L7: ind2; 33µ
L8: ind2; 33µ; Rser=0.0001
LO1: voltage; PULSE(0 2 0 1n 1n {1/(2*f)} {1/f}); Rser=50
R1: res; 50
RF1: voltage; SINE(0 1e-3 108e6); Rser=50
Named nets: 0, IF
.param f=98e6
.inc BAV99.spice.txt
.MODEL DI_SMS3923 D  ( IS=5e-9 RS=10 BV=46 IBV=1e-5
+ CJO=0.9p  M=0.24 N=1.05 TT=8e-11 )
.options numdgt=7
.options plotwinsize=0
.tran 0 14u 4u
K3 L3 L5 1
K4 L4 L6 1
K7 L7 L8 1
K2 L1 L2 1
Communications Receivers Whitaker, fig.6.11
Probably incorrect.  IF has not enough energy to drive the diodes.
Swap IF and LO.
Even after swapping, this doesn't work.
