LieBtrau/MegawattKS_Radio_Design_101/rf-frontend/simulation/antenna_frontend.asc

C1: cap; 100p
C2: cap; 10p
C3: cap; 6p
C4: cap; 10p
C5: cap; 128p
C_Whip1: cap; 12p
C_Whip: cap; 12p
L1: ind; 175n
L2: ind; 45n
R1: res; 50
R2: res; 50
R3: res; 3
R4: res; 50
V1: voltage; 0; AC 1; Rser=5k
V2: voltage; 0; AC 1; Rser=5k
V3: voltage; 0; AC 1; Rser=1000
Named nets: 0, out2, out1, out3
.ac dec 101 50meg 500meg
Whip antenna directly to 50ohm input
Antenna impedance matching circuit and resonator : signal 10dB stronger
Antenna
Matching network
