LieBtrau/MegawattKS_Radio_Design_101/IF1_mixer/simulation/ringmod_vs_switcher.asc

C1: cap; 100n
C2: cap; 330p
D1: schottky; 1N5819
D2: schottky; 1N5819
D3: schottky; 1N5819
D4: schottky; 1N5819
L1: ind2; 33µ
L2: ind2; 33µ
L3: ind2; 33µ
L4: ind2; 33µ
L5: ind2; 33µ
L6: ind2; 33µ
L7: ind; 820n
LO1: voltage; PULSE(0 1 0 1n 1n {1/(2*f)} {1/f}); Rser=50
LO2: voltage; PULSE(0 3 0 1n 1n {1/(2*f)} {1/f}); Rser=50
M1: nmos; BSS138P
R1: res; 50
R2: res; 50
R3: res; 50
RF1: voltage; SINE(0 1e-3 10e6)
RF2: voltage; SINE(0 1e-3 10e6); Rser=50
Named nets: 0, IF1, IF2
K1 L1 L2 L3 1
K2 L4 L5 L6 1
.tran 0 20e-6 1e-6 1e-11
.options numdgt=7
.options plotwinsize=0
.inc BSS138P_2011.txt
.param f=8.8e6
fft(V(IF1)) : LO1 and RF1 30dB below IF1
fft(V(IF2)) : LO2 44dB ABOVE IF2!
