LieBtrau/MegawattKS_Radio_Design_101/LO/simulation/Seiler.asc

C1: cap; 10n
C2: cap; 10n
C3: cap; 82p
C4: cap; 220p
C5: cap; 18p
C6: cap; 18p
C7: cap; 10p
C8: cap; 100n
C9: cap; 10n
C10: cap; 10n
L1: ind; 6.8µ
L2: ind; {2*6.8µ}
M1: nmos; BSS138P
Q1: npn; 2N3904
Q5: npn; 2N3904
R1: res; 4.7k
R2: res; 22k
R3: res; 1
R4: res; 2.2k
R5: res; 1.2k
R6: res; 100
R7: res; 100
R8: res; 1.5k
R9: res; 100
R12: res; 4.7k
R13: res; 1.8k
R20: res; 100
V1: voltage; 5
Named nets: 0, osc_out, 5V
EMRFD, Fig. 4.11
;.op
.tran 0 220u 210u uic
.inc BSS138P_2011.txt
.lib OptiMOS2_20V_LTSpice.lib
.param first_edge=1 ; 200th edge
.param last_edge=50 ; 700th edge
.param zero_crossing_voltage=1.5 ; voltage at zero crossing
.meas tran T1 find time when V(osc_out)={zero_crossing_voltage} rise {first_edge}
.meas tran T2 find time when V(osc_out)={zero_crossing_voltage} rise {last_edge}
.meas tran Frequency param ({last_edge}-{first_edge})/(T2-T1)
Class A amplifier EMRFD fig. 2.34
