LieBtrau/MegawattKS_Radio_Design_101/IF2_amp/simulation/AlanYatesAdventCalendar2014.asc

C3: cap; 10n
C4: cap; 100n
C5: cap; 10n
C9: cap; 470p
C10: cap; 100p
Q1: npn; 2N3904
Q2: npn; 2N3904
Q3: npn; 2N3904
R1: res; 1k
R2: res; 1k
R3: res; 1k
R4: res; 56k
R5: res; 47k
R6: res; 100k
V1: voltage; 3
V2: voltage; SINE(0 100u 100e3); AC 0
Named nets: 0
.tran 100u
;ac dec 1meg 1k 10meg
At least 100µV signal is needed, or it will oscillate.
Looks simple, but might be hard to control.
His 2010 design looks easier to manipulate and to control.
