LieBtrau/MegawattKS_Radio_Design_101/IF2_amp/simulation/complicated_IF_amp_cascade.asc

C1: cap; 100n
C2: cap; 100n
C3: cap; 100n
C4: cap; 100n
C5: cap; 10n
C6: cap; 100n
C7: cap; 10n
C8: cap; 10n
C9: cap; 10n
C10: cap; 10n
C11: cap; 100n
C12: cap; 100n
C13: cap; 10n
C14: cap; 10n
C15: cap; 100n
Q1: npn; 2N3904
Q2: npn; 2N3904
Q3: npn; 2N3904
Q4: npn; 2N3904
R1: res; 3.6k
R2: res; 1.5k
R3: res; 51
R4: res; 120
R5: res; 10
R6: res; 3.6k
R7: res; 1.5k
R8: res; 470
R9: res; 22
R10: res; 120
R11: res; 22
R12: res; 22
R13: res; 3.6k
R14: res; 1.5k
R15: res; 470
R16: res; 22
R17: res; 120
R18: res; 22
R19: res; 22
R20: res; 3.6k
R21: res; 1.5k
R22: res; 120
Rout: res; 10k
V1: voltage; 5
Vin: voltage; SINE(0 55e-3 {f}); AC 1; Rser=50
Named nets: 0
.net I(Rout) Vin
.ac dec 1001 10k 100meg
;.op
;tran 0 1m 0
.param f=200e3
.options numdgt=7
.options plotwinsize=0
.four {f} V(out) 10 100
