LieBtrau/MegawattKS_Radio_Design_101/IF2_amp/simulation/PhilsValve.asc

C1: cap; 22n
C2: cap; 1n
C3: cap; 100µ
C4: cap; 22n
C5: cap; 10n
Q1: npn; BC547B
Q2: npn; BC547B
R1: res; 390
R2: res; 1.5k
R3: res; 680k
R4: res; 2.2k
R5: res; 2.2Meg
R6: res; 220
R7: res; 4.7k
R8: res; 100k
V1: voltage; 9
V2: voltage; SINE(0 10m 100e3); AC 1
Named nets: 0
From https://www.philsvalveradiosite.co.uk/recorrectedcircuitdiagramofifamplifier.jpg
Amplifies 200x (46dB) at 200kHz.  So cascading two of these stages yields 92dB of amplification.
.ac dec 1meg 1k 100meg
First stage 35dB gain, second stage 15dB gain.
