LieBtrau/MegawattKS_Radio_Design_101/IF2_mixer/simulation/switching_mixer.asc

C1: cap; 130p
C2: cap; 240p
C3: cap; 1.8n
C4: cap; 4.35n
C5: cap; 1.45n
C6: cap; 2.9n
L1: ind; 10µ
L2: ind; 18µ
L3: ind; 1.2µ
L4: ind; 4.08µ
L5: ind; 8.16µ
L6: ind; 2.72µ
M1: nmos; BSS138P
M2: nmos; BSS138P
R1: res; 50
R2: res; 50
R3: res; 50
R4: res; 50
V1: voltage; SINE(0 2 10.7meg)
V2: voltage; PULSE(0 3 0 1n 1n {0.5/fsw} {1/fsw})
Named nets: 0, LF, LF2
;.ac dec 1meg 1k 100meg
 
.inc mlf2012c270kt000_s.mod
.inc mlf2012c180kt000_s.mod
.inc BSS138P_2011.txt
 
.options numdgt=7
.options plotwinsize=0
.param fsw=10.5e6
Third order high pass, low pass diplexer calculated with markimicrowave.
High pass, Zin=50ohm, Zout=100ohm, fco=10MHz
Low pass, Zin=100ohm, Zout=50ohm, fco=1MHz
Switching mixer (EMRFD p.5.4)
.tran 0 50u 10u 100p
.net I(R2) V1
.inc mlf2012c270kt000_s.mod
.inc mlf2012c180kt000_s.mod
Cross over frequency is 1.5MHz, 3rd order diplexer according to EMRFD p3.38.
