LieBtrau/MegawattKS_Radio_Design_101/audio_amplifier/simulation/de-emphasis.asc

C1: cap; 22n
R1: res; 3.3k
V1: voltage; ""; AC 1
Named nets: 0
.ac dec 1meg 1 100k
De-emphasis is LPF with RC = 75µs, which corresponds to fc=2.122kHz
