LieBtrau/MegawattKS_Radio_Design_101/detector/simulation/SallenKey_20kHz.asc

C1: cap; 100n
C2: cap; 270p
C3: cap; 1.5n
C4: cap; 270p
C5: cap; 100n
C6: cap; 1n
C7: cap; 1.5n
Q1: npn; 2N3904
Q2: npn; 2N3904
R1: res; 470k
R2: res; 470k
R3: res; 5.1k
R4: res; 10k
R5: res; 2.2k
R8: res; 7.5k
R9: res; 470k
R10: res; 470k
R11: res; 5.1k
R12: res; 10k
R13: res; 2.2k
V1: voltage; PULSE(0 5 0 1n 1n 2.6µ {1/f}); AC 1
V2: voltage; 5
Named nets: 0, out
.tran 100m
;.ac dec 1meg 1 1meg
.param f=300e3
