LieBtrau/MegawattKS_Radio_Design_101/IF1_amp/simulation/IF3.asc

C1: cap; 10n
C2: cap; 10n
C3: cap; 10n
C4: cap; 10n
C5: cap; 33p
C6: cap; 10n
C7: cap; 10n
L1: ind; 4.7µ
Q1: npn; 2N3904
Q2: npn; 2N3904
Q3: npn; 2N3904
R1: res; 1k
R2: res; 10k
R3: res; 10k
R4: res; 220
R5: res; 24k
R6: res; 10
R7: res; 1.2k
Rout: res; 50
V1: voltage; 5
V2: voltage; SINE(0 1m 10.7e6); AC 1; Rser=50
Named nets: 0, out
;tran 10u
300ohm input impedance
Choose R1 so that collector of Q1 is halfway between base of Q1 and VCC for bias.
High input impedance, low output impedance because of the buffer.
.op
.ac dec 1001 1meg 100meg
.net I(Rout) V2
